EIectron/RadioNoob/Images/Transmitter/IMG20240410154644.jpg

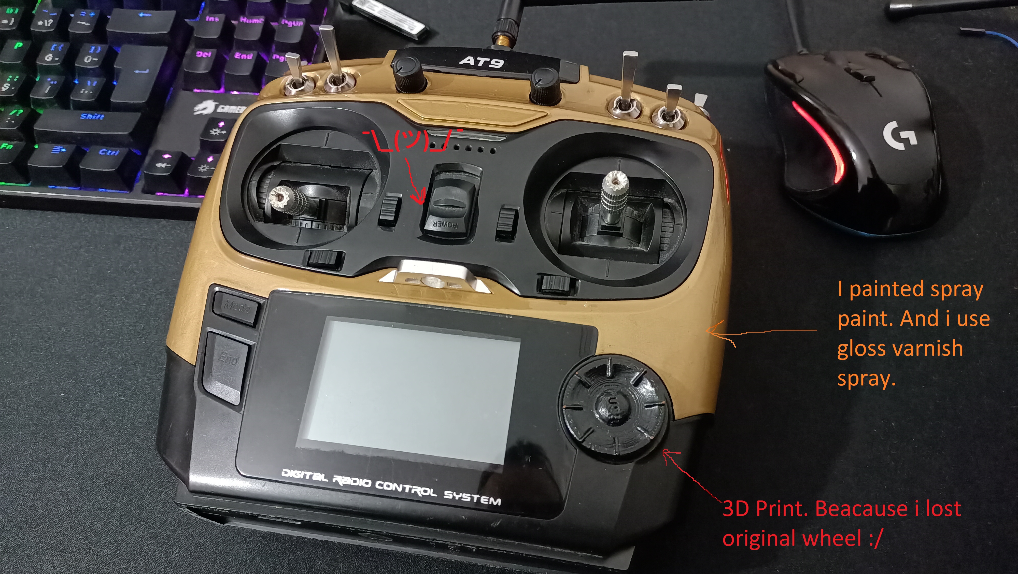
Images/Transmitter/IMG20240410154644.jpg
