EIectron/RadioNoob/Images/Transmitter/IMG20240410155039.jpg

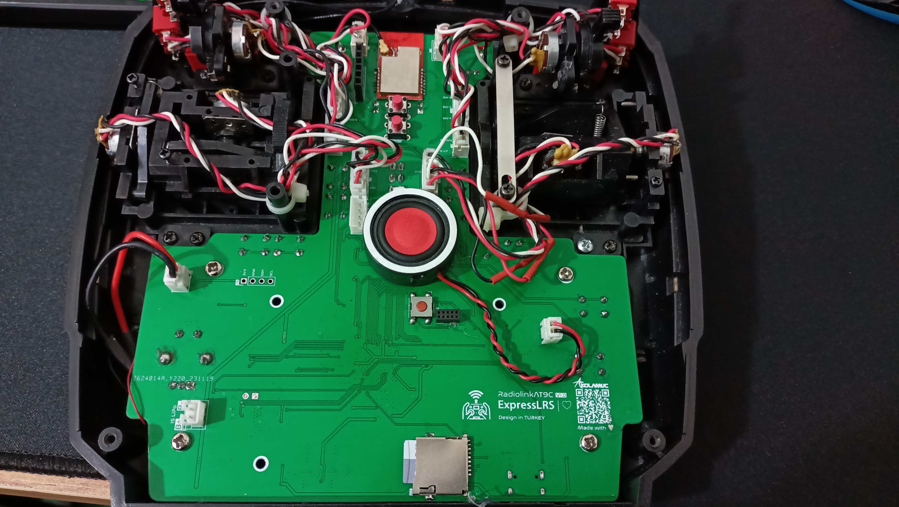
Images/Transmitter/IMG20240410155039.jpg
