EIectron/RadioNoob/Images/Transmitter/IMG20240410155045.jpg

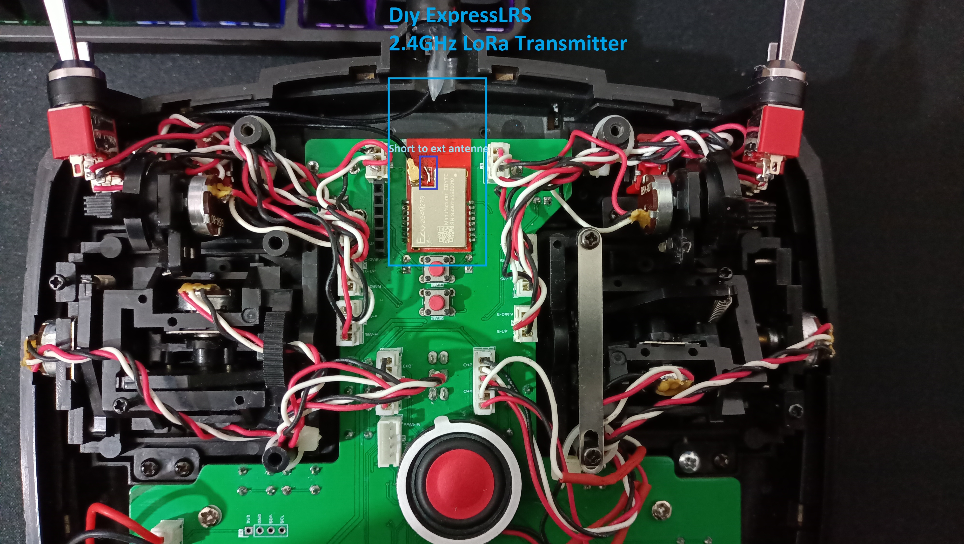
Images/Transmitter/IMG20240410155045.jpg
