EIectron/RadioNoob/Images/Transmitter/IMG20240410155447.jpg

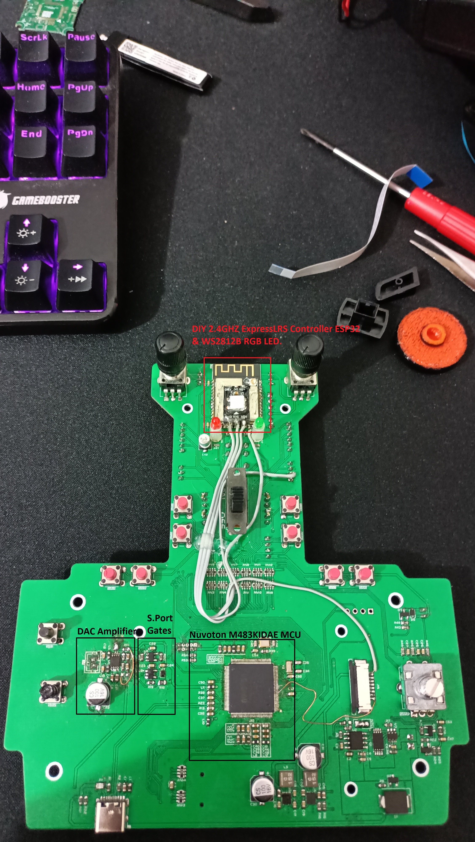
Images/Transmitter/IMG20240410155447.jpg
