EIectron/RadioNoob/Images/Transmitter/IMG20240410155505.jpg

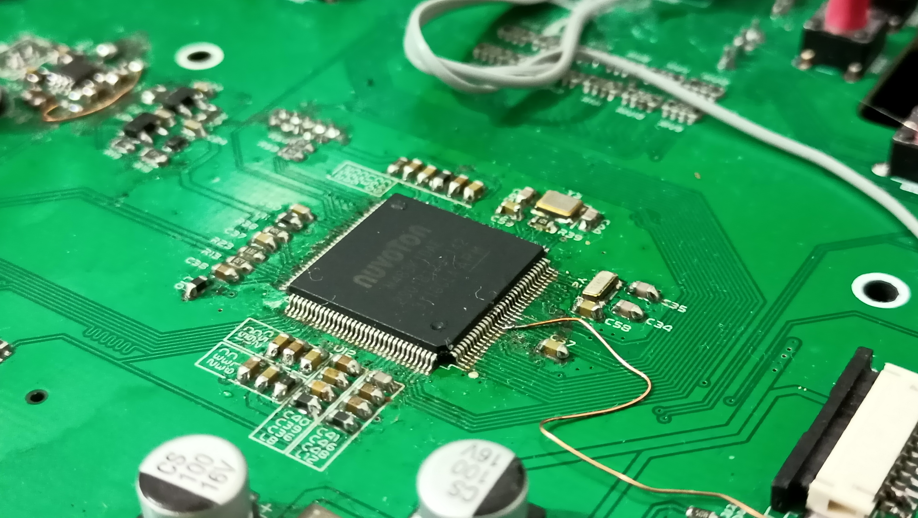
Images/Transmitter/IMG20240410155505.jpg
