EIectron/RadioNoob/Images/Transmitter/IMG20240410155515.jpg

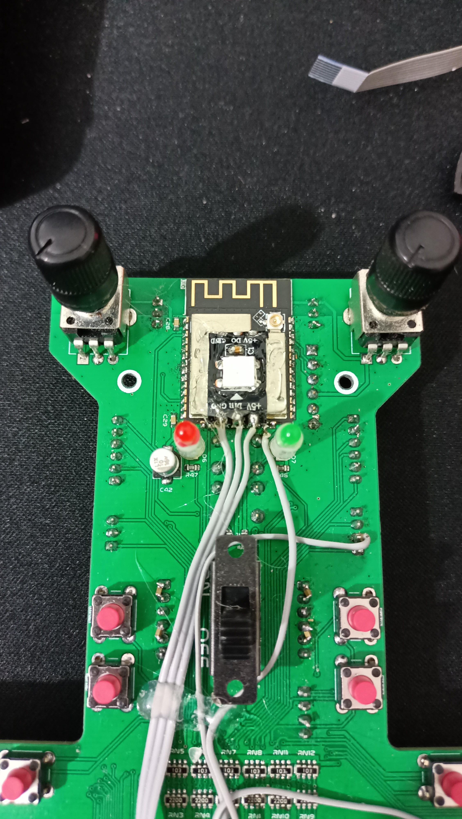
Images/Transmitter/IMG20240410155515.jpg
