EIectron/RadioNoob/Images/Transmitter/IMG20240410155539.jpg

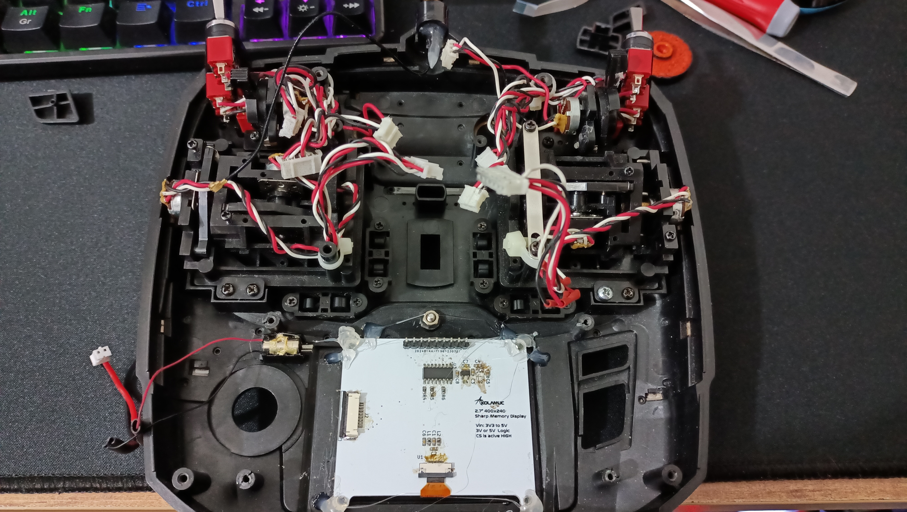
Images/Transmitter/IMG20240410155539.jpg
