EIectron/RadioNoob/Images/Transmitter/IMG20240410155607.jpg

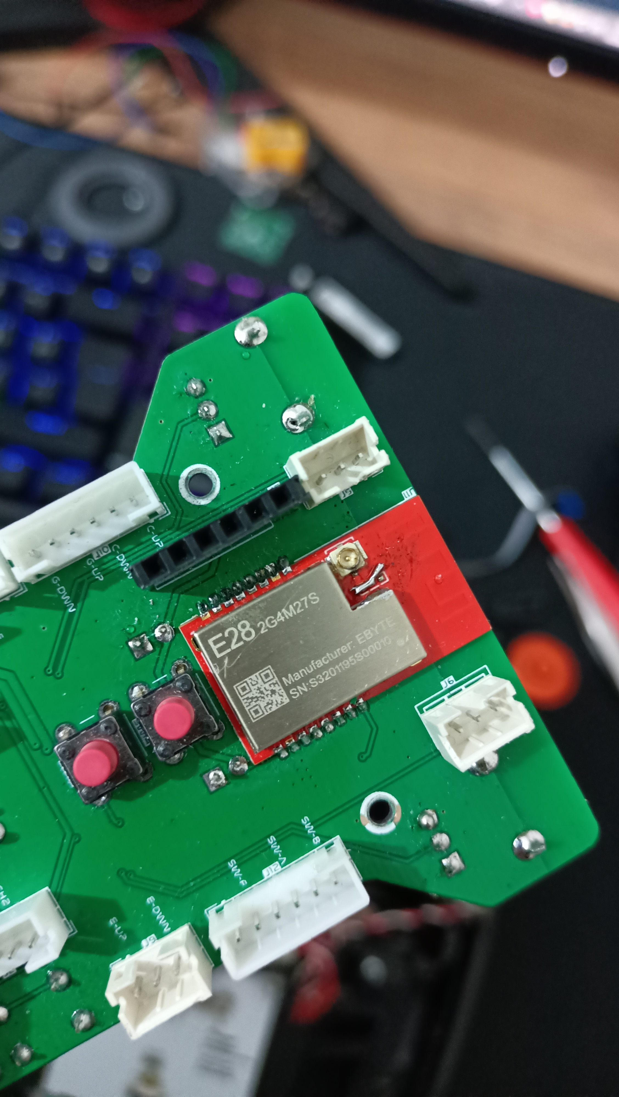
Images/Transmitter/IMG20240410155607.jpg
