EIectron/RadioNoob/Images/Transmitter/IMG20240410155912.jpg

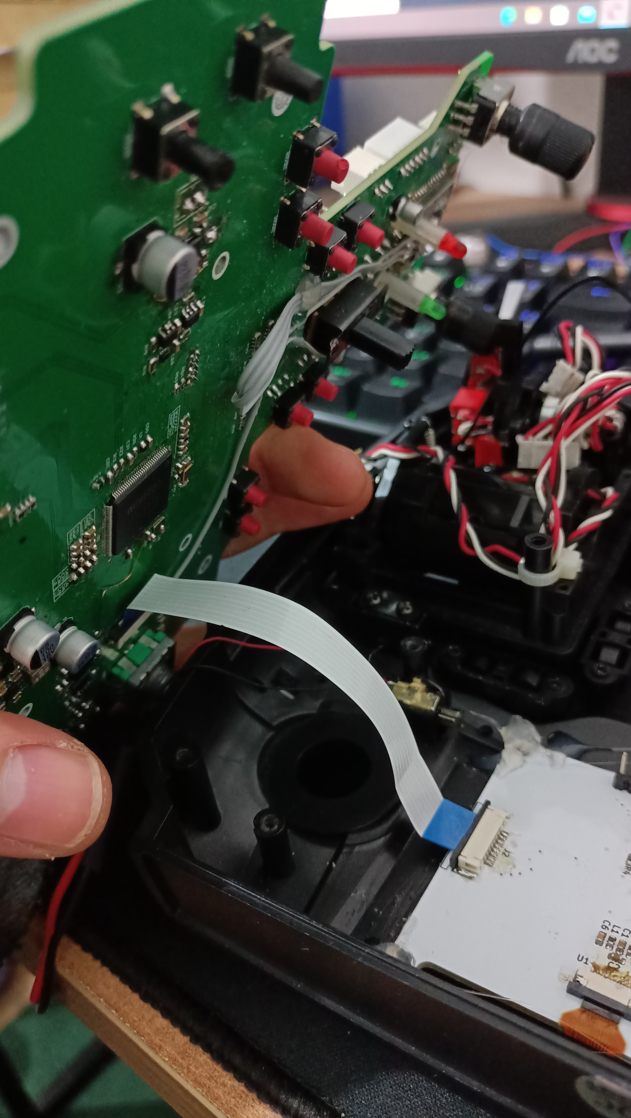
Images/Transmitter/IMG20240410155912.jpg
