EIectron/RadioNoob/Images/Transmitter/IMG20240410161644.jpg

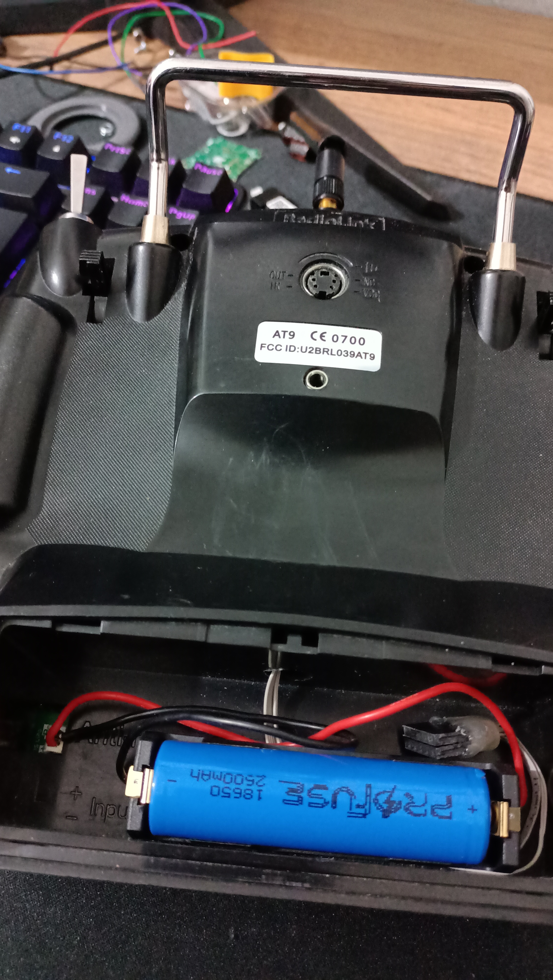
Images/Transmitter/IMG20240410161644.jpg
