EIectron/RadioNoob/Hardware/Documents/TX16S v2 schematic single page PDF.pdf

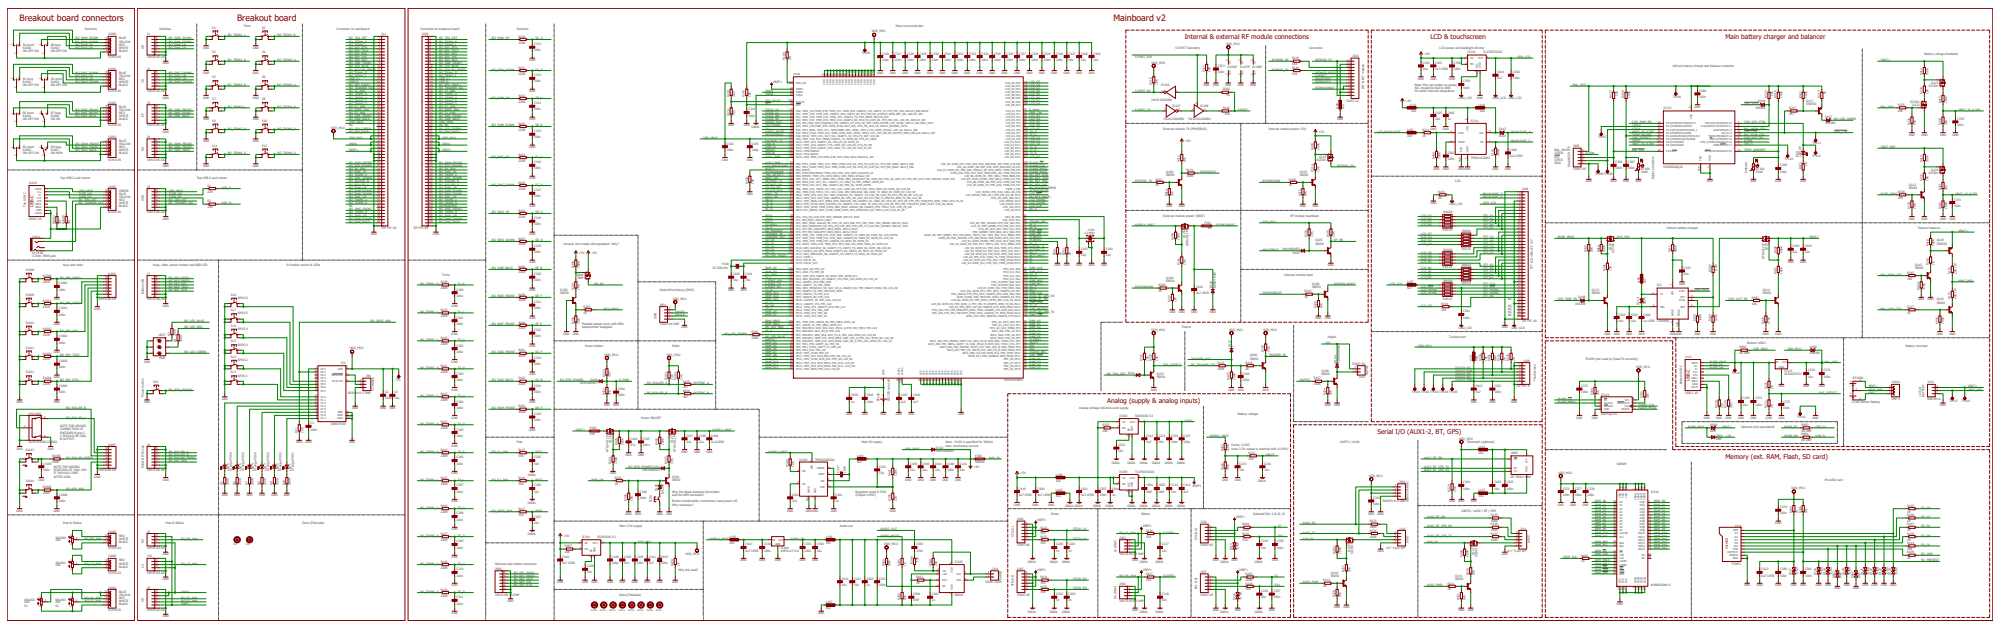
[picture p48: page 1]

AB CDSC long SD short

LCD power and backlight dimmer

Lithium battery charge and balance controller

GND
Note: this cap makes no sense,
N/C should be tied to GND

for better thermal dissipation.

BALANCER ICP GND ICPCK RST ICPDA BAL_VDD

Top USB-C and trainer

RS LS VR USB

Unused, but mostly still populated. Why?

Keys, roller, power button and RGB-LED

Roller & MDL key Buttons left

Serial-Wire-Debug (SWD)

Possible design error with NPN,

FLASH (not used by OpenTX currently)

Analog (supply & analog inputs)

Analog voltage reference and supply

Factor: 0.245
(max 3.3V output is reached with 13.45V)

Memory (ext. RAM, Flash, SD card)

GND 5 VIN 8 VBST 7 SW 6 IC103

VDD 27 VSS 41 A11 35 NC 36 CKE 37 CLK 38 NC 40 UDQM 39

Why the diode between the button
and the NPN transistor?
Button functionality: momentary hard power off.
Why necessary?

LS (DNP) RS (DNP)

Optional side button connector

VDD 6 GND 7 -IN 4 +IN 3 BYP 2 SD 1 VO1 5 VO2 8 IC105 C431 C211 C402 C352
