EIectron/RadioNoob/Hardware/Documents/L-KLS1-207-2-10-S.PDF

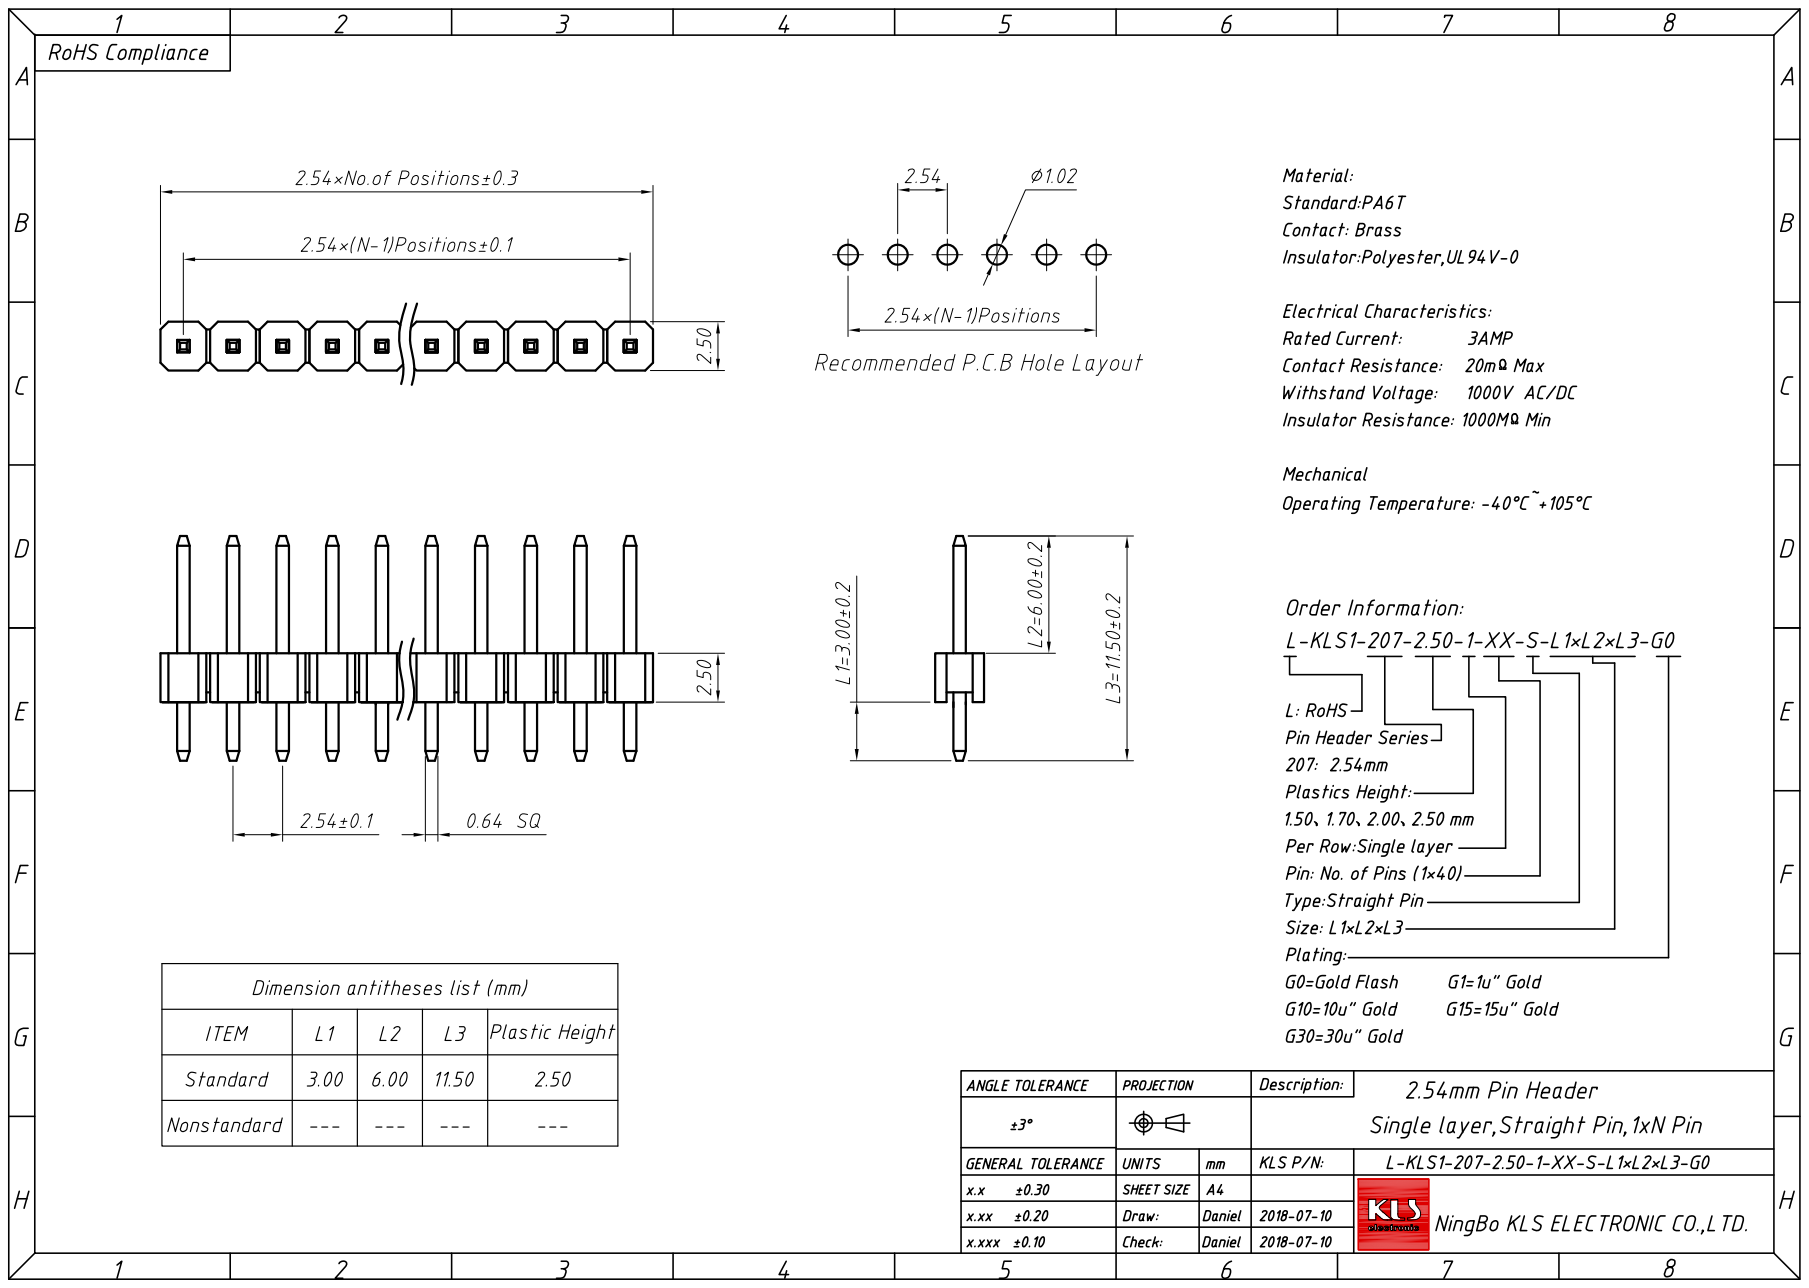
[picture p61: page 1]

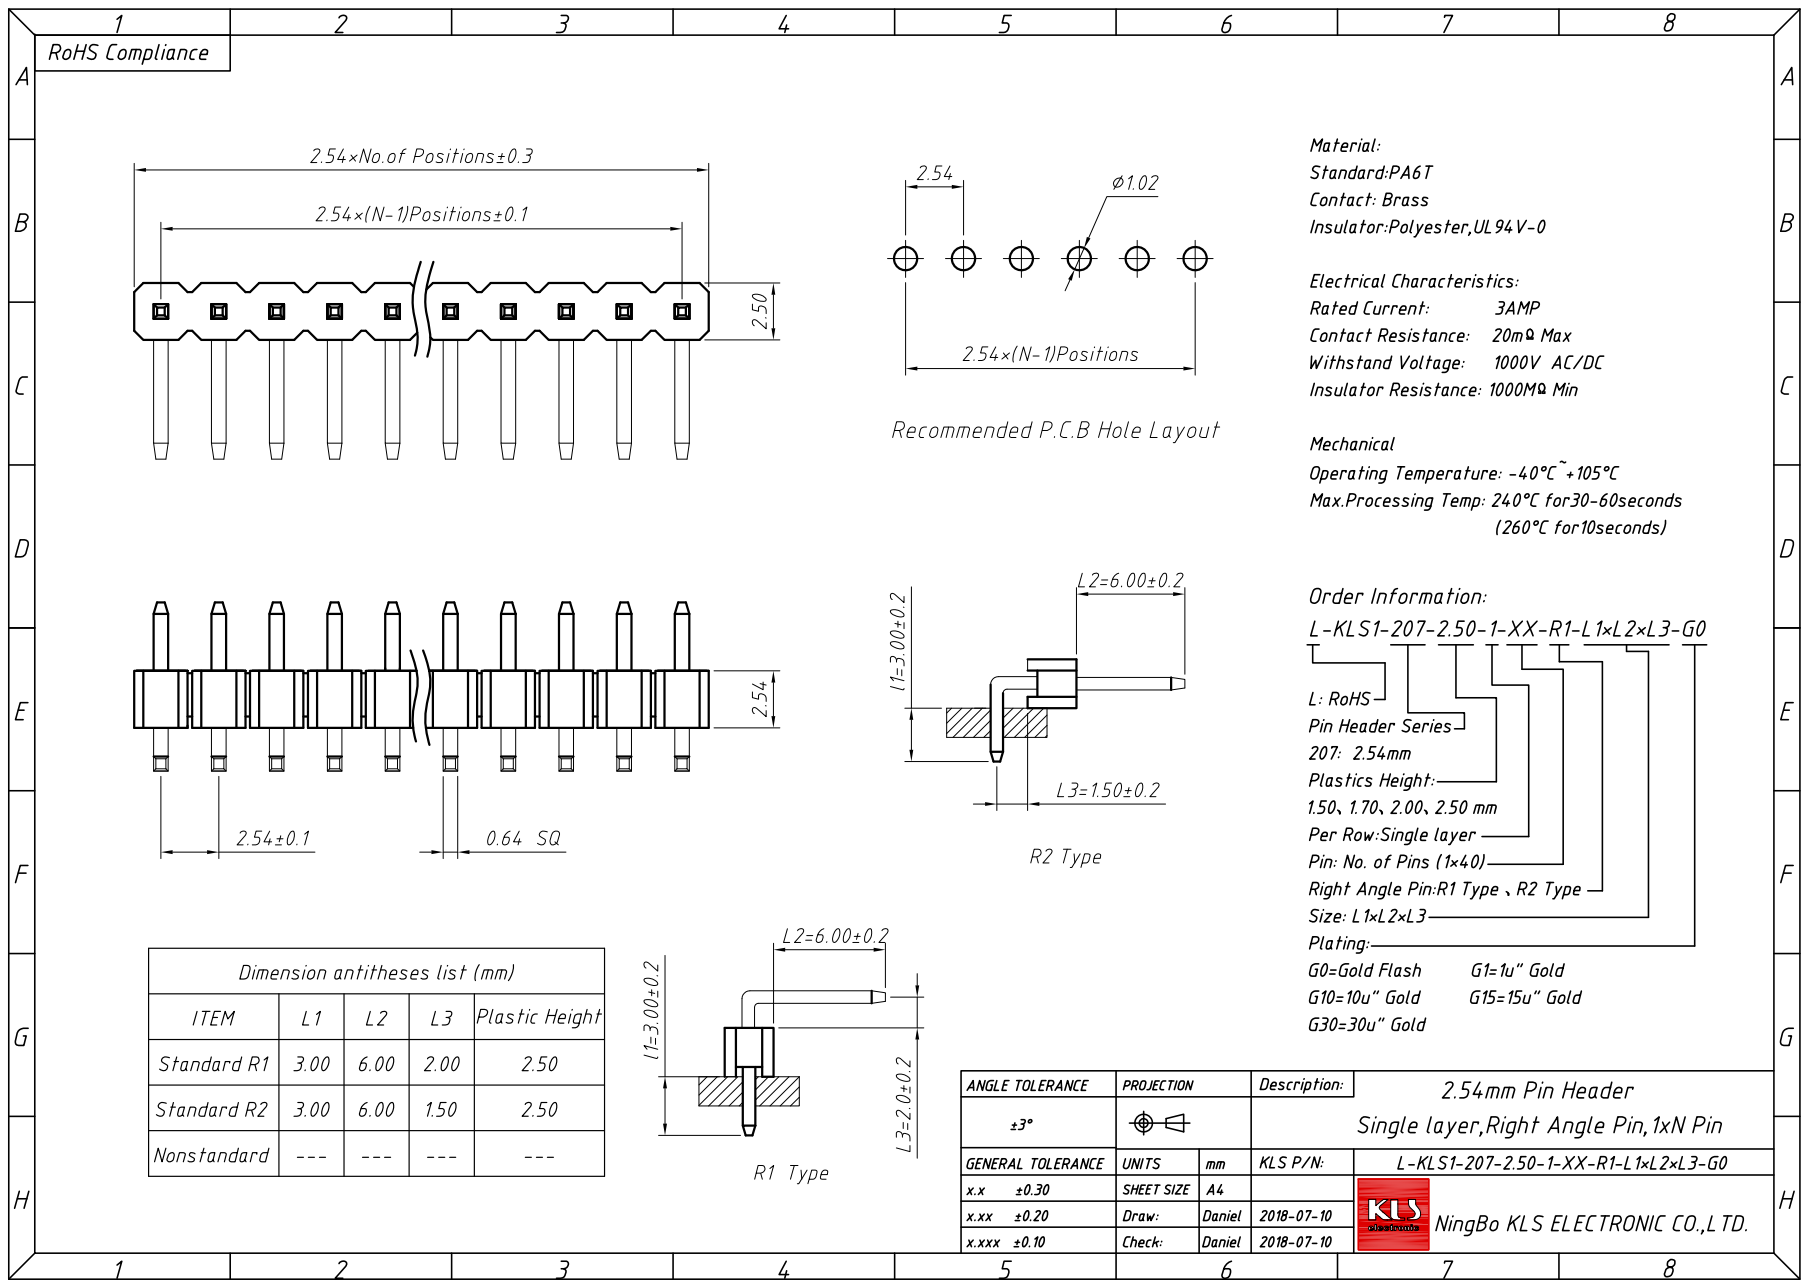
[picture p62: page 2]

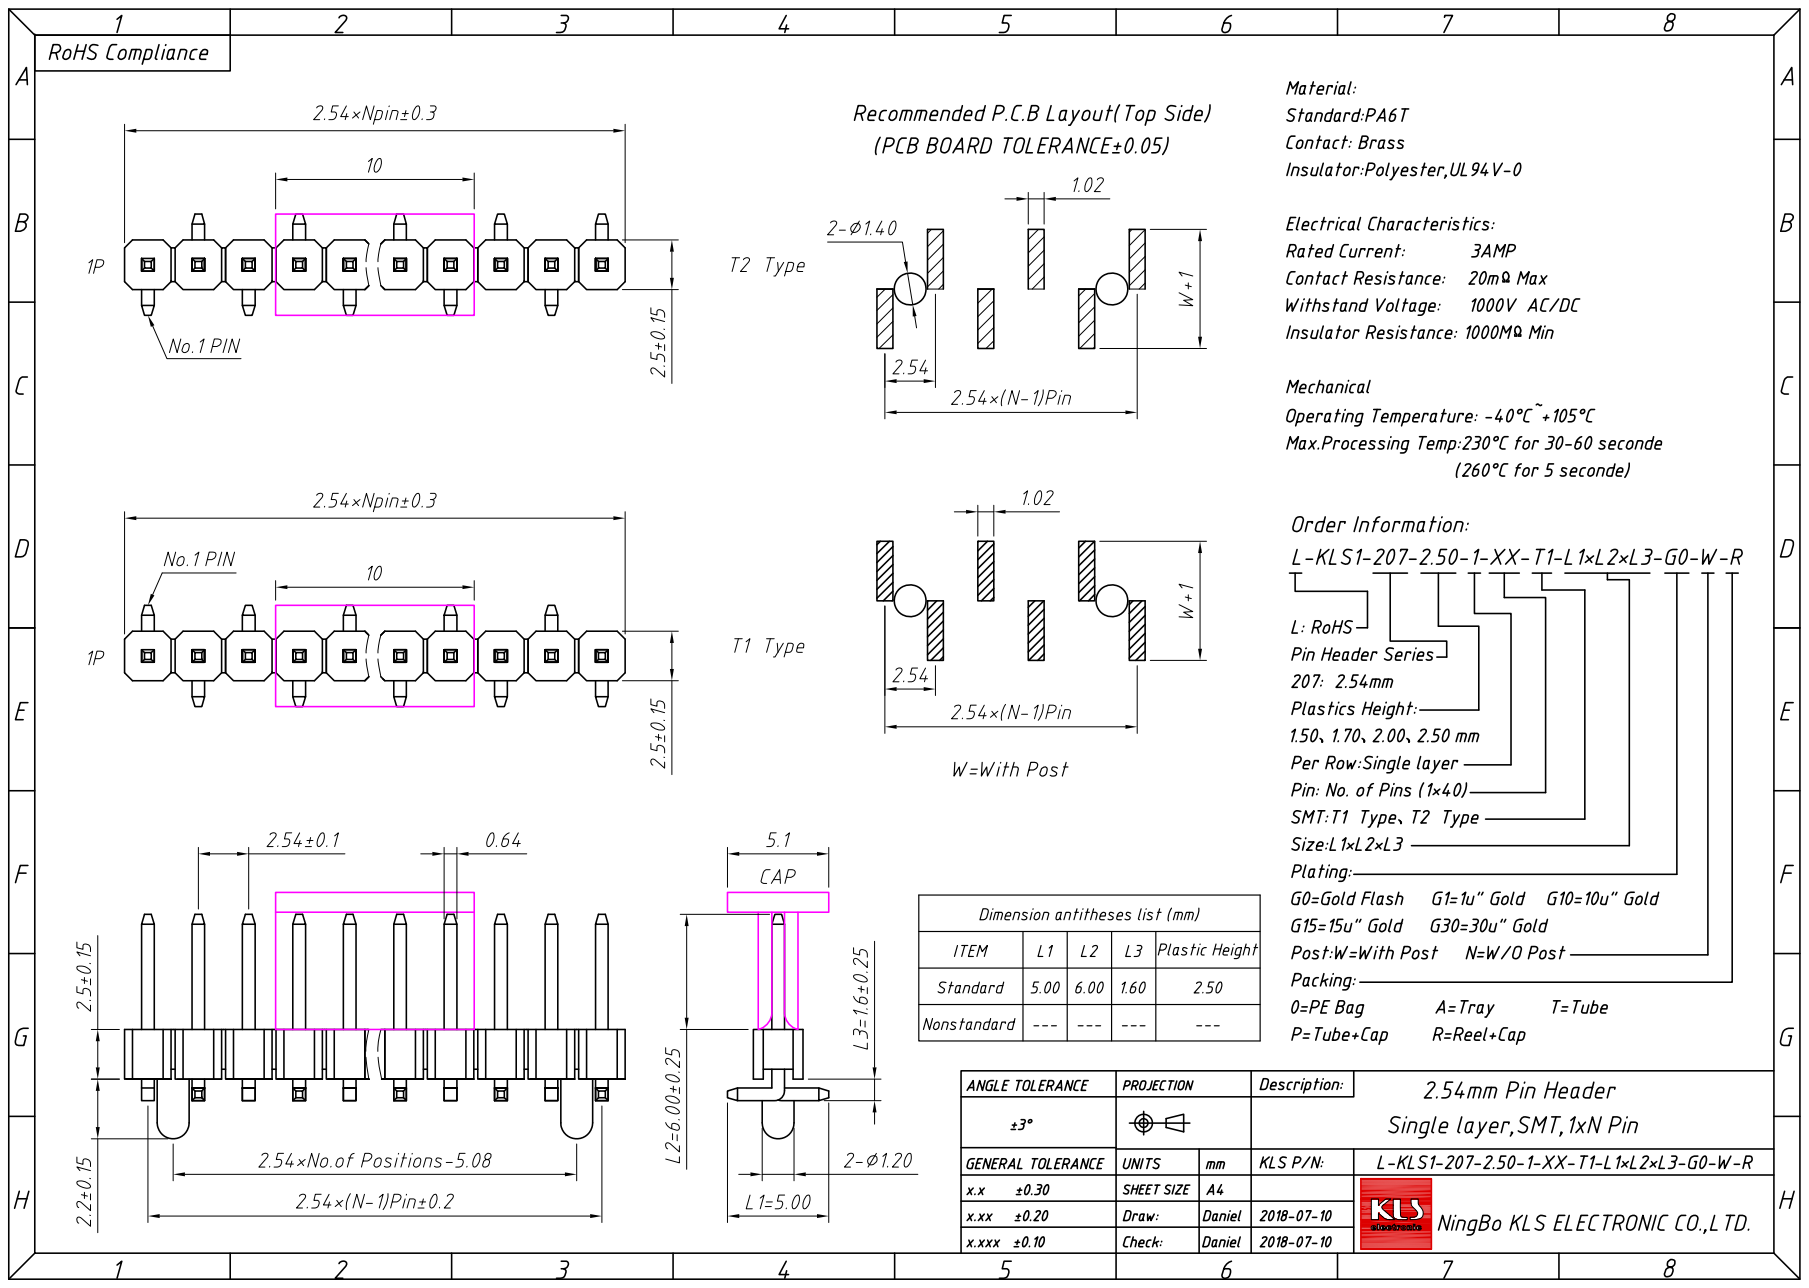
[picture p63: page 3]

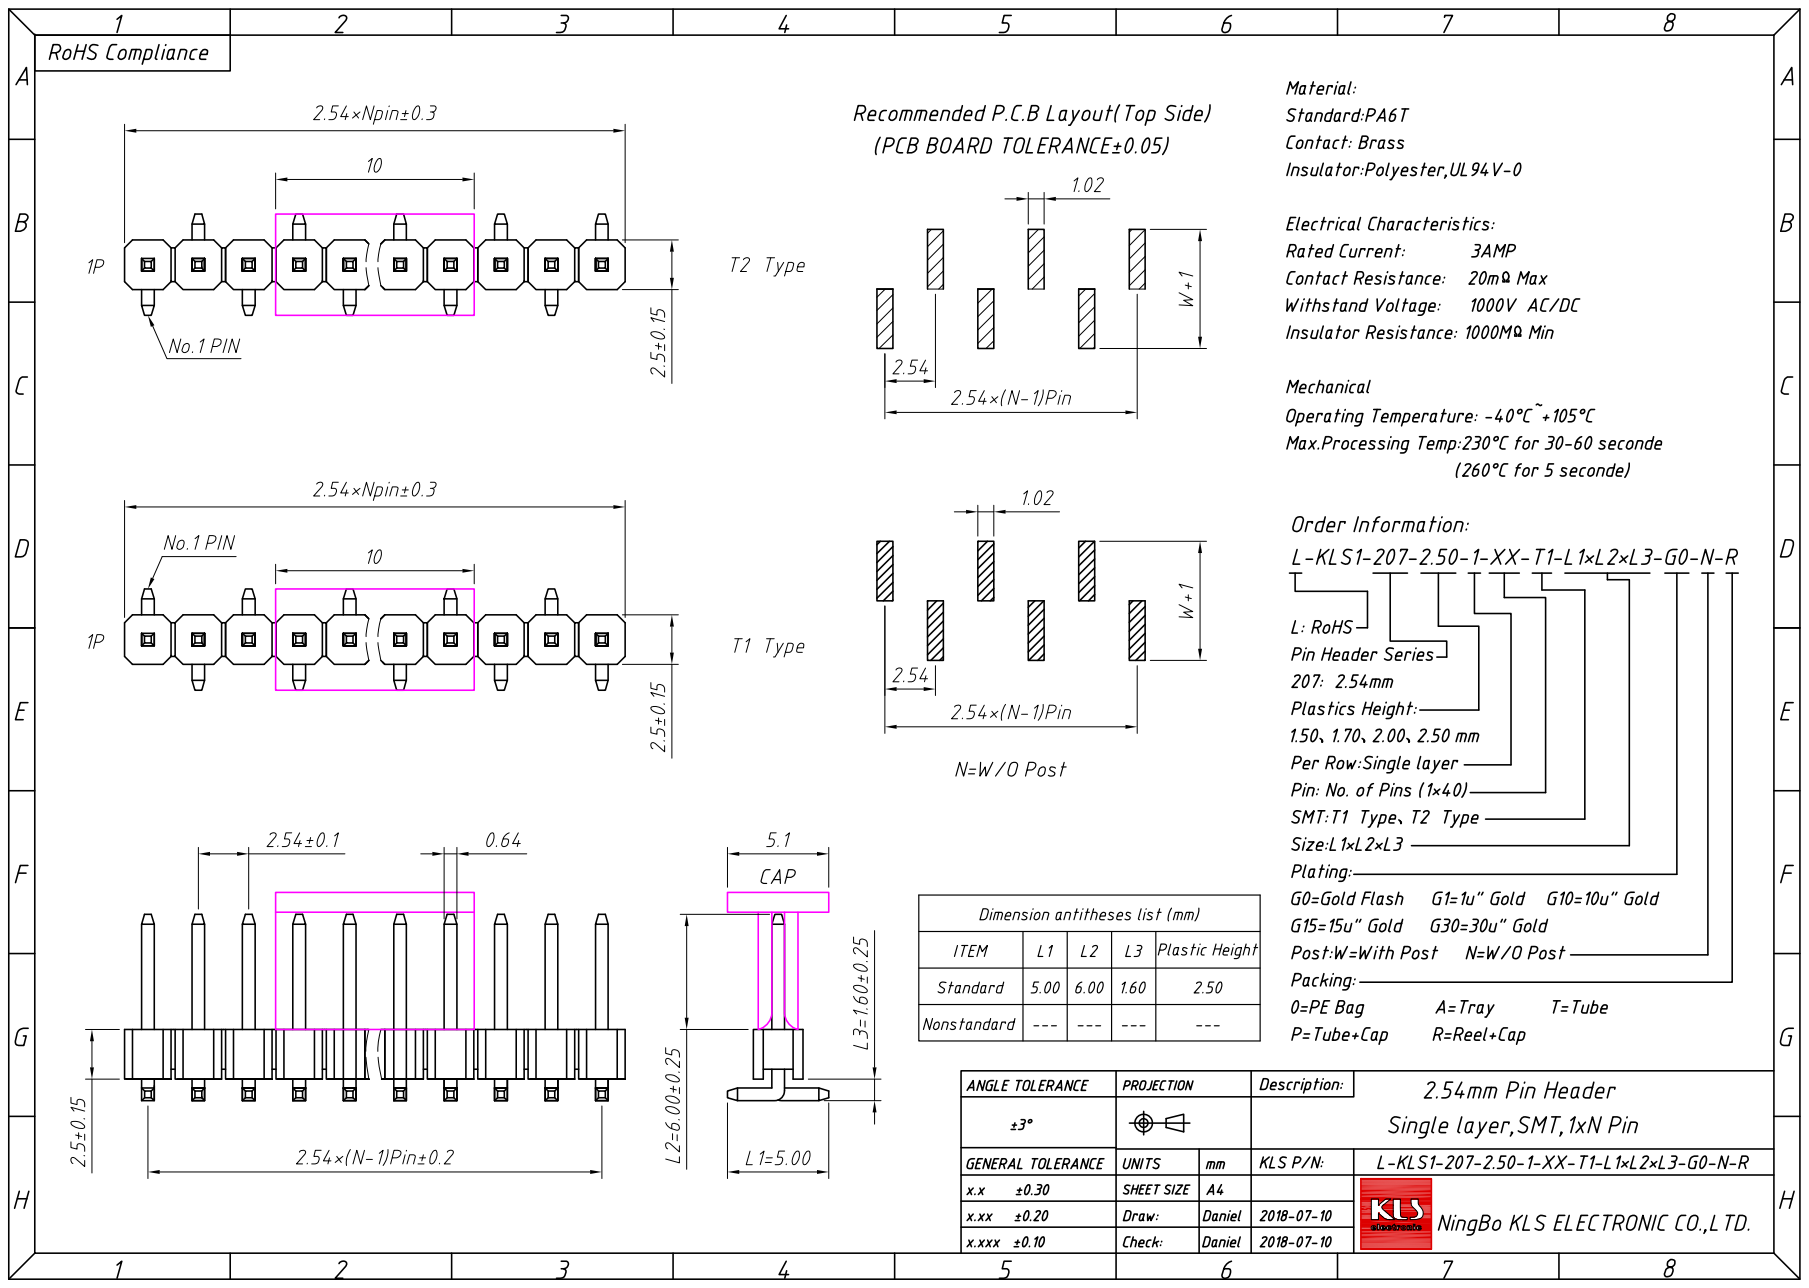
[picture p64: page 4]

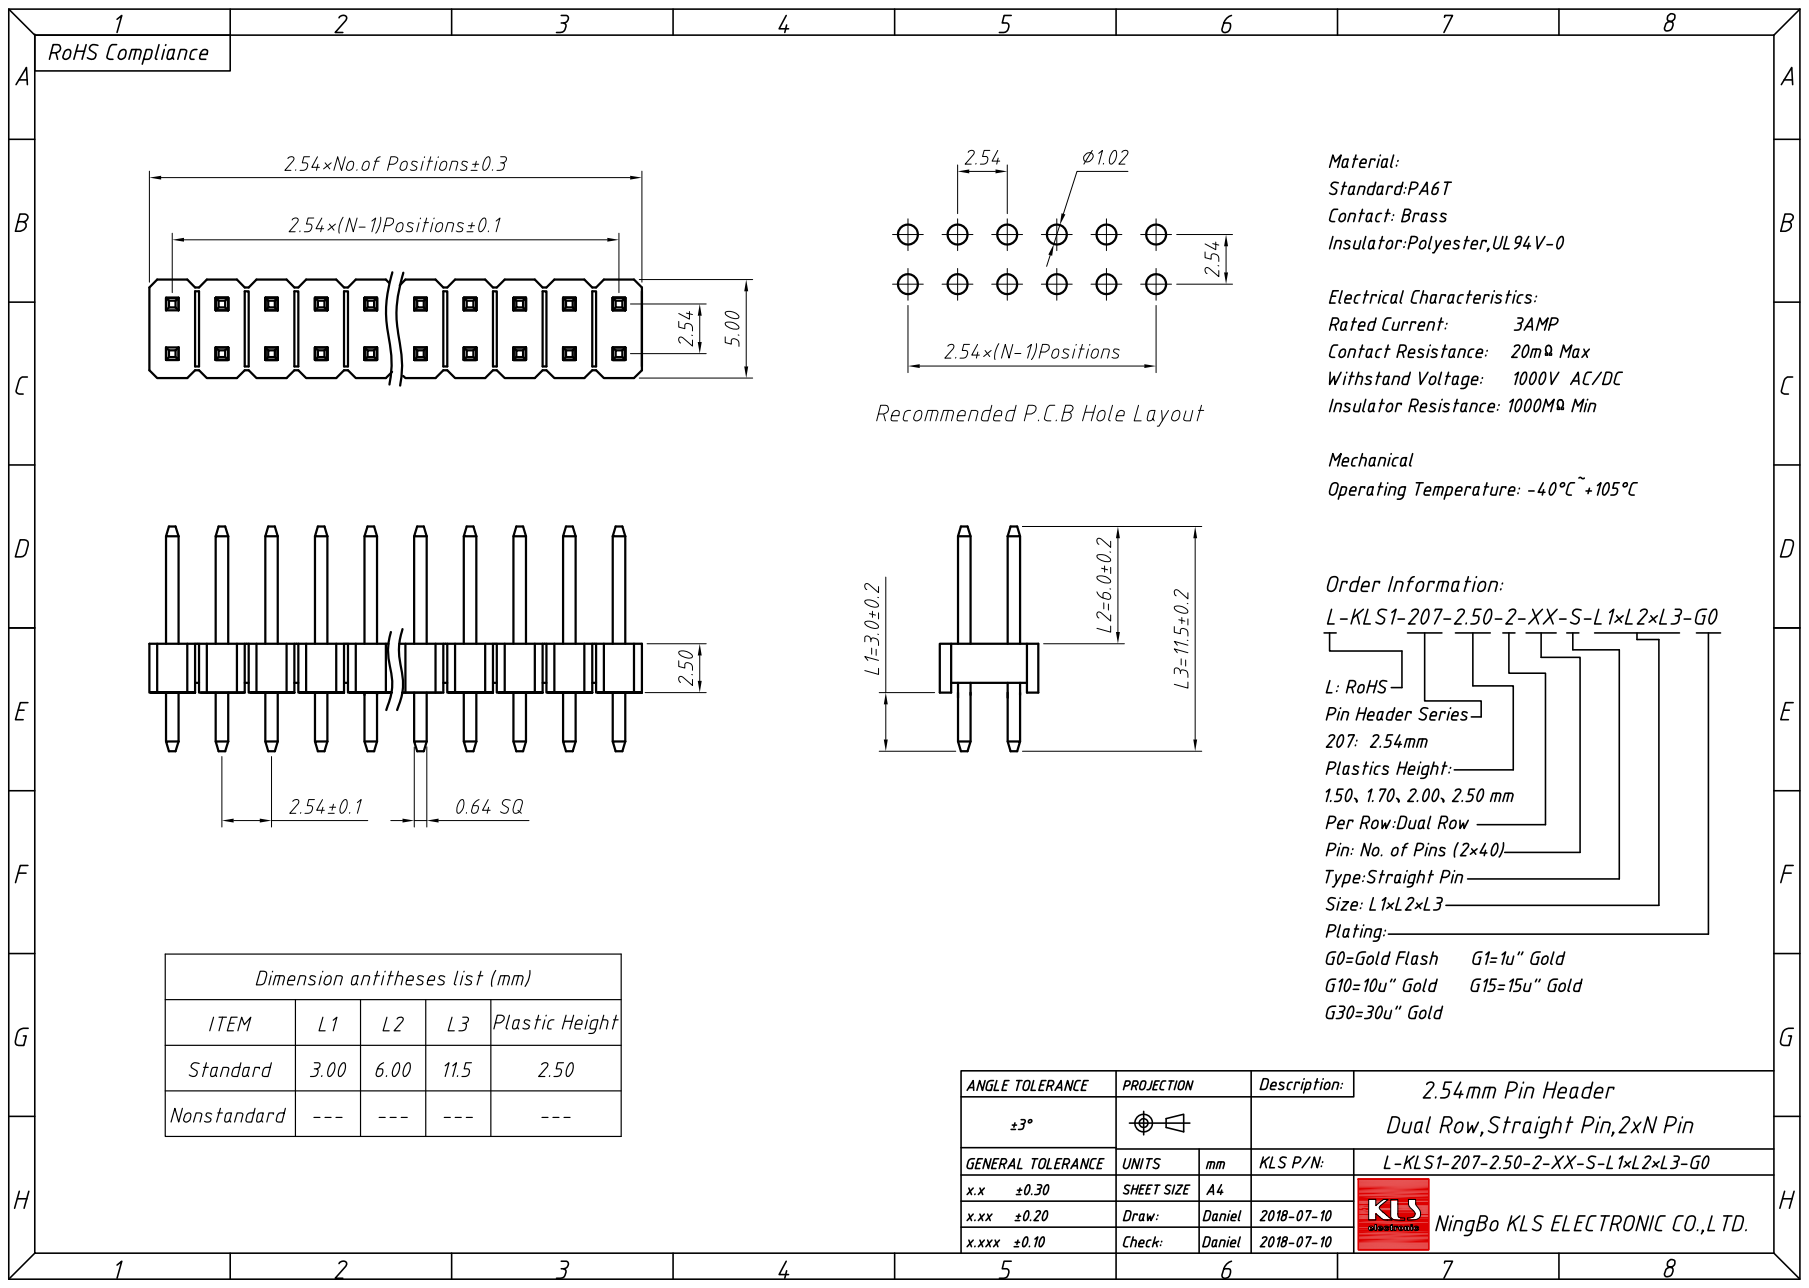
[picture p65: page 5]

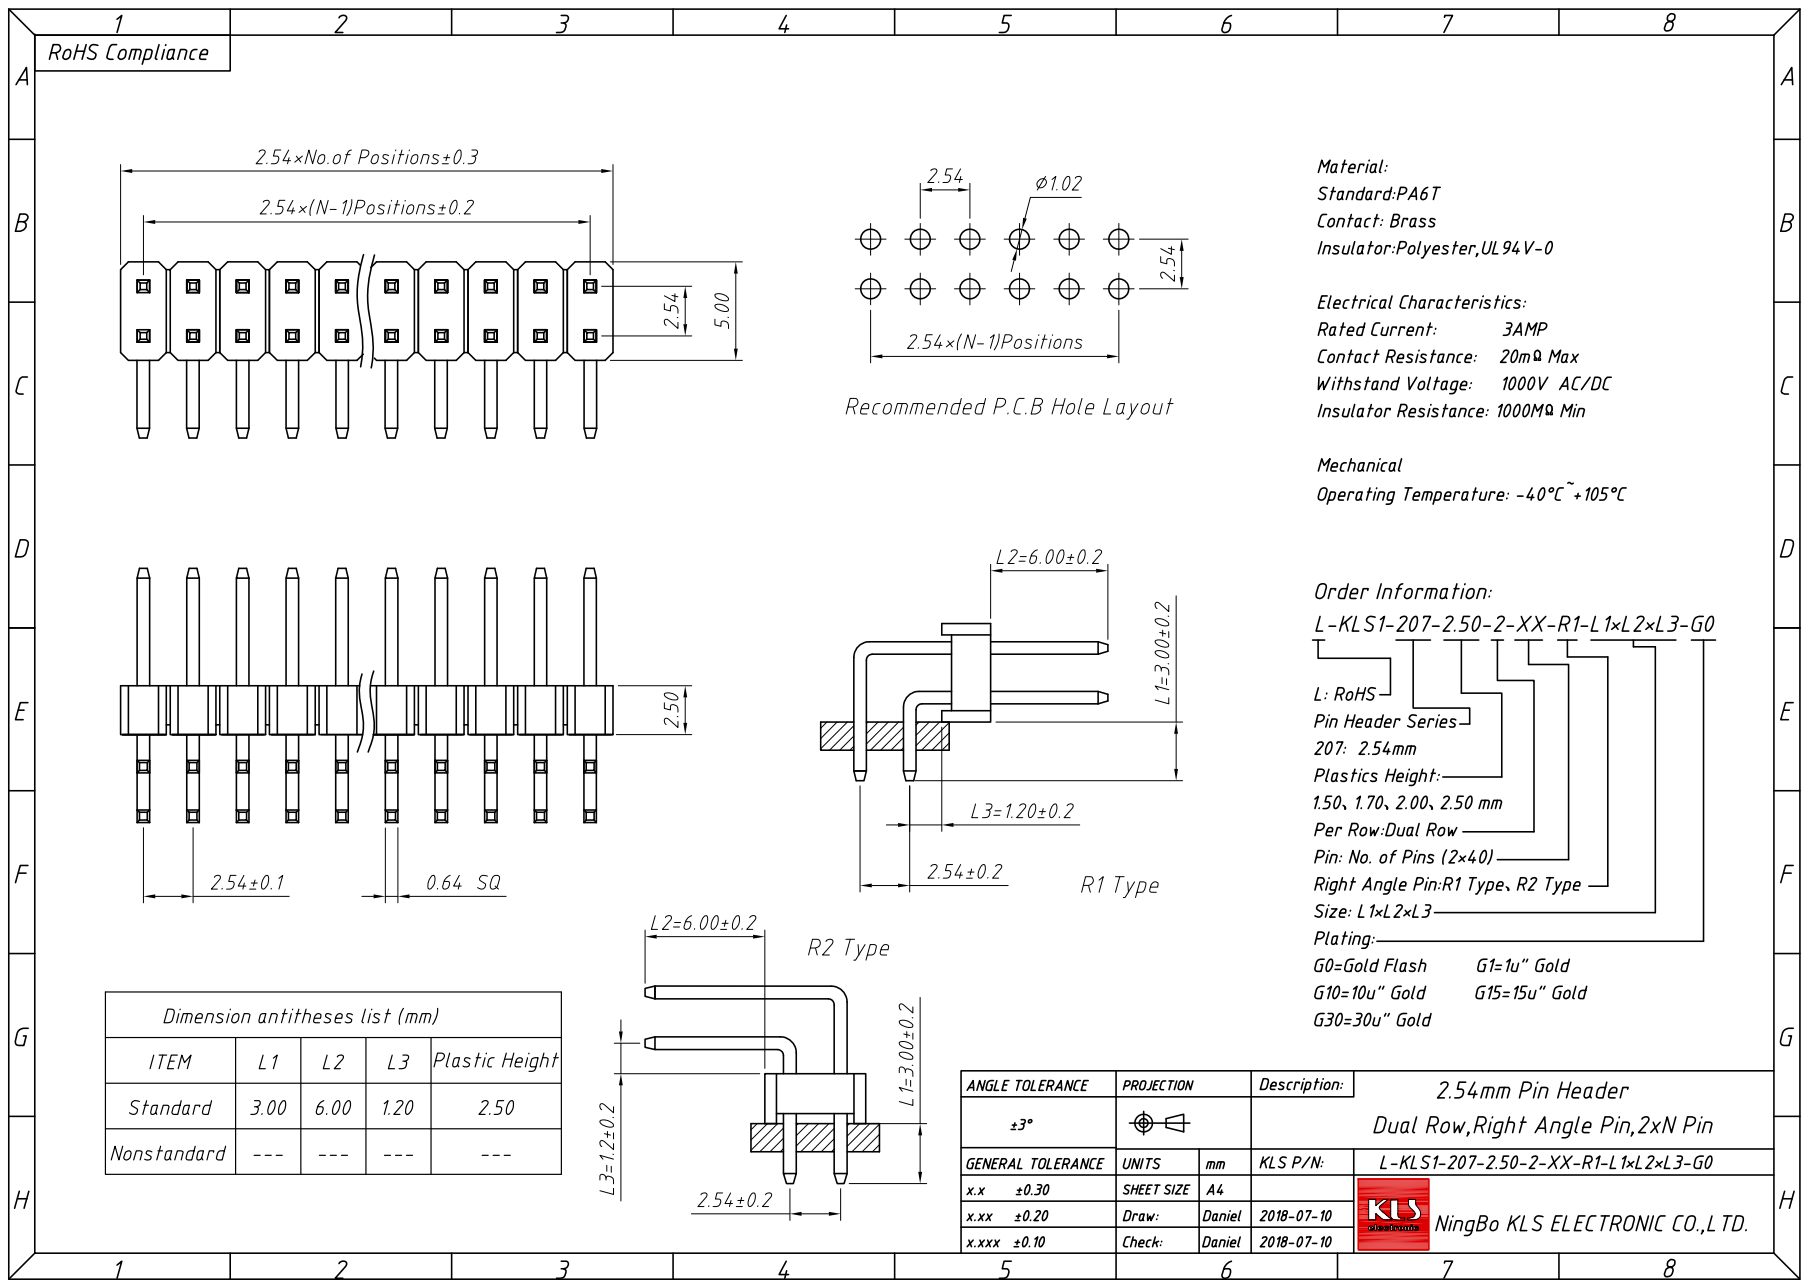
[picture p66: page 6]

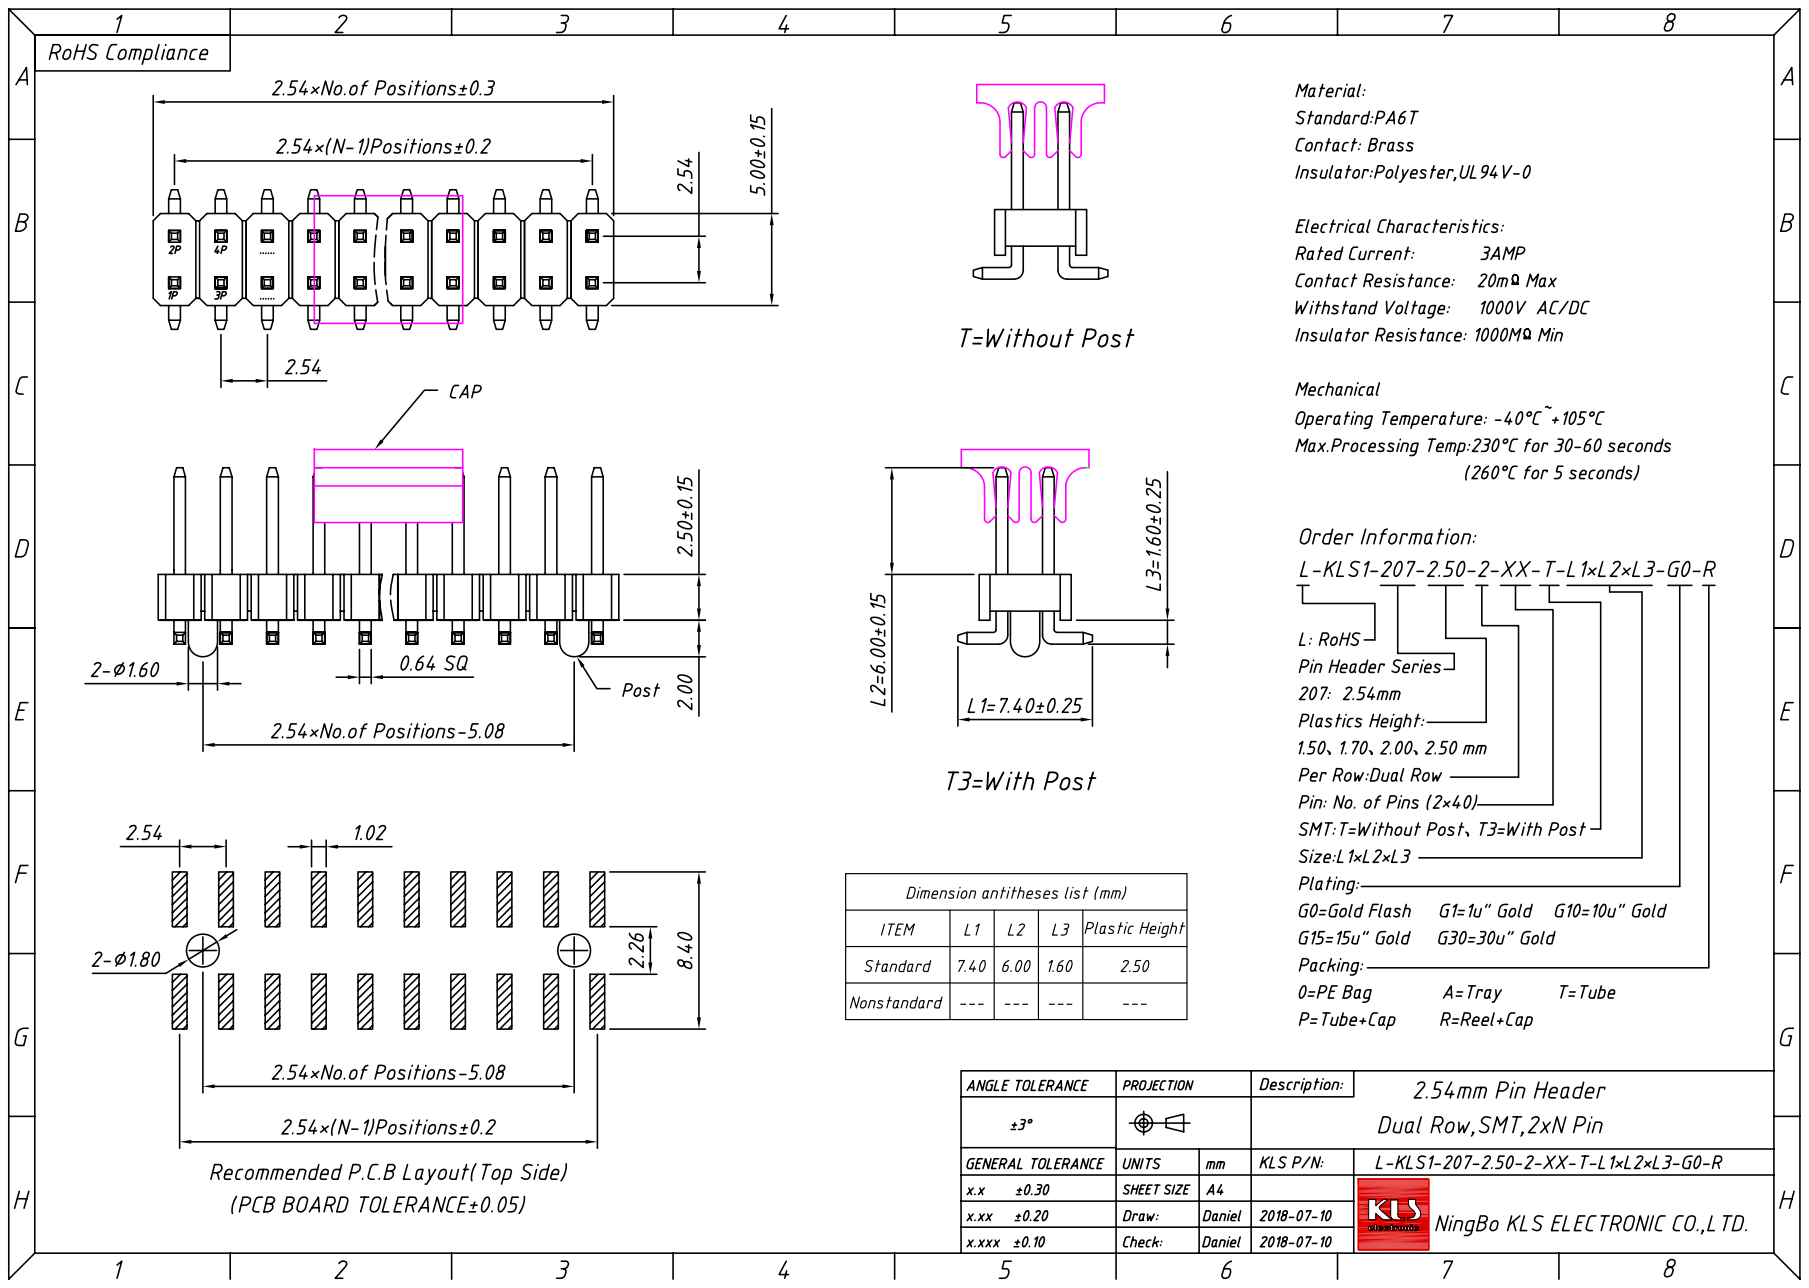
[picture p67: page 7]
