EIectron/RadioNoob/Hardware/Documents/L-KLS1-TF-003-H1.85-R.PDF

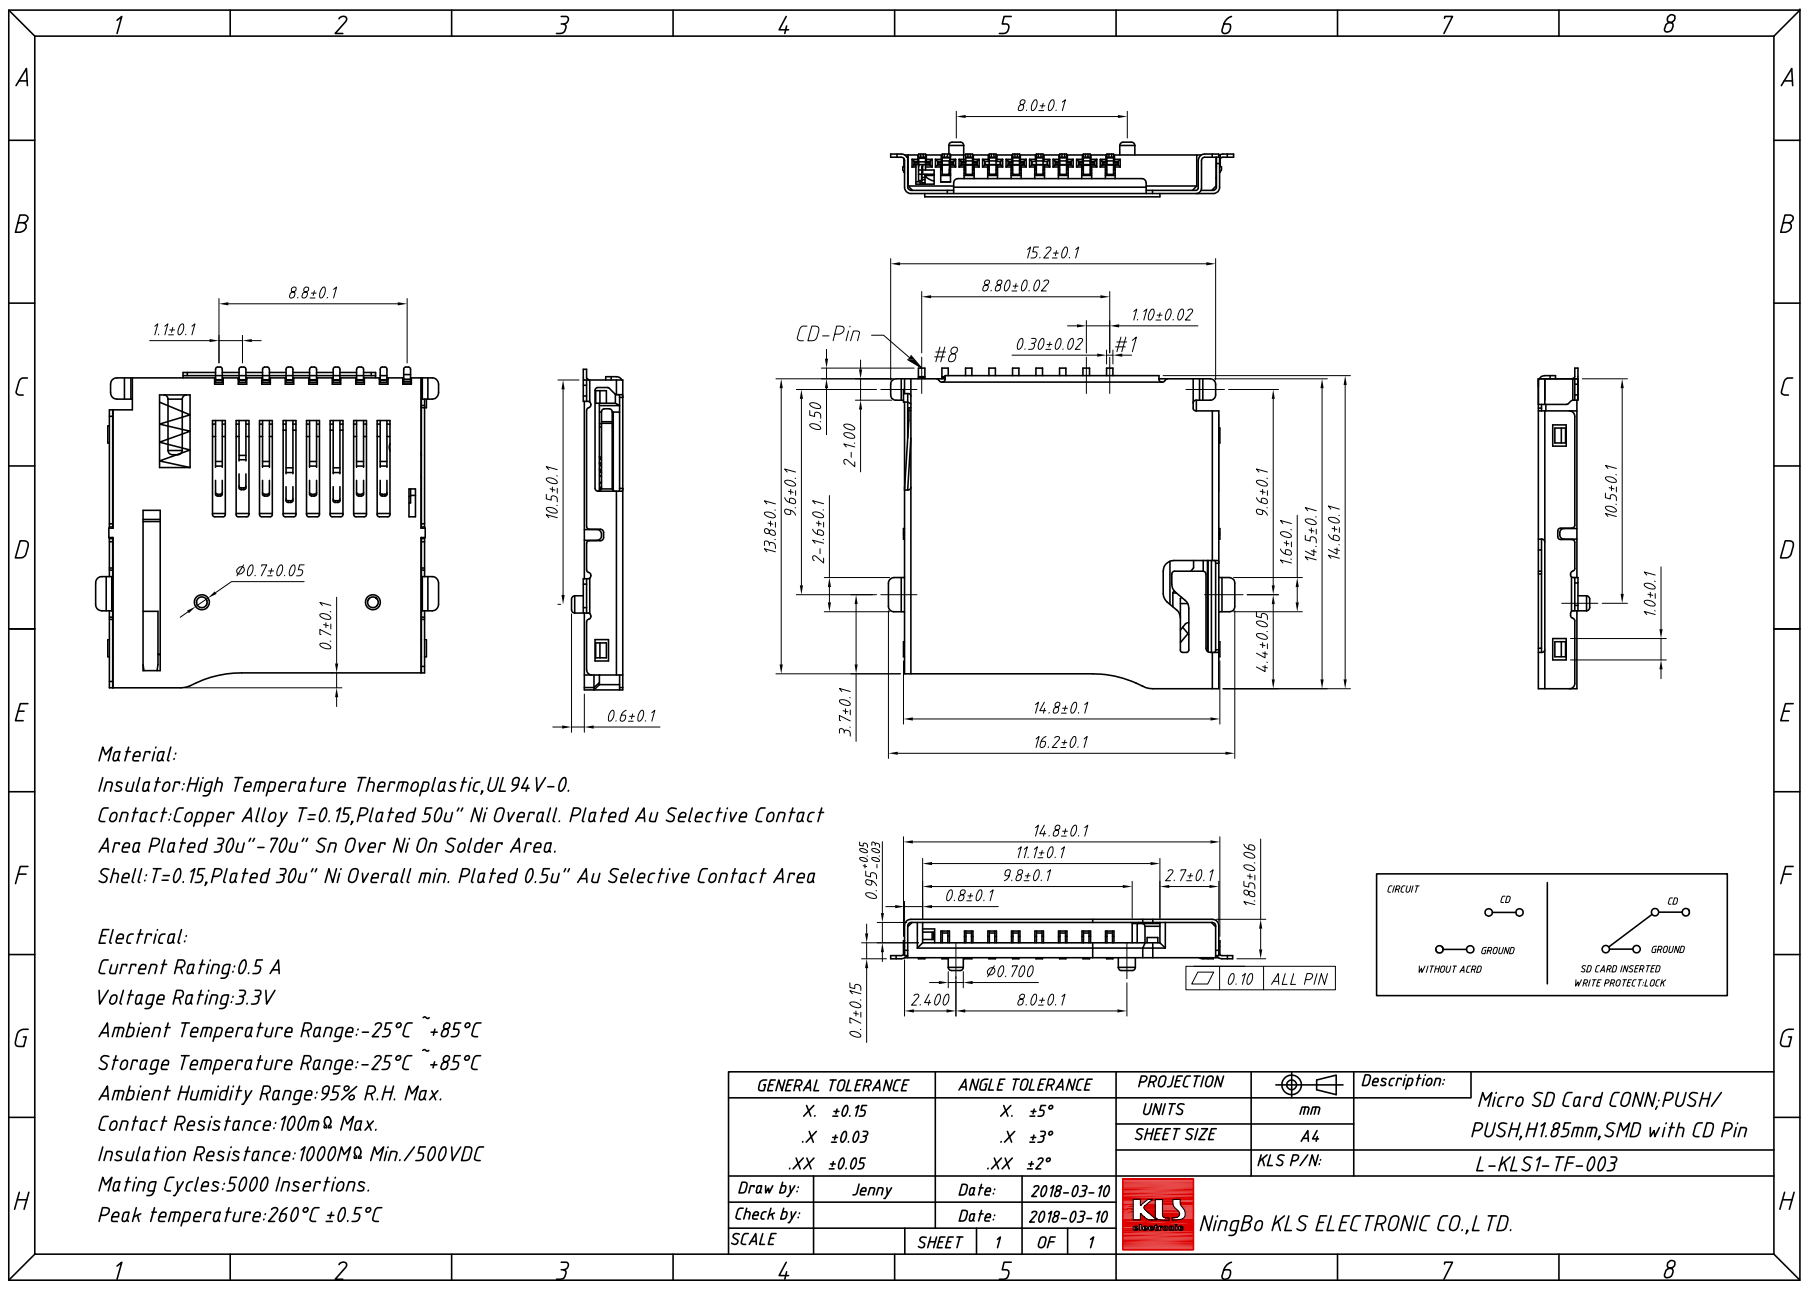
[picture p68: page 1]

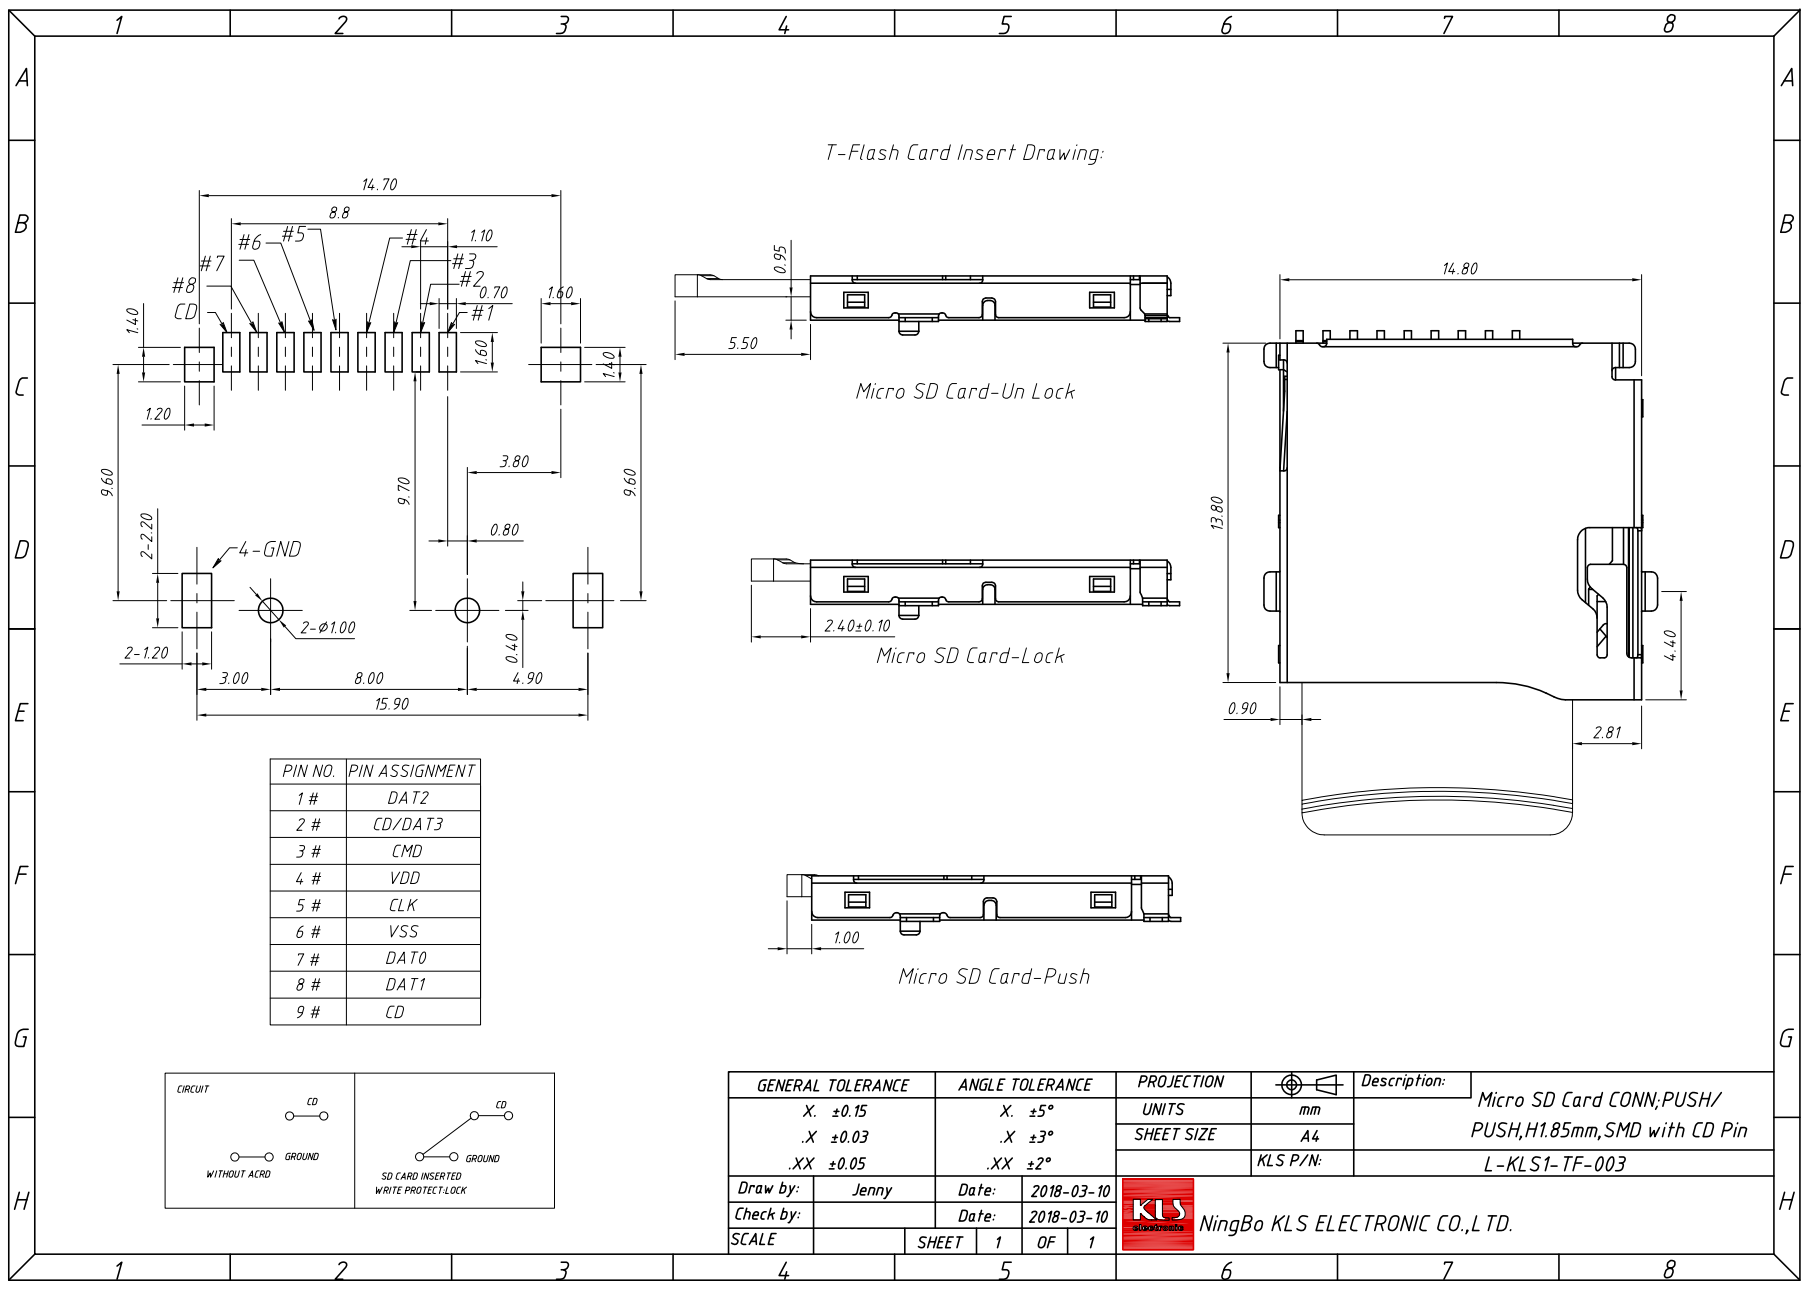
[picture p69: page 2]
