EIectron/RadioNoob/Hardware/Documents/Resistor_Royalohm.pdf

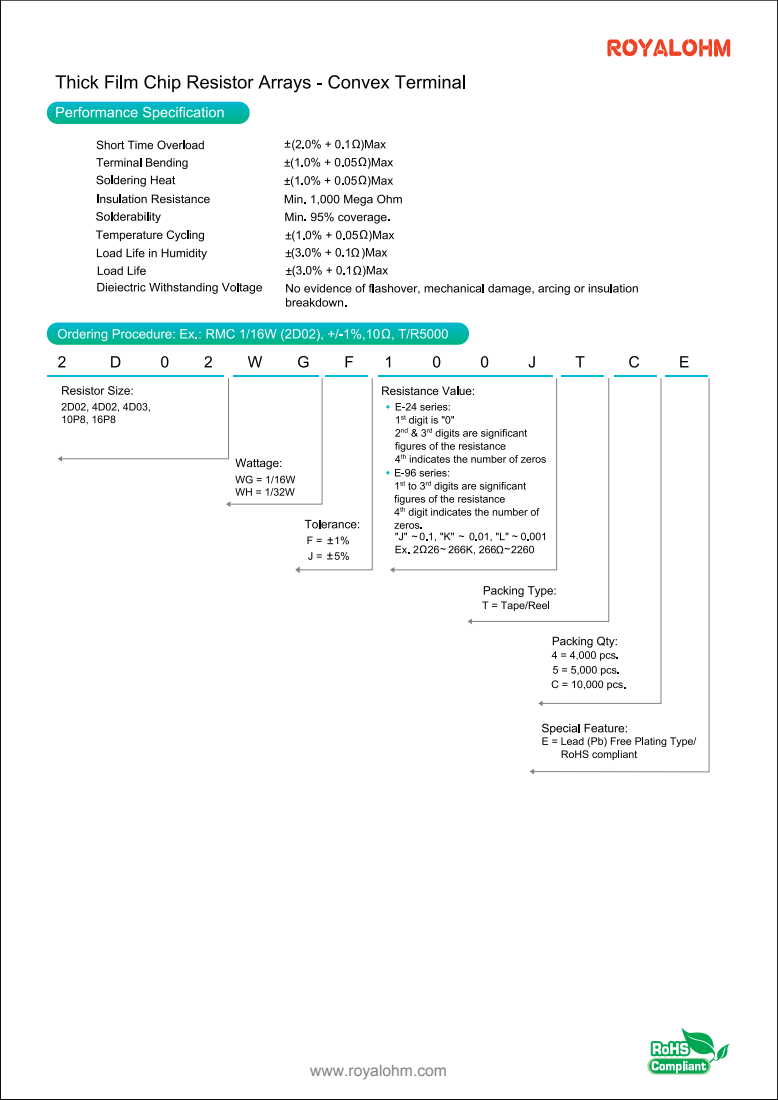
[picture p70: page 1]

www.royalohm.com

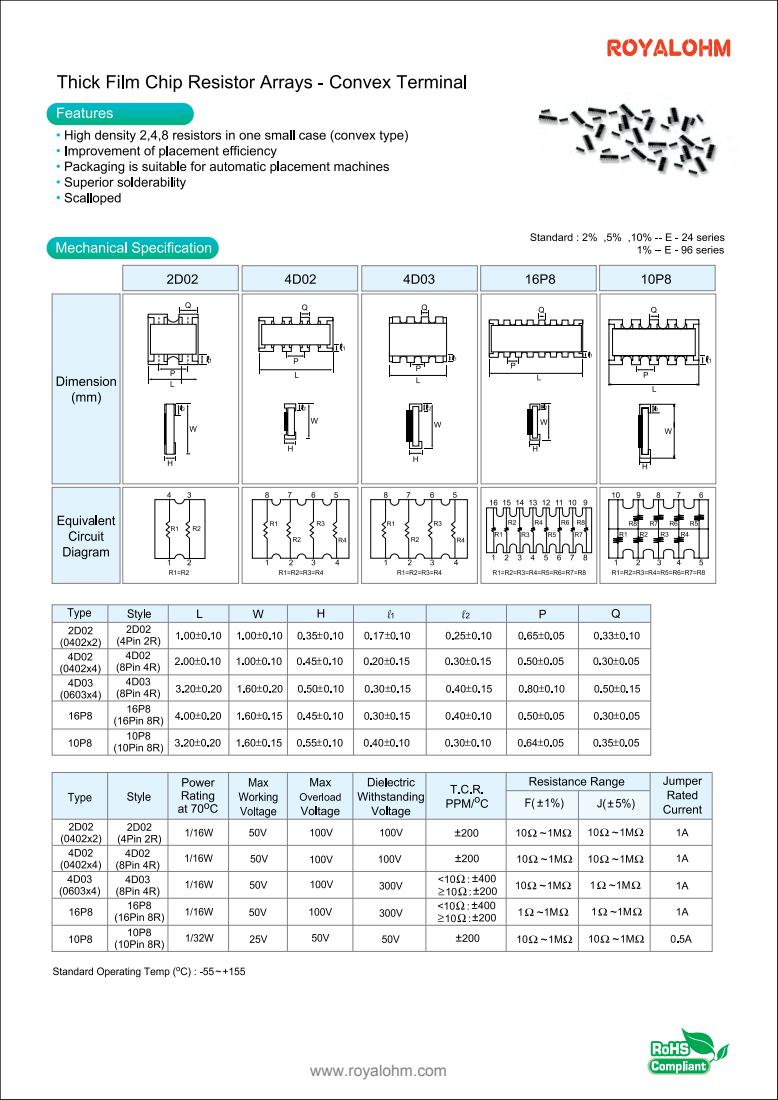
[picture p71: page 2]

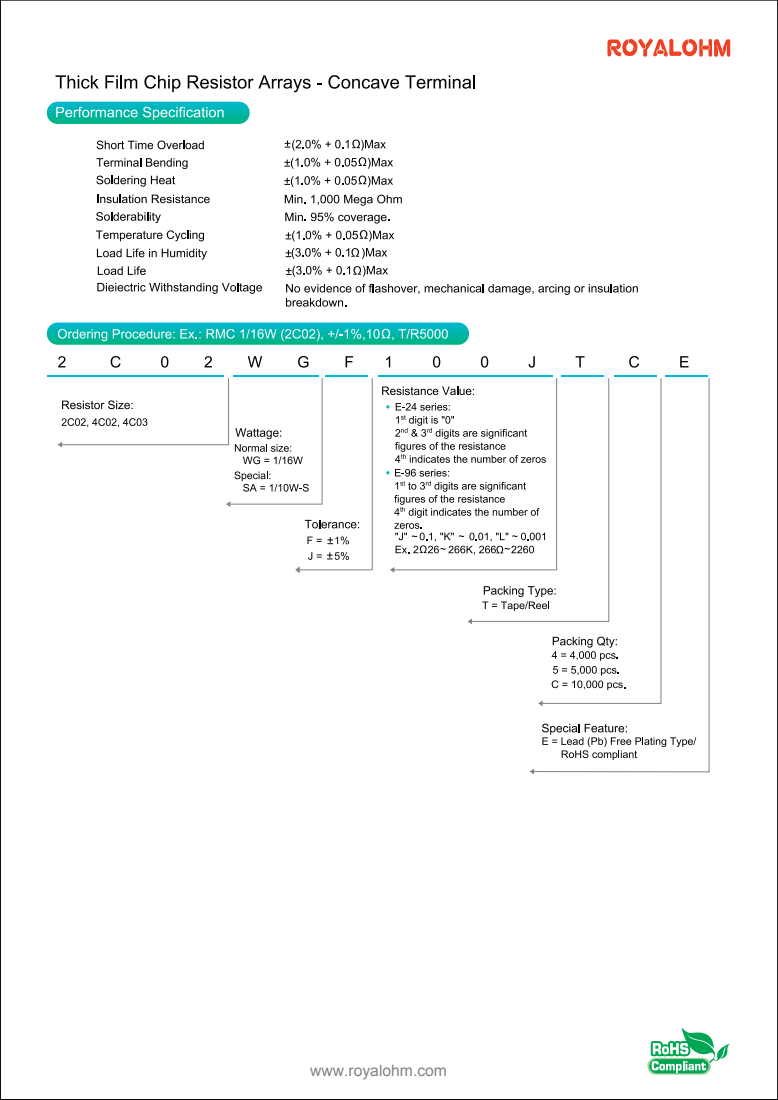
[picture p72: page 3]

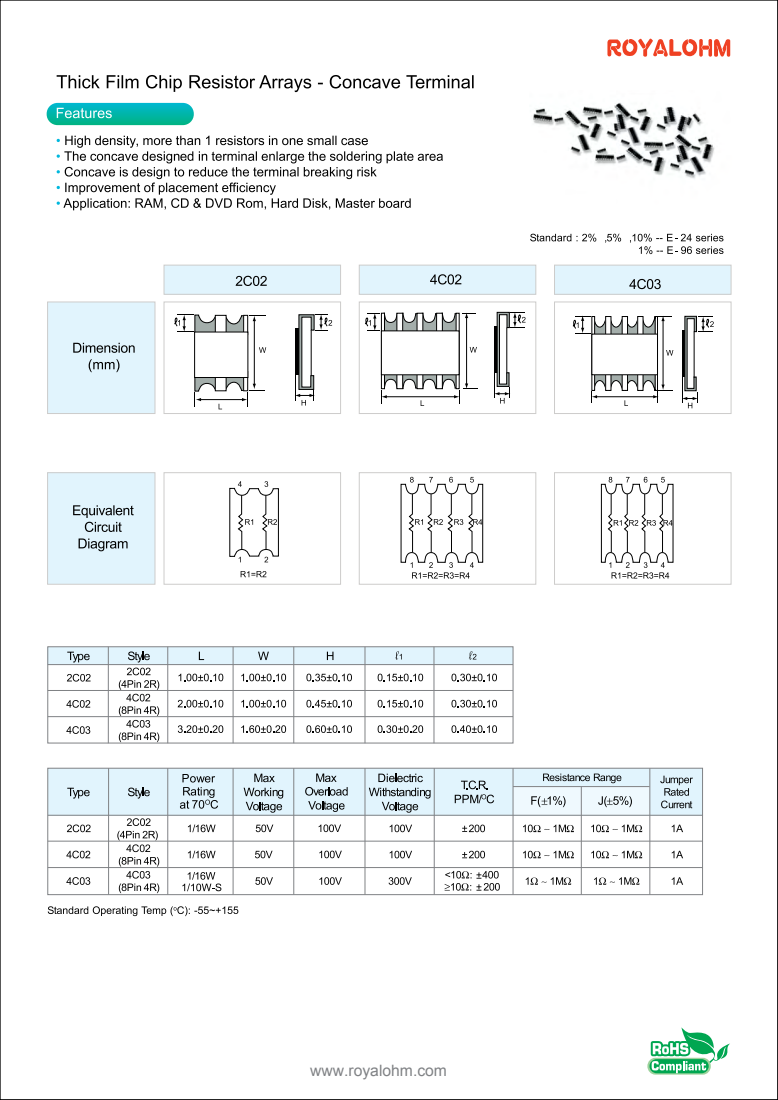
[picture p73: page 4]
