EIectron/RadioNoob/Hardware/audio_amplifier.kicad_sch

## KiCad design Hardware/audio_amplifier.kicad_sch (2024-04-10)

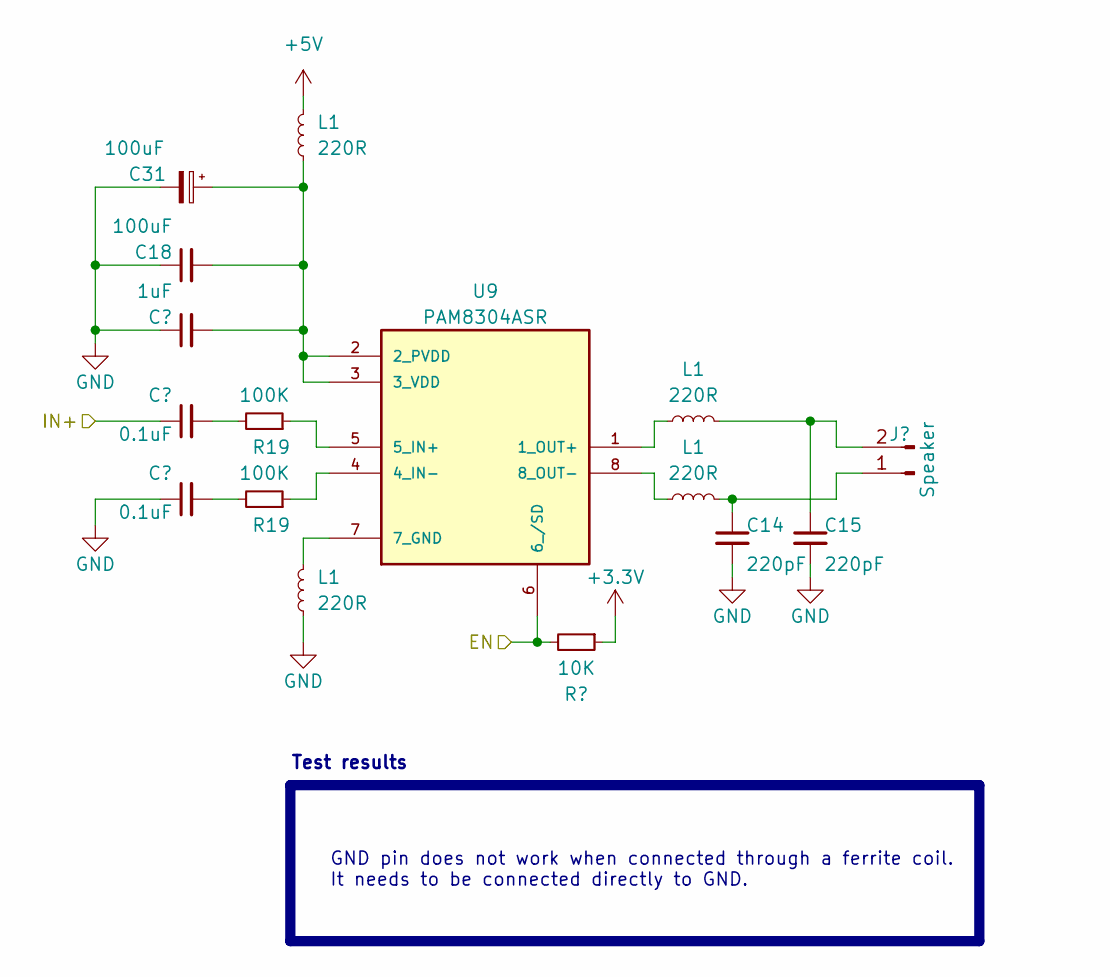
[picture p74: schematic audio_amplifier.kicad_sch]

Parts:
C11, C12: 0.1uF; C_0603_1608Metric
C13: 1uF; C_0603_1608Metric
C14, C15: 220pF; C_0603_1608Metric
C18: 100uF; C_0603_1608Metric
C31: 100uF; CP_Elec_6.3x5.4
J4: Speaker; JST_PH_B2B-PH-K_1x02_P2.00mm_Vertical
L1: 220R; L_0603_1608Metric
R19: 100K; R_0603_1608Metric
R51: 10K; R_0603_1608Metric
U9: PAM8304ASR; MSOP08

Connections:
+3.3V: R51.1
+5V: L1.2
EN: R51.2, U9.6 (6_/SD)
GND: C12.1, C13.1, C14.2, C15.2, C18.1, C31.2, L1.1
IN+: C11.1
unnamed: C11.2, R19.2
unnamed: C12.2, R19.2
unnamed: C13.2, C18.2, C31.1, L1.1, U9.2 (2_PVDD), U9.3 (3_VDD)
unnamed: C14.1, J4.1, L1.2
unnamed: C15.1, J4.2, L1.2
unnamed: L1.1, U9.1 (1_OUT+), U9.8 (8_OUT-)
unnamed: L1.2, U9.7 (7_GND)
unnamed: R19.1, U9.4 (4_IN-), U9.5 (5_IN+)

Notes on the sheet:
Test results
GND pin does not work when connected through a ferrite coil. It needs to be connected directly to GND.
