EIectron/RadioNoob/Hardware/elrs.kicad_sch

## KiCad design Hardware/elrs.kicad_sch (2024-04-10)

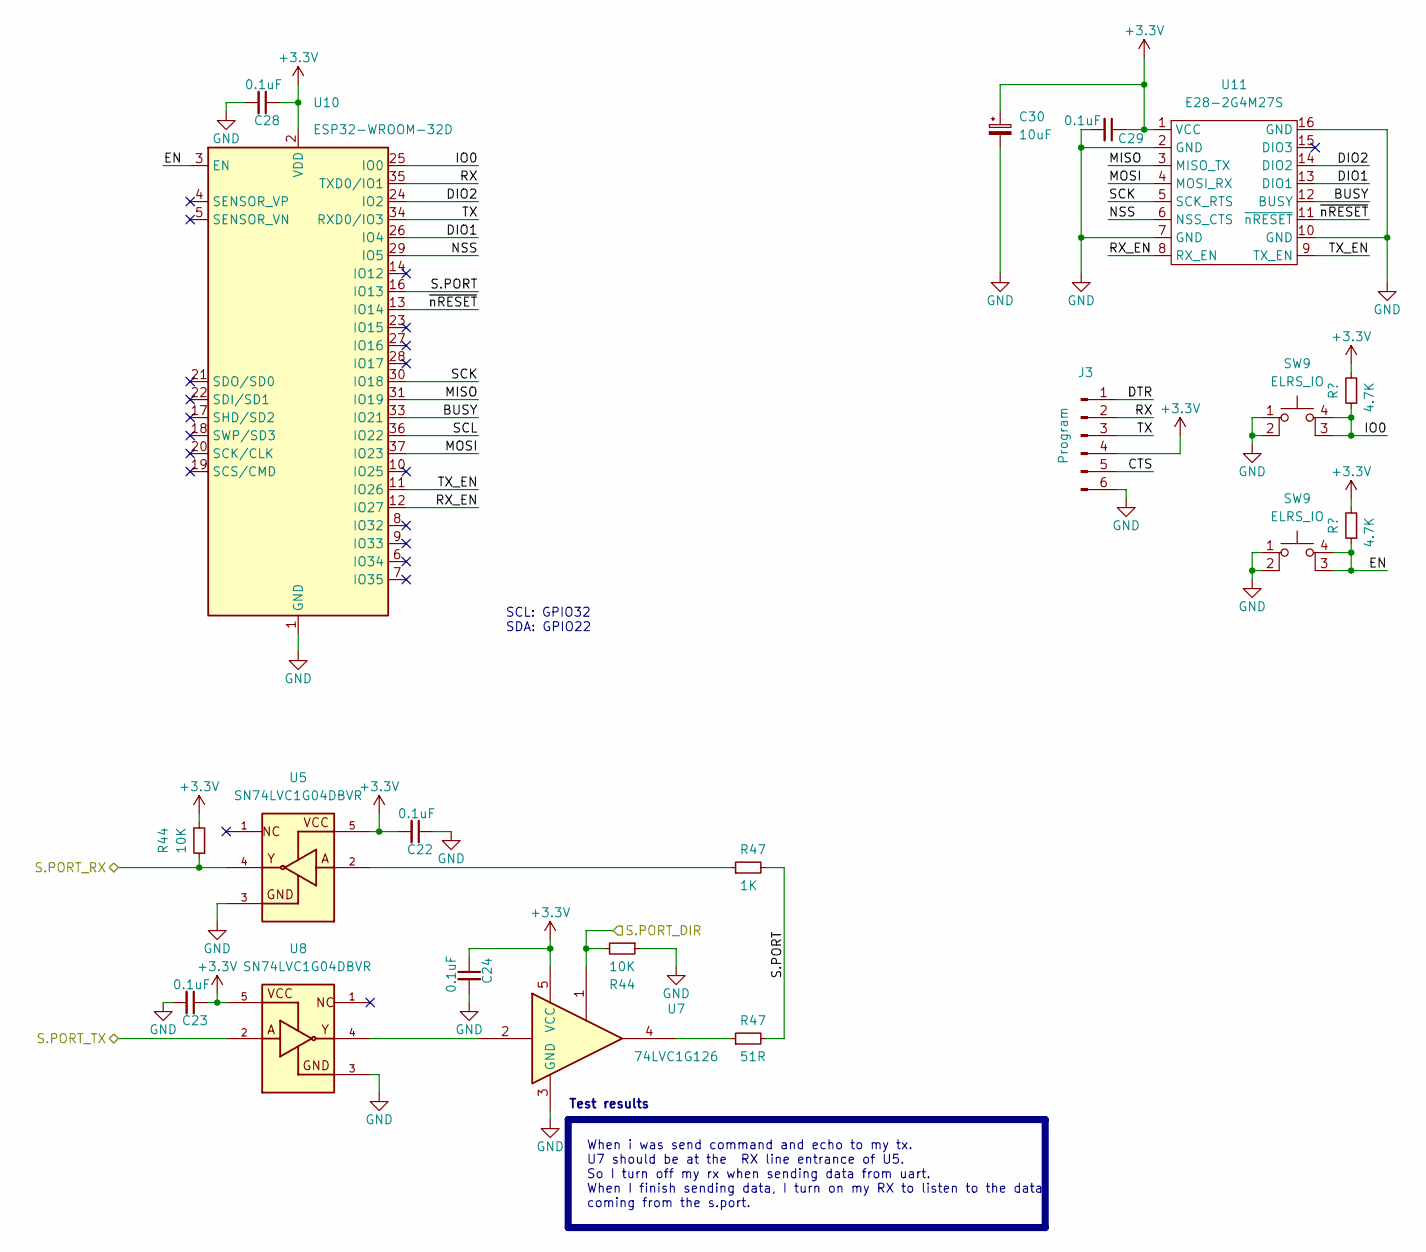
[picture p75: schematic elrs.kicad_sch]

Parts:
C22, C23, C24, C28, C29: 0.1uF; C_0603_1608Metric
C30: 10uF; CP_Elec_4x5.4
J3: Program; PinHeader_1x06_P2.54mm_Vertical
R9, R10: 4.7K; R_0603_1608Metric
R44: 10K; R_0603_1608Metric
R47: 1K; R_0603_1608Metric
SW9: ELRS_IO; 6x6_Tact_Switch
U5, U8: SN74LVC1G04DBVR; SOT95P280X145-5N
U7: 74LVC1G126; SOT-553
U10: ESP32-WROOM-32D; ESP32-WROOM-32
U11: E28-2G4M27S

Connections:
+3.3V: C22.2, C23.1, C24.1, C28.1, C29.1, C30.1, J3.4, R9.2, R10.2, R44.2, U5.5, U7.5 (VCC), U8.5, U10.2 (VDD), U11.1 (VCC)
BUSY: U10.33 (IO21), U11.12 (BUSY)
CTS: J3.5
DIO1: U10.26 (IO4), U11.13 (DIO1)
DIO2: U10.24 (IO2), U11.14 (DIO2)
DTR: J3.1
EN: R10.1, SW9.3 (K), SW9.4 (A), U10.3 (EN)
GND: C22.1, C23.2, C24.2, C28.2, C29.2, C30.2, J3.6, R44.1, SW9.1, SW9.2, U5.3, U7.3 (GND), U8.3, U10.1 (GND), U10.15 (GND), U10.38 (GND), U10.39 (GND), U11.2 (GND), U11.7 (GND), U11.10 (GND), U11.16 (GND)
IO0: R9.1, SW9.3 (K), SW9.4 (A), U10.25 (IO0)
MISO: U10.31 (IO19), U11.3 (MISO_TX)
MOSI: U10.37 (IO23), U11.4 (MOSI_RX)
NSS: U10.29 (IO5), U11.6 (NSS_CTS)
unnamed: R47.1, U5.2, U7.4
unnamed: U7.2, U8.4
RX: J3.2, U10.35 (TXD0/IO1)
RX_EN: U10.12 (IO27), U11.8 (RX_EN)
S.PORT: R47.2, U10.16 (IO13)
S.PORT_DIR: R44.2, U7.1
S.PORT_RX: R44.1, U5.4
S.PORT_TX: U8.2
SCK: U10.30 (IO18), U11.5 (SCK_RTS)
SCL: U10.36 (IO22)
TX: J3.3, U10.34 (RXD0/IO3)
TX_EN: U10.11 (IO26), U11.9 (TX_EN)
~nRESET: U10.13 (IO14), U11.11 (~nRESET)

Notes on the sheet:
SCL: GPIO32 SDA: GPIO22
Test results
When i was send command and echo to my tx. U7 should be at the RX line entrance of U5. So I turn off my rx when sending data from uart. When I finish sending data, I turn on my RX to listen to the data coming from the s.port.
