EIectron/RadioNoob/Hardware/io.kicad_sch

## KiCad design Hardware/io.kicad_sch (2024-04-10)

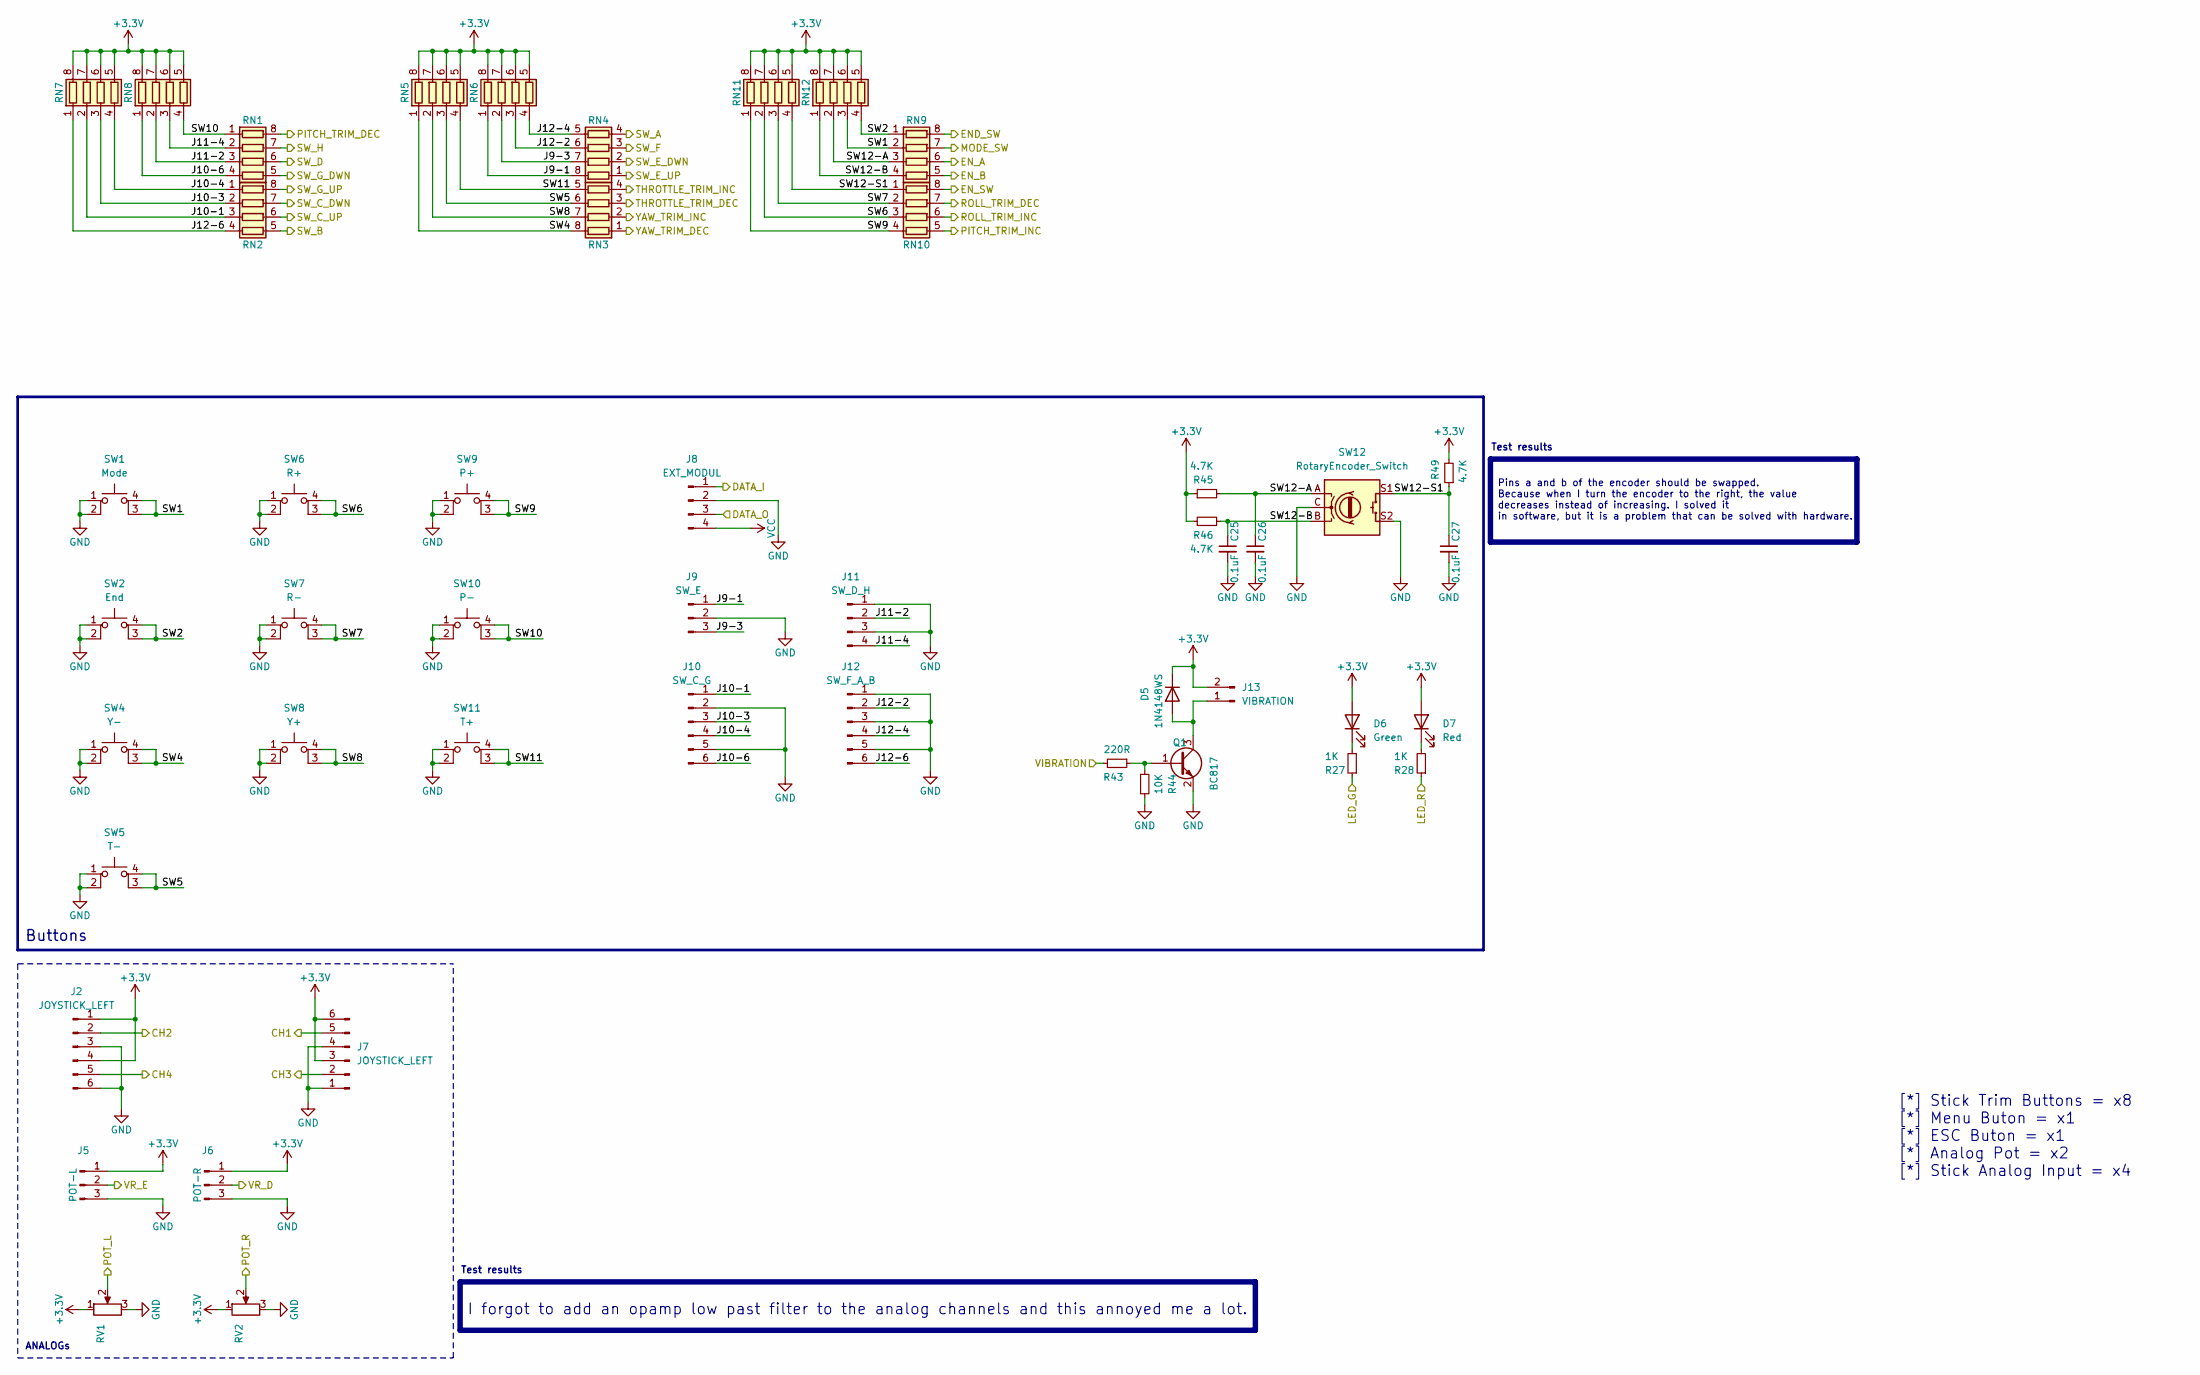
[picture p76: schematic io.kicad_sch]

Parts:
C25, C26, C27: 0.1uF; C_0603_1608Metric
D5: 1N4148WS; SOD-323
D6: Green; LED_D3.0mm
D7: Red; LED_D3.0mm
J2, J7: JOYSTICK_LEFT; JST_PH_B6B-PH-K_1x06_P2.00mm_Vertical
J5: POT-L; JST_PH_B3B-PH-K_1x03_P2.00mm_Vertical
J6: POT-R; JST_PH_B3B-PH-K_1x03_P2.00mm_Vertical
J8: EXT_MODUL; JST_PH_B4B-PH-K_1x04_P2.00mm_Vertical
J9: SW_E; JST_PH_B3B-PH-K_1x03_P2.00mm_Vertical
J10: SW_C_G; JST_PH_B6B-PH-K_1x06_P2.00mm_Vertical
J11: SW_D_H; JST_PH_B4B-PH-K_1x04_P2.00mm_Vertical
J12: SW_F_A_B; JST_PH_B6B-PH-K_1x06_P2.00mm_Vertical
J13: VIBRATION; JST_PH_B2B-PH-K_1x02_P2.00mm_Vertical
Q1: BC817; SOT-23
R27, R28: 1K; R_0603_1608Metric
R43: 220R; R_0603_1608Metric
R44: 10K; R_0603_1608Metric
R45, R46, R49: 4.7K; R_0603_1608Metric
RN1, RN2, RN3, RN4, RN9, RN10: 220R; R_Array_Concave_4x0603
RN5, RN6, RN7, RN8, RN11, RN12: 10K; R_Array_Concave_4x0603
RV1, RV2: R_Potentiometer; Potentiometer_Alpha_RD901F-40-00D_Single_Vertical
SW1: Mode; 6x6_Tact_Switch
SW2: End; 6x6_Tact_Switch
SW4: Y-; 6x6_Tact_Switch
SW5: T-; 6x6_Tact_Switch
SW6: R+; 6x6_Tact_Switch
SW7: R-; 6x6_Tact_Switch
SW8: Y+; 6x6_Tact_Switch
SW9: P+; 6x6_Tact_Switch
SW10: P-; 6x6_Tact_Switch
SW11: T+; 6x6_Tact_Switch
SW12: RotaryEncoder_Switch; RotaryEncoder_Alps_EC11E-Switch_Vertical_H20mm_CircularMoun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

Connections:
+3.3V: D5.1 (K), D6.2 (A), D7.2 (A), J2.1, J2.4, J5.1, J6.1, J7.3, J7.6, J13.2, R45.1, R46.1, R49.2, RN5.5 (R4.2), RN5.6 (R3.2), RN5.7 (R2.2), RN5.8 (R1.2), RN6.5 (R4.2), RN6.6 (R3.2), RN6.7 (R2.2), RN6.8 (R1.2), RN7.5 (R4.2), RN7.6 (R3.2), RN7.7 (R2.2), RN7.8 (R1.2), RN8.5 (R4.2), RN8.6 (R3.2), RN8.7 (R2.2), RN8.8 (R1.2), RN11.5 (R4.2), RN11.6 (R3.2), RN11.7 (R2.2), RN11.8 (R1.2), RN12.5 (R4.2), RN12.6 (R3.2), RN12.7 (R2.2), RN12.8 (R1.2), RV1.1, RV2.1
CH1: J7.5
CH2: J2.2
CH3: J7.2
CH4: J2.5
DATA_I: J8.1
DATA_O: J8.3
END_SW: RN9.8 (R1.2)
EN_A: RN9.6 (R3.2)
EN_B: RN9.5 (R4.2)
EN_SW: RN10.8 (R1.2)
GND: C25.2, C26.2, C27.2, J2.3, J2.6, J5.3, J6.3, J7.1, J7.4, J8.2, J9.2, J10.2, J10.5, J11.1, J11.3, J12.1, J12.3, J12.5, Q1.2 (E), R44.2, RV1.3, RV2.3, SW1.1, SW1.2, SW2.1, SW2.2, SW4.1, SW4.2, SW5.1, SW5.2, SW6.1, SW6.2, SW7.1, SW7.2, SW8.1, SW8.2, SW9.1, SW9.2, SW10.1, SW10.2, SW11.1, SW11.2, SW12.C, SW12.S2
J9-1: J9.1, RN4.8 (R1.2), RN6.1 (R1.1)
J9-3: J9.3, RN4.7 (R2.2), RN6.2 (R2.1)
J10-1: J10.1, RN2.3 (R3.1), RN7.2 (R2.1)
J10-3: J10.3, RN2.2 (R2.1), RN7.3 (R3.1)
J10-4: J10.4, RN2.1 (R1.1), RN7.4 (R4.1)
J10-6: J10.6, RN1.4 (R4.1), RN8.1 (R1.1)
J11-2: J11.2, RN1.3 (R3.1), RN8.2 (R2.1)
J11-4: J11.4, RN1.2 (R2.1), RN8.3 (R3.1)
J12-2: J12.2, RN4.6 (R3.2), RN6.3 (R3.1)
J12-4: J12.4, RN4.5 (R4.2), RN6.4 (R4.1)
J12-6: J12.6, RN2.4 (R4.1), RN7.1 (R1.1)
LED_G: R27.1
LED_R: R28.1
MODE_SW: RN9.7 (R2.2)
unnamed: D5.2 (A), J13.1, Q1.3 (C)
unnamed: D6.1 (K), R27.2
unnamed: D7.1 (K), R28.2
unnamed: Q1.1 (B), R43.1, R44.1
PITCH_TRIM_DEC: RN1.8 (R1.2)
PITCH_TRIM_INC: RN10.5 (R4.2)
POT_L: RV1.2
POT_R: RV2.2
ROLL_TRIM_DEC: RN10.7 (R2.2)
ROLL_TRIM_INC: RN10.6 (R3.2)
SW1: RN9.2 (R2.1), RN12.3 (R3.1), SW1.3 (K), SW1.4 (A)
SW2: RN9.1 (R1.1), RN12.4 (R4.1), SW2.3 (K), SW2.4 (A)
SW4: RN3.8 (R1.2), RN5.1 (R1.1), SW4.3 (K), SW4.4 (A)
SW5: RN3.6 (R3.2), RN5.3 (R3.1), SW5.3 (K), SW5.4 (A)
SW6: RN10.3 (R3.1), RN11.2 (R2.1), SW6.3 (K), SW6.4 (A)
SW7: RN10.2 (R2.1), RN11.3 (R3.1), SW7.3 (K), SW7.4 (A)
SW8: RN3.7 (R2.2), RN5.2 (R2.1), SW8.3 (K), SW8.4 (A)
SW9: RN10.4 (R4.1), RN11.1 (R1.1), SW9.3 (K), SW9.4 (A)
SW10: RN1.1 (R1.1), RN8.4 (R4.1), SW10.3 (K), SW10.4 (A)
SW11: RN3.5 (R4.2), RN5.4 (R4.1), SW11.3 (K), SW11.4 (A)
SW12-A: C26.1, R45.2, RN9.3 (R3.1), RN12.2 (R2.1), SW12.A
SW12-B: C25.1, R46.2, RN9.4 (R4.1), RN12.1 (R1.1), SW12.B
SW12-S1: C27.1, R49.1, RN10.1 (R1.1), RN11.4 (R4.1), SW12.S1
SW_A: RN4.4 (R4.1)
SW_B: RN2.5 (R4.2)
SW_C_DWN: RN2.7 (R2.2)
SW_C_UP: RN2.6 (R3.2)
SW_D: RN1.6 (R3.2)
SW_E_DWN: RN4.2 (R2.1)
SW_E_UP: RN4.1 (R1.1)
SW_F: RN4.3 (R3.1)
SW_G_DWN: RN1.5 (R4.2)
SW_G_UP: RN2.8 (R1.2)
SW_H: RN1.7 (R2.2)
THROTTLE_TRIM_DEC: RN3.3 (R3.1)
THROTTLE_TRIM_INC: RN3.4 (R4.1)
VCC: J8.4
VIBRATION: R43.2
VR_D: J6.2
VR_E: J5.2
YAW_TRIM_DEC: RN3.1 (R1.1)
YAW_TRIM_INC: RN3.2 (R2.1)

Notes on the sheet:
Buttons
ANALOGs
Test results
I forgot to add an opamp low past filter to the analog channels and this annoyed me a lot.
Pins a and b of the encoder should be swapped. Because when I turn the encoder to the right, the value decreases instead of increasing. I solved it in software, but it is a problem that can be solved with hardware.
[*] Stick Trim Buttons = x8 [*] Menu Buton = x1 [*] ESC Buton = x1 [*] Analog Pot = x2 [*] Stick Analog Input = x4
