EIectron/RadioNoob/Hardware/main_core.kicad_sch

## KiCad design Hardware/main_core.kicad_sch (2024-04-10)

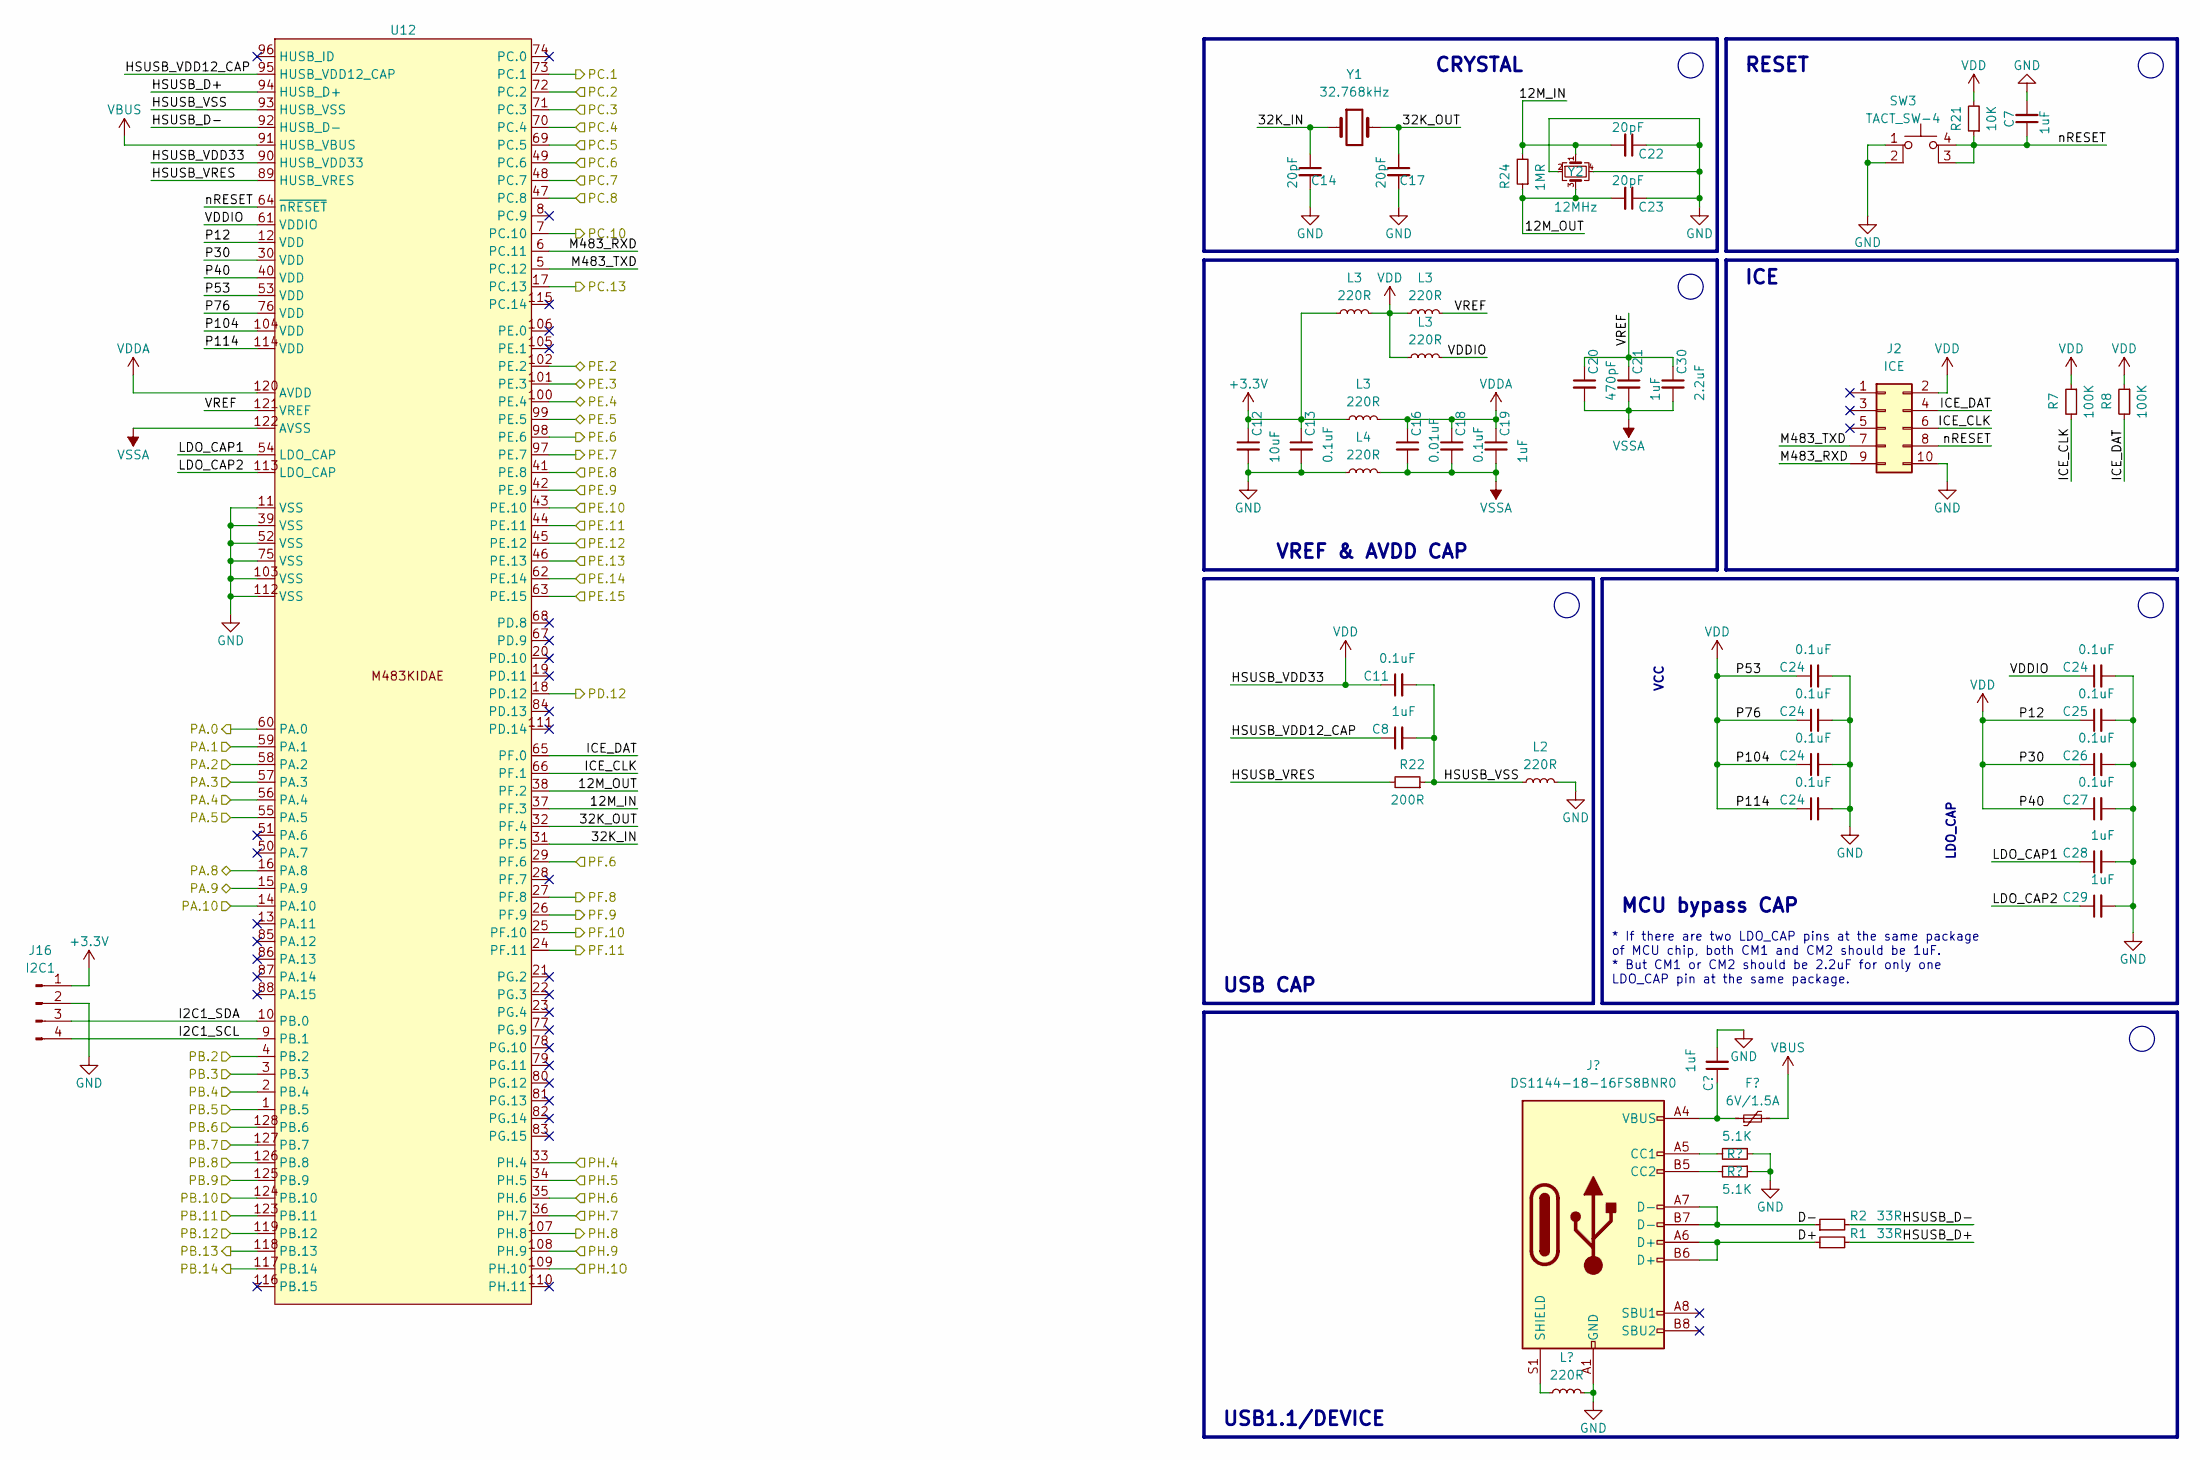
[picture p77: schematic main_core.kicad_sch]

Parts:
C1, C7, C8, C19, C21, C28, C29: 1uF; C_0603_1608Metric
C11, C13, C18, C24, C25, C26, C27: 0.1uF; C_0603_1608Metric
C12: 10uF; C_0603_1608Metric
C14, C17, C22, C23: 20pF; C_0603_1608Metric
C16: 0.01uF; C_0603_1608Metric
C20: 470pF; C_0603_1608Metric
C30: 2.2uF; C_0603_1608Metric
F1: 6V/1.5A; Fuse_0805_2012Metric
J1: DS1144-18-16FS8BNR0; USB_C_Receptacle_HRO_TYPE-C-31-M-12
J2: ICE; PinSocket_2x05_P1.27mm_Vertical
J16: I2C1; PinHeader_1x04_P2.54mm_Vertical
L1, L2, L3, L4: 220R; L_0603_1608Metric
R1, R2: 5.1K; R_0603_1608Metric
R7, R8: 100K; R_0603_1608Metric
R21: 10K; R_0603_1608Metric
R22: 200R; R_0603_1608Metric
R24: 1MR; R_0603_1608Metric
SW3: TACT_SW-4
U12: M483KIDAE; LQFP-128_14x14mm_P0.4mm
Y1: 32.768kHz; Crystal_SMD_EuroQuartz_EQ161-2Pin_3.2x1.5mm
Y2: 12MHz; Crystal_SMD_3225-4Pin_3.2x2.5mm

Connections:
12M_IN: C22.2, R24.2, U12.37 (PF.3), Y2.1
12M_OUT: C23.2, R24.1, U12.38 (PF.2), Y2.3
32K_IN: C14.1, U12.31 (PF.5), Y1.1
32K_OUT: C17.1, U12.32 (PF.4), Y1.2
+3.3V: C12.1, C13.1, J16.1, L3.1
D+: J1.A6 (D+), J1.B6 (D+), R1.1
D-: J1.A7 (D-), J1.B7 (D-), R2.1
GND: C1.2, C7.2, C12.2, C13.2, C14.2, C17.2, C22.1, C23.1, C24.2, C25.2, C26.2, C27.2, C28.2, C29.2, J1.A1 (GND), J1.A12 (GND), J1.B1 (GND), J1.B12 (GND), J2.10, J16.2, L1.2, L2.1, L4.1, R1.1, R2.1, SW3.1, SW3.2, U12.11 (VSS), U12.39 (VSS), U12.52 (VSS), U12.75 (VSS), U12.103 (VSS), U12.112 (VSS), Y2.2, Y2.4
HSUSB_D+: R1.2, U12.94 (HUSB_D+)
HSUSB_D-: R2.2, U12.92 (HUSB_D-)
HSUSB_VDD12_CAP: C8.1, U12.95 (HUSB_VDD12_CAP)
HSUSB_VRES: R22.2, U12.89 (HUSB_VRES)
HSUSB_VSS: C8.2, C11.2, L2.2, R22.1, U12.93 (HUSB_VSS)
I2C1_SCL: J16.4, U12.9 (PB.1)
I2C1_SDA: J16.3, U12.10 (PB.0)
ICE_CLK: J2.6, R7.2, U12.66 (PF.1)
ICE_DAT: J2.4, R8.2, U12.65 (PF.0)
LDO_CAP1: C28.1, U12.54 (LDO_CAP)
LDO_CAP2: C29.1, U12.113 (LDO_CAP)
M483_RXD: J2.9, U12.6 (PC.11)
M483_TXD: J2.7, U12.5 (PC.12)
unnamed: C1.1, F1.1, J1.A4 (VBUS), J1.A9 (VBUS), J1.B4 (VBUS), J1.B9 (VBUS)
unnamed: J1.A5 (CC1), R1.2
unnamed: J1.B5 (CC2), R2.2
unnamed: J1.S1 (SHIELD), L1.1
PA.0: U12.60 (PA.0)
PA.1: U12.59 (PA.1)
PA.2: U12.58 (PA.2)
PA.3: U12.57 (PA.3)
PA.4: U12.56 (PA.4)
PA.5: U12.55 (PA.5)
PA.8: U12.16 (PA.8)
PA.9: U12.15 (PA.9)
PA.10: U12.14 (PA.10)
PB.2: U12.4 (PB.2)
PB.3: U12.3 (PB.3)
PB.4: U12.2 (PB.4)
PB.5: U12.1 (PB.5)
PB.6: U12.128 (PB.6)
PB.7: U12.127 (PB.7)
PB.8: U12.126 (PB.8)
PB.9: U12.125 (PB.9)
PB.10: U12.124 (PB.10)
PB.11: U12.123 (PB.11)
PB.12: U12.119 (PB.12)
PB.13: U12.118 (PB.13)
PB.14: U12.117 (PB.14)
PC.1: U12.73 (PC.1)
PC.2: U12.72 (PC.2)
PC.3: U12.71 (PC.3)
PC.4: U12.70 (PC.4)
PC.5: U12.69 (PC.5)
PC.6: U12.49 (PC.6)
PC.7: U12.48 (PC.7)
PC.8: U12.47 (PC.8)
PC.10: U12.7 (PC.10)
PC.13: U12.17 (PC.13)
PD.12: U12.18 (PD.12)
PE.2: U12.102 (PE.2)
PE.3: U12.101 (PE.3)
PE.4: U12.100 (PE.4)
PE.5: U12.99 (PE.5)
PE.6: U12.98 (PE.6)
PE.7: U12.97 (PE.7)
PE.8: U12.41 (PE.8)
PE.9: U12.42 (PE.9)
PE.10: U12.43 (PE.10)
PE.11: U12.44 (PE.11)
PE.12: U12.45 (PE.12)
PE.13: U12.46 (PE.13)
PE.14: U12.62 (PE.14)
PE.15: U12.63 (PE.15)
PF.6: U12.29 (PF.6)
PF.8: U12.27 (PF.8)
PF.9: U12.26 (PF.9)
PF.10: U12.25 (PF.10)
PF.11: U12.24 (PF.11)
PH.1O: U12.109 (PH.10)
PH.4: U12.33 (PH.4)
PH.5: U12.34 (PH.5)
PH.6: U12.35 (PH.6)
PH.7: U12.36 (PH.7)
PH.8: U12.107 (PH.8)
PH.9: U12.108 (PH.9)
VBUS: F1.2, U12.91 (HUSB_VBUS)
VDD: C11.1, C24.1, C25.1, C26.1, C27.1, J2.2, L3.1, L3.2, R7.1, R8.1, R21.2, U12.12 (VDD), U12.30 (VDD), U12.40 (VDD), U12.53 (VDD), U12.76 (VDD), U12.90 (HUSB_VDD33), U12.104 (VDD), U12.114 (VDD)
VDDA: C16.1, C18.1, C19.1, L3.2, U12.120 (AVDD)
VDDIO: C24.1, L3.2, U12.61 (VDDIO)
VREF: C20.1, C21.1, C30.1, L3.2, U12.121 (VREF)
VSSA: C16.2, C18.2, C19.2, C20.2, C21.2, C30.2, L4.2, U12.122 (AVSS)
nRESET: C7.1, J2.8, R21.1, SW3.3, SW3.4, U12.64 (~nRESET)

Notes on the sheet:
RESET
MCU bypass CAP
ICE
LDO_CAP
* If there are two LDO_CAP pins at the same package of MCU chip, both CM1 and CM2 should be 1uF. * But CM1 or CM2 should be 2.2uF for only one LDO_CAP pin at the same package.
VCC
USB CAP
VREF & AVDD CAP
CRYSTAL
USB1.1/DEVICE
