EIectron/RadioNoob/Hardware/power.kicad_sch

## KiCad design Hardware/power.kicad_sch (2024-04-10)

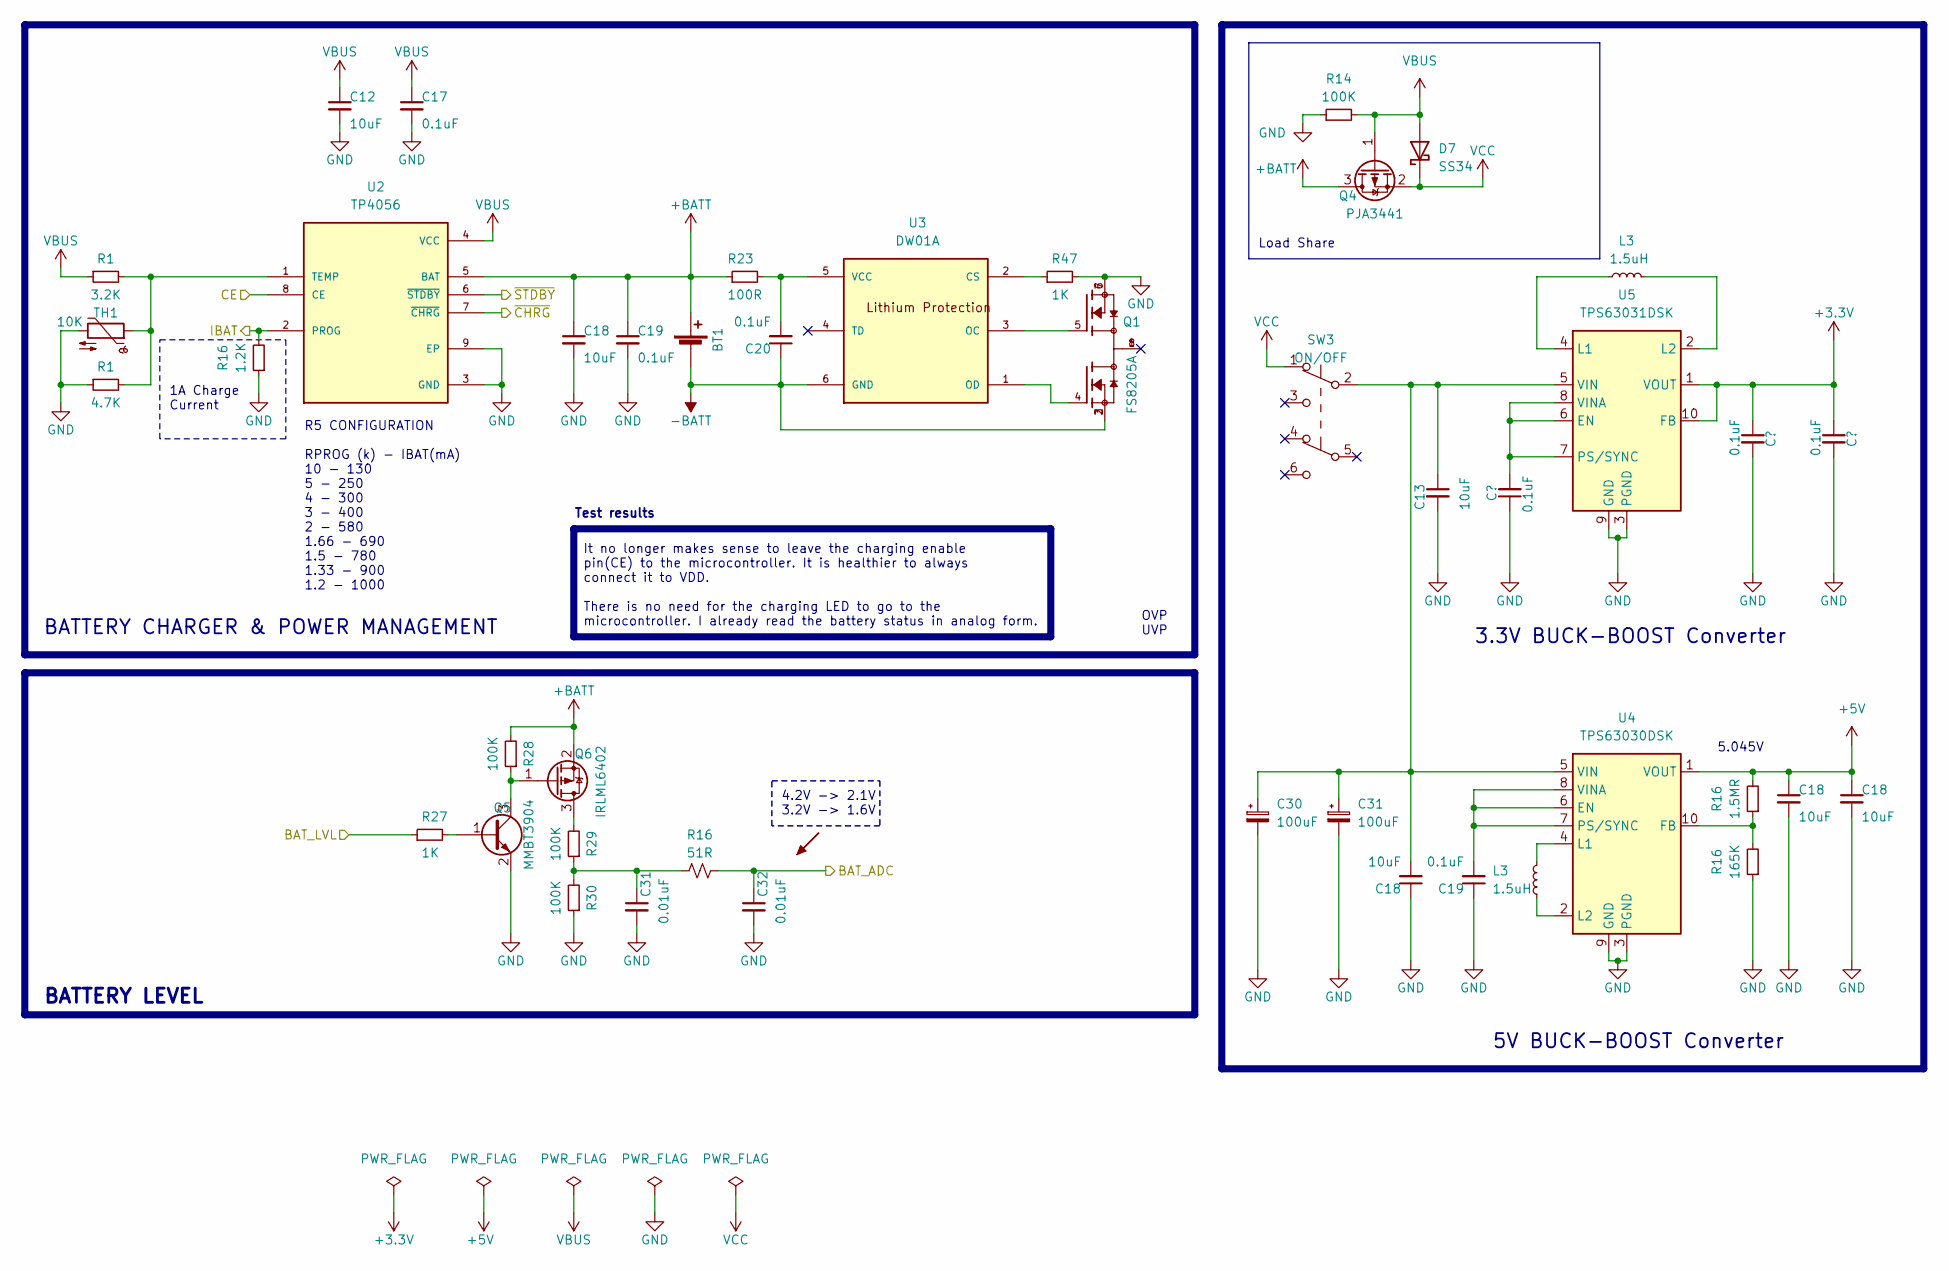
[picture p78: schematic power.kicad_sch]

Parts:
BT1: Battery_Cell; JST_XH_B2B-XH-A_1x02_P2.50mm_Vertical
C8, C17, C19, C20: 0.1uF; C_0603_1608Metric
C12, C13, C18: 10uF; C_0603_1608Metric
C30: 100uF; CP_Elec_6.3x5.4
C31, C32: 0.01uF; C_0603_1608Metric
D7: SS34; D_SMC
L3: 1.5uH; L_Coilcraft_XxL4020
Q1: FS8205A; SOP65P640X120-8N
Q4: PJA3441; SOT-23
Q5: MMBT3904; SOT-23
Q6: IRLML6402; SOT-23
R1: 4.7K; R_0603_1608Metric
R14, R28, R29, R30: 100K; R_0603_1608Metric
R16: 165K; R_0603_1608Metric
R23: 100R; R_0603_1608Metric
R27, R47: 1K; R_0603_1608Metric
SW3: ON/OFF; DPDT-Slide-Switch
TH1: 10K; PinSocket_1x02_P2.54mm_Vertical
U2: TP4056; SOP127P600X175-9N
U3: DW01A; SOT23-6
U4: TPS63030DSK; WSON-10-1EP_2.5x2.5mm_P0.5mm_EP1.2x2mm
U5: TPS63031DSK; WSON-10-1EP_2.5x2.5mm_P0.5mm_EP1.2x2mm

Connections:
+3.3V: C8.1, U5.1 (VOUT), U5.10 (FB)
+5V: C18.1, R16.2, U4.1 (VOUT)
+BATT: BT1.1 (+), C18.1, C19.1, Q4.3 (D), Q6.2 (S), R23.1, R28.2, U2.5 (BAT)
-BATT: BT1.2 (-), C20.1, Q1.2, Q1.3, U3.6 (GND)
BAT_ADC: C32.1, R16.1
BAT_LVL: R27.1
CE: U2.8 (CE)
GND: C8.1, C8.2, C12.2, C13.2, C17.2, C18.1, C18.2, C19.1, C19.2, C30.2, C31.2, C32.2, Q1.6, Q1.7, Q5.2 (E), R1.1, R14.1, R16.1, R30.1, R47.2, TH1.2, U2.3 (GND), U2.9 (EP), U4.3 (PGND), U4.9 (GND), U4.11 (PGND), U5.3 (PGND), U5.9 (GND), U5.11 (PGND)
IBAT: R16.2, U2.2 (PROG)
unnamed: C8.2, U5.6 (EN), U5.7 (PS/SYNC), U5.8 (VINA)
unnamed: C13.1, C18.2, C30.1, C31.1, SW3.2 (B), U4.5 (VIN), U5.5 (VIN)
unnamed: C19.2, U4.6 (EN), U4.7 (PS/SYNC), U4.8 (VINA)
unnamed: C20.2, R23.2, U3.5 (VCC)
unnamed: C31.1, R16.2, R29.1, R30.2
unnamed: L3.1, U4.2 (L2), U5.4 (L1)
unnamed: L3.2, U4.4 (L1), U5.2 (L2)
unnamed: Q1.1, Q1.8
unnamed: Q1.4, U3.1 (OD)
unnamed: Q1.5, U3.3 (OC)
unnamed: Q5.1 (B), R27.2
unnamed: Q5.3 (C), Q6.1 (G), R28.1
unnamed: Q6.3 (D), R29.2
unnamed: R1.2, TH1.1, U2.1 (TEMP)
unnamed: R16.1, R16.2, U4.10 (FB)
unnamed: R47.1, U3.2 (CS)
VBUS: C12.1, C17.1, D7.2 (A), Q4.1 (G), R1.1, R14.2, U2.4 (VCC)
VCC: D7.1 (K), Q4.2 (S), SW3.1 (A)
~CHRG: U2.7 (~CHRG)
~STDBY: U2.6 (~STDBY)

Notes on the sheet:
BATTERY LEVEL
4.2V -> 2.1V 3.2V -> 1.6V
1A Charge Current
OVP UVP
R5 CONFIGURATION RPROG (k) - IBAT(mA) 10 - 130 5 - 250 4 - 300 3 - 400 2 - 580 1.66 - 690 1.5 - 780 1.33 - 900 1.2 - 1000
BATTERY CHARGER & POWER MANAGEMENT
5.045V
Load Share
5V BUCK-BOOST Converter
Test results
It no longer makes sense to leave the charging enable pin(CE) to the microcontroller. It is healthier to always connect it to VDD. There is no need for the charging LED to go to the microcontroller. I already read the battery status in analog form.
3.3V BUCK-BOOST Converter
