EIectron/RadioNoob/Hardware/power_management.kicad_sch

## KiCad design Hardware/power_management.kicad_sch (2024-04-10)

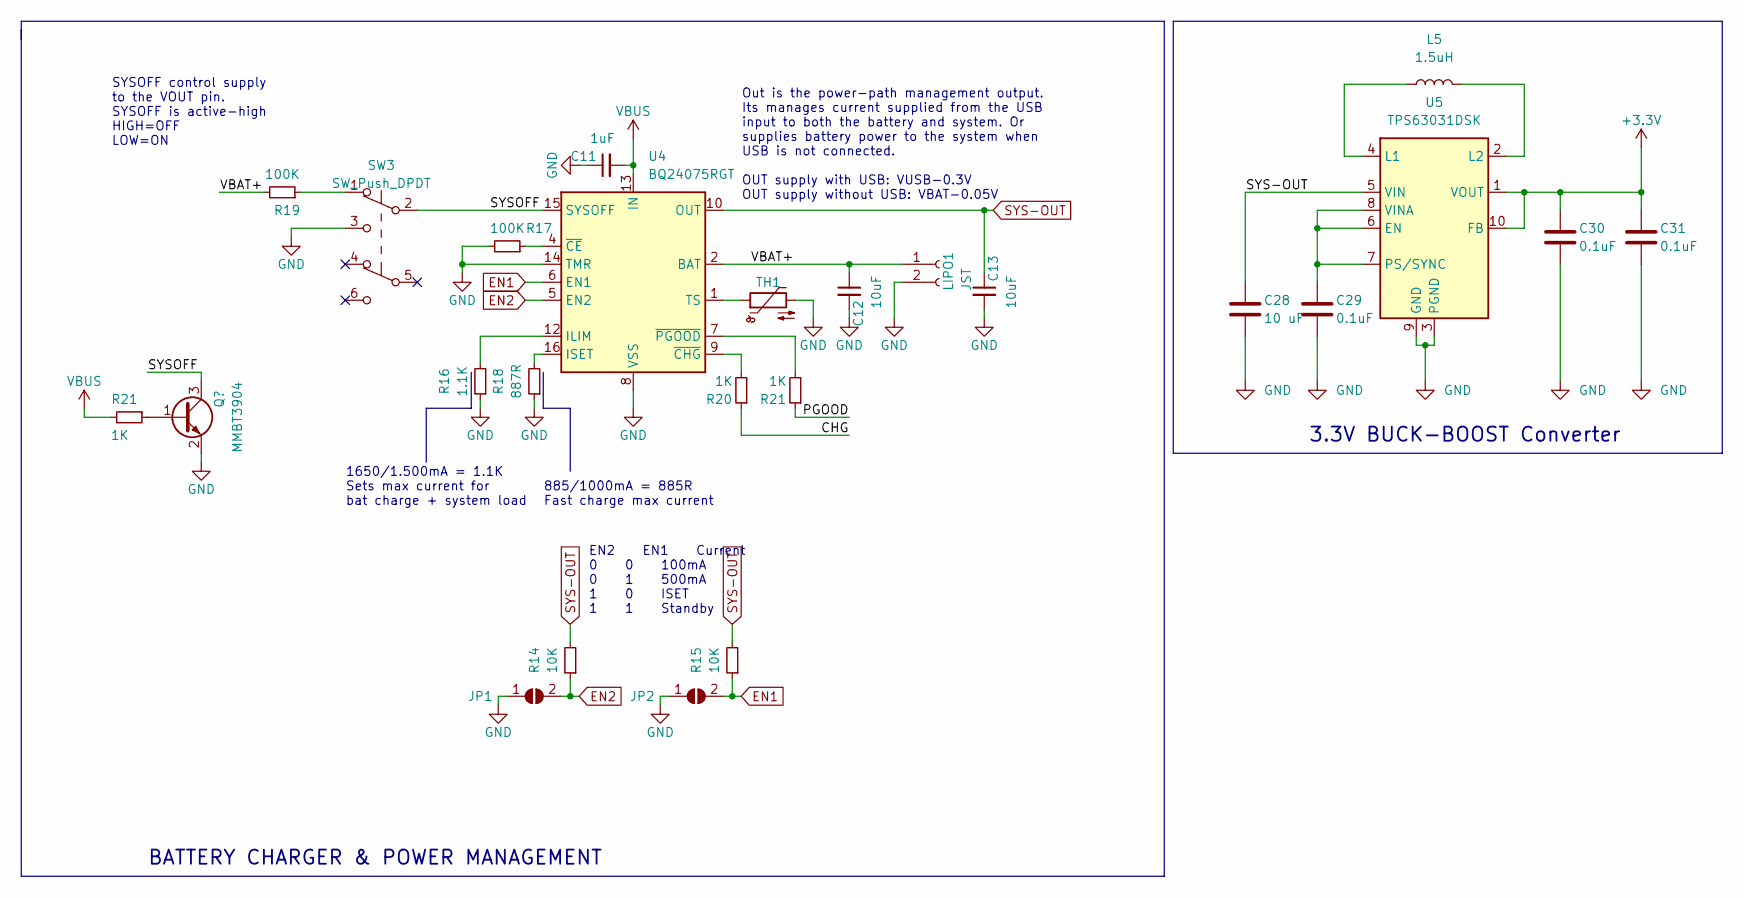
[picture p79: schematic power_management.kicad_sch]

Parts:
C11: 1uF; C_0603_1608Metric
C12, C13: 10uF; C_0603_1608Metric
C28: 10 uF; C_0402_1005Metric
C29, C30, C31: 0.1uF; C_0402_1005Metric
JP1, JP2: SolderJumper_2_Open; SolderJumper-2_P1.3mm_Open_RoundedPad1.0x1.5mm
L5: 1.5uH; L_Coilcraft_XxL4020
LIPO1: JST; PinHeader_1x02_P2.54mm_Vertical
Q1: MMBT3904; SOT-23
R14, R15: 10K; R_0603_1608Metric
R16: 1.1K; R_0603_1608Metric
R17, R19: 100K; R_0603_1608Metric
R18: 887R; R_0603_1608Metric
R20, R21: 1K; R_0603_1608Metric
SW3: SW_Push_DPDT
TH1: Thermistor_NTC; PinSocket_1x02_P2.54mm_Vertical
U4: BQ24075RGT; VQFN-16-1EP_3x3mm_P0.5mm_EP1.6x1.6mm
U5: TPS63031DSK; WSON-10-1EP_2.5x2.5mm_P0.5mm_EP1.2x2mm

Connections:
+3.3V: C30.1, C31.1, U5.1 (VOUT), U5.10 (FB)
CHG: R20.1
EN1: JP2.2 (B), R15.1, U4.6 (EN1)
EN2: JP1.2 (B), R14.1, U4.5 (EN2)
GND: C11.1, C12.2, C13.2, C28.2, C29.2, C30.2, C31.2, JP1.1 (A), JP2.1 (A), LIPO1.2, Q1.2 (E), R16.1, R17.2, R18.1, SW3.3 (C), TH1.2, U4.8 (VSS), U4.14 (TMR), U4.17 (VSS), U5.3 (PGND), U5.9 (GND), U5.11 (PGND)
unnamed: C29.1, U5.6 (EN), U5.7 (PS/SYNC), U5.8 (VINA)
unnamed: L5.1, U5.4 (L1)
unnamed: L5.2, U5.2 (L2)
unnamed: Q1.1 (B), R21.1
unnamed: R16.2, U4.12 (ILIM)
unnamed: R17.1, U4.4 (~CE)
unnamed: R18.2, U4.16 (ISET)
unnamed: R19.1, SW3.1 (A)
unnamed: R20.2, U4.9 (~CHG)
unnamed: R21.2, U4.7 (~PGOOD)
unnamed: TH1.1, U4.1 (TS)
PGOOD: R21.1
SYS-OUT: C13.1, C28.1, R14.2, R15.2, U4.10 (OUT), U4.11 (OUT), U5.5 (VIN)
SYSOFF: Q1.3 (C), SW3.2 (B), U4.15 (SYSOFF)
VBAT+: C12.1, LIPO1.1, R19.2, U4.2 (BAT), U4.3 (BAT)
VBUS: C11.2, R21.2, U4.13 (IN)

Notes on the sheet:
SYSOFF control supply to the VOUT pin. SYSOFF is active-high HIGH=OFF LOW=ON
885/1000mA = 885R Fast charge max current
1650/1.500mA = 1.1K Sets max current for bat charge + system load
EN2 EN1 Current 0 0 100mA 0 1 500mA 1 0 ISET 1 1 Standby
BATTERY CHARGER & POWER MANAGEMENT
Out is the power-path management output. Its manages current supplied from the USB input to both the battery and system. Or supplies battery power to the system when USB is not connected. OUT supply with USB: VUSB-0.3V OUT supply without USB: VBAT-0.05V
3.3V BUCK-BOOST Converter
