EIectron/RadioNoob/Hardware/sd_ card.kicad_sch

## KiCad design Hardware/sd_ card.kicad_sch (2024-04-10)

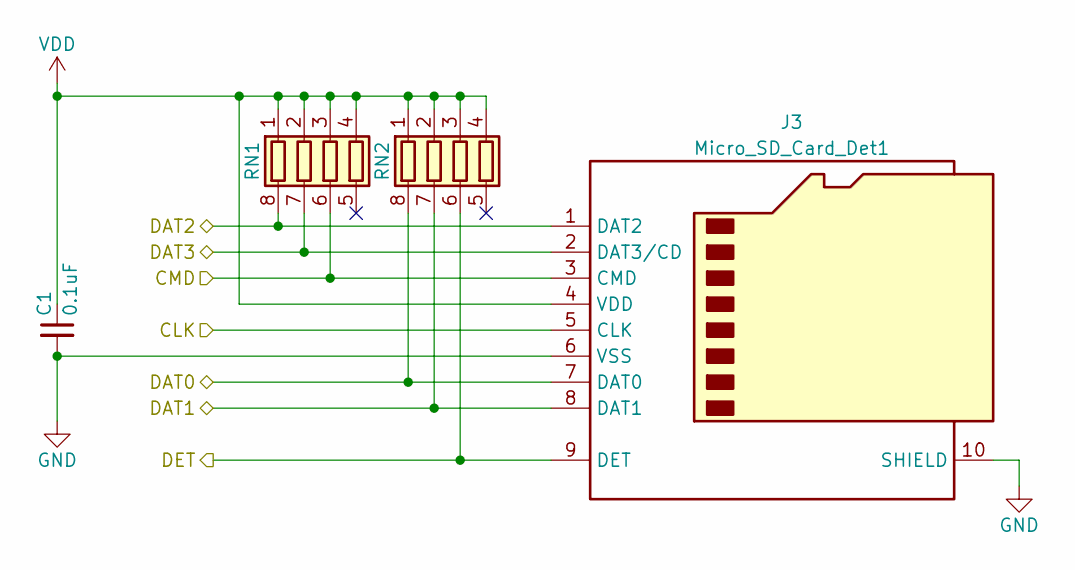
[picture p80: schematic sd_ card.kicad_sch]

Parts:
C1: 0.1uF; C_0603_1608Metric
J3: Micro_SD_Card_Det1; KLS1-TF-003D
RN1, RN2: 10K; R_Array_Concave_4x0603

Connections:
CLK: J3.5 (CLK)
CMD: J3.3 (CMD), RN1.6 (R3.2)
DAT0: J3.7 (DAT0), RN2.8 (R1.2)
DAT1: J3.8 (DAT1), RN2.7 (R2.2)
DAT2: J3.1 (DAT2), RN1.8 (R1.2)
DAT3: J3.2 (DAT3/CD), RN1.7 (R2.2)
DET: J3.9 (DET), RN2.6 (R3.2)
GND: C1.2, J3.6 (VSS), J3.10 (SHIELD)
VDD: C1.1, J3.4 (VDD), RN1.1 (R1.1), RN1.2 (R2.1), RN1.3 (R3.1), RN1.4 (R4.1), RN2.1 (R1.1), RN2.2 (R2.1), RN2.3 (R3.1), RN2.4 (R4.1)
