EIectron/RadioNoob/Software/M480_BSP/StdDriver/inc/sys.h

/**************************************************************************//**
 * @file     SYS.h
 * @version  V3.0
 * @brief    M480 Series SYS Driver Header File
 *
 * SPDX-License-Identifier: Apache-2.0
 * @copyright (C) 2016-2020 Nuvoton Technology Corp. All rights reserved.
 ******************************************************************************/

#ifndef __SYS_H__
#define __SYS_H__

#ifdef __cplusplus
extern "C"
{
#endif


/** @addtogroup Standard_Driver Standard Driver
  @{
*/

/** @addtogroup SYS_Driver SYS Driver
  @{
*/

/** @addtogroup SYS_EXPORTED_CONSTANTS SYS Exported Constants
  @{
*/


/*---------------------------------------------------------------------------------------------------------*/
/*  Module Reset Control Resister constant definitions.                                                    */
/*---------------------------------------------------------------------------------------------------------*/
#define PDMA_RST            ((0UL<<24) | SYS_IPRST0_PDMARST_Pos)        /*!< Reset PDMA \hideinitializer*/
#define EBI_RST             ((0UL<<24) | SYS_IPRST0_EBIRST_Pos)         /*!< Reset EBI \hideinitializer*/
#define EMAC_RST            ((0UL<<24) | SYS_IPRST0_EMACRST_Pos)        /*!< Reset EMAC \hideinitializer */
#define SDH0_RST            ((0UL<<24) | SYS_IPRST0_SDH0RST_Pos)        /*!< Reset SDH0 \hideinitializer */
#define CRC_RST             ((0UL<<24) | SYS_IPRST0_CRCRST_Pos)         /*!< Reset CRC \hideinitializer */
#define CCAP_RST            ((0UL<<24) | SYS_IPRST0_CCAPRST_Pos)        /*!< Reset ICAP \hideinitializer */
#define HSUSBD_RST          ((0UL<<24) | SYS_IPRST0_HSUSBDRST_Pos)      /*!< Reset HSUSBD \hideinitializer */
#define CRPT_RST            ((0UL<<24) | SYS_IPRST0_CRPTRST_Pos)        /*!< Reset CRPT \hideinitializer */
#define SPIM_RST            ((0UL<<24) | SYS_IPRST0_SPIMRST_Pos)        /*!< Reset SPIM \hideinitializer */
#define USBH_RST            ((0UL<<24) | SYS_IPRST0_USBHRST_Pos)        /*!< Reset USBH \hideinitializer */
#define SDH1_RST            ((0UL<<24) | SYS_IPRST0_SDH1RST_Pos)        /*!< Reset SDH1 \hideinitializer */

#define GPIO_RST            ((4UL<<24) | SYS_IPRST1_GPIORST_Pos)        /*!< Reset GPIO \hideinitializer */
#define TMR0_RST            ((4UL<<24) | SYS_IPRST1_TMR0RST_Pos)        /*!< Reset TMR0 \hideinitializer */
#define TMR1_RST            ((4UL<<24) | SYS_IPRST1_TMR1RST_Pos)        /*!< Reset TMR1 \hideinitializer */
#define TMR2_RST            ((4UL<<24) | SYS_IPRST1_TMR2RST_Pos)        /*!< Reset TMR2 \hideinitializer */
#define TMR3_RST            ((4UL<<24) | SYS_IPRST1_TMR3RST_Pos)        /*!< Reset TMR3 \hideinitializer */
#define ACMP01_RST          ((4UL<<24) | SYS_IPRST1_ACMP01RST_Pos)      /*!< Reset ACMP01 \hideinitializer */
#define I2C0_RST            ((4UL<<24) | SYS_IPRST1_I2C0RST_Pos)        /*!< Reset I2C0 \hideinitializer */
#define I2C1_RST            ((4UL<<24) | SYS_IPRST1_I2C1RST_Pos)        /*!< Reset I2C1 \hideinitializer */
#define I2C2_RST            ((4UL<<24) | SYS_IPRST1_I2C2RST_Pos)        /*!< Reset I2C2 \hideinitializer */
#define QSPI0_RST           ((4UL<<24) | SYS_IPRST1_QSPI0RST_Pos)       /*!< Reset QSPI0 \hideinitializer */
#define SPI0_RST            ((4UL<<24) | SYS_IPRST1_SPI0RST_Pos)        /*!< Reset SPI0 \hideinitializer */
#define SPI1_RST            ((4UL<<24) | SYS_IPRST1_SPI1RST_Pos)        /*!< Reset SPI1 \hideinitializer */
#define SPI2_RST            ((4UL<<24) | SYS_IPRST1_SPI2RST_Pos)        /*!< Reset SPI2 \hideinitializer */
#define UART0_RST           ((4UL<<24) | SYS_IPRST1_UART0RST_Pos)       /*!< Reset UART0 \hideinitializer */
#define UART1_RST           ((4UL<<24) | SYS_IPRST1_UART1RST_Pos)       /*!< Reset UART1 \hideinitializer */
#define UART2_RST           ((4UL<<24) | SYS_IPRST1_UART2RST_Pos)       /*!< Reset UART2 \hideinitializer */
#define UART3_RST           ((4UL<<24) | SYS_IPRST1_UART3RST_Pos)       /*!< Reset UART3 \hideinitializer */
#define UART4_RST           ((4UL<<24) | SYS_IPRST1_UART4RST_Pos)       /*!< Reset UART4 \hideinitializer */
#define UART5_RST           ((4UL<<24) | SYS_IPRST1_UART5RST_Pos)       /*!< Reset UART5 \hideinitializer */
#define UART6_RST           ((4UL<<24) | SYS_IPRST1_UART6RST_Pos)       /*!< Reset UART6 \hideinitializer */
#define UART7_RST           ((4UL<<24) | SYS_IPRST1_UART7RST_Pos)       /*!< Reset UART7 \hideinitializer */
#define CAN0_RST            ((4UL<<24) | SYS_IPRST1_CAN0RST_Pos)        /*!< Reset CAN0 \hideinitializer */
#define CAN1_RST            ((4UL<<24) | SYS_IPRST1_CAN1RST_Pos)        /*!< Reset CAN1 \hideinitializer */
#define OTG_RST             ((4UL<<24) | SYS_IPRST1_OTGRST_Pos)         /*!< Reset OTG \hideinitializer */
#define USBD_RST            ((4UL<<24) | SYS_IPRST1_USBDRST_Pos)        /*!< Reset USBD \hideinitializer */
#define EADC_RST            ((4UL<<24) | SYS_IPRST1_EADCRST_Pos)        /*!< Reset EADC \hideinitializer */
#define I2S0_RST            ((4UL<<24) | SYS_IPRST1_I2S0RST_Pos)        /*!< Reset I2S0 \hideinitializer */
#define HSOTG_RST           ((4UL<<24) | SYS_IPRST1_HSOTGRST_Pos)       /*!< Reset HSOTG \hideinitializer */
#define TRNG_RST            ((4UL<<24) | SYS_IPRST1_TRNGRST_Pos)        /*!< Reset TRNG \hideinitializer */

#define SC0_RST             ((8UL<<24) | SYS_IPRST2_SC0RST_Pos)         /*!< Reset SC0 \hideinitializer */
#define SC1_RST             ((8UL<<24) | SYS_IPRST2_SC1RST_Pos)         /*!< Reset SC1 \hideinitializer */
#define SC2_RST             ((8UL<<24) | SYS_IPRST2_SC2RST_Pos)         /*!< Reset SC2 \hideinitializer */
#define QSPI1_RST           ((8UL<<24) | SYS_IPRST2_QSPI1RST_Pos)       /*!< Reset QSPI1 \hideinitializer */
#define SPI3_RST            ((8UL<<24) | SYS_IPRST2_SPI3RST_Pos)        /*!< Reset SPI3 \hideinitializer */
#define USCI0_RST           ((8UL<<24) | SYS_IPRST2_USCI0RST_Pos)       /*!< Reset USCI0 \hideinitializer */
#define USCI1_RST           ((8UL<<24) | SYS_IPRST2_USCI1RST_Pos)       /*!< Reset USCI1 \hideinitializer */
#define DAC_RST             ((8UL<<24) | SYS_IPRST2_DACRST_Pos)         /*!< Reset DAC \hideinitializer */
#define EPWM0_RST           ((8UL<<24) | SYS_IPRST2_EPWM0RST_Pos)       /*!< Reset EPWM0 \hideinitializer */
#define EPWM1_RST           ((8UL<<24) | SYS_IPRST2_EPWM1RST_Pos)       /*!< Reset EPWM1 \hideinitializer */
#define BPWM0_RST           ((8UL<<24) | SYS_IPRST2_BPWM0RST_Pos)       /*!< Reset BPWM0 \hideinitializer */
#define BPWM1_RST           ((8UL<<24) | SYS_IPRST2_BPWM1RST_Pos)       /*!< Reset BPWM1 \hideinitializer */
#define QEI0_RST            ((8UL<<24) | SYS_IPRST2_QEI0RST_Pos)        /*!< Reset QEI0 \hideinitializer */
#define QEI1_RST            ((8UL<<24) | SYS_IPRST2_QEI1RST_Pos)        /*!< Reset QEI1 \hideinitializer */
#define ECAP0_RST           ((8UL<<24) | SYS_IPRST2_ECAP0RST_Pos)       /*!< Reset ECAP0 \hideinitializer */
#define ECAP1_RST           ((8UL<<24) | SYS_IPRST2_ECAP1RST_Pos)       /*!< Reset ECAP1 \hideinitializer */
#define CAN2_RST            ((8UL<<24) | SYS_IPRST2_CAN2RST_Pos)        /*!< Reset CAN2 \hideinitializer */
#define OPA_RST             ((8UL<<24) | SYS_IPRST2_OPARST_Pos)         /*!< Reset OPA \hideinitializer */
#define EADC1_RST           ((8UL<<24) | SYS_IPRST2_EADC1RST_Pos)       /*!< Reset EADC1 \hideinitializer */

/*---------------------------------------------------------------------------------------------------------*/
/*  Brown Out Detector Threshold Voltage Selection constant definitions.                                   */
/*---------------------------------------------------------------------------------------------------------*/
#define SYS_BODCTL_BOD_RST_EN           (1UL << SYS_BODCTL_BODRSTEN_Pos)    /*!< Brown-out Reset Enable \hideinitializer */
#define SYS_BODCTL_BOD_INTERRUPT_EN     (0UL << SYS_BODCTL_BODRSTEN_Pos)    /*!< Brown-out Interrupt Enable \hideinitializer */
#define SYS_BODCTL_BODVL_3_0V           (7UL << SYS_BODCTL_BODVL_Pos)       /*!< Setting Brown Out Detector Threshold Voltage as 3.0V \hideinitializer */
#define SYS_BODCTL_BODVL_2_8V           (6UL << SYS_BODCTL_BODVL_Pos)       /*!< Setting Brown Out Detector Threshold Voltage as 2.8V \hideinitializer */
#define SYS_BODCTL_BODVL_2_6V           (5UL << SYS_BODCTL_BODVL_Pos)       /*!< Setting Brown Out Detector Threshold Voltage as 2.6V \hideinitializer */
#define SYS_BODCTL_BODVL_2_4V           (4UL << SYS_BODCTL_BODVL_Pos)       /*!< Setting Brown Out Detector Threshold Voltage as 2.4V \hideinitializer */
#define SYS_BODCTL_BODVL_2_2V           (3UL << SYS_BODCTL_BODVL_Pos)       /*!< Setting Brown Out Detector Threshold Voltage as 2.2V \hideinitializer */
#define SYS_BODCTL_BODVL_2_0V           (2UL << SYS_BODCTL_BODVL_Pos)       /*!< Setting Brown Out Detector Threshold Voltage as 2.0V \hideinitializer */
#define SYS_BODCTL_BODVL_1_8V           (1UL << SYS_BODCTL_BODVL_Pos)       /*!< Setting Brown Out Detector Threshold Voltage as 1.8V \hideinitializer */
#define SYS_BODCTL_BODVL_1_6V           (0UL << SYS_BODCTL_BODVL_Pos)       /*!< Setting Brown Out Detector Threshold Voltage as 1.6V \hideinitializer */


/*---------------------------------------------------------------------------------------------------------*/
/*  VREFCTL constant definitions. (Write-Protection Register)                                              */
/*---------------------------------------------------------------------------------------------------------*/
#define SYS_VREFCTL_VREF_PIN        (0x0UL << SYS_VREFCTL_VREFCTL_Pos)    /*!< Vref = Vref pin \hideinitializer */
#define SYS_VREFCTL_VREF_1_6V       (0x3UL << SYS_VREFCTL_VREFCTL_Pos)    /*!< Vref = 1.6V \hideinitializer */
#define SYS_VREFCTL_VREF_2_0V       (0x7UL << SYS_VREFCTL_VREFCTL_Pos)    /*!< Vref = 2.0V \hideinitializer */
#define SYS_VREFCTL_VREF_2_5V       (0xBUL << SYS_VREFCTL_VREFCTL_Pos)    /*!< Vref = 2.5V \hideinitializer */
#define SYS_VREFCTL_VREF_3_0V       (0xFUL << SYS_VREFCTL_VREFCTL_Pos)    /*!< Vref = 3.0V \hideinitializer */
#define SYS_VREFCTL_VREF_AVDD       (0x10UL << SYS_VREFCTL_VREFCTL_Pos)   /*!< Vref = AVDD \hideinitializer */


/*---------------------------------------------------------------------------------------------------------*/
/*  USBPHY constant definitions. (Write-Protection Register)                                               */
/*---------------------------------------------------------------------------------------------------------*/
#define SYS_USBPHY_USBROLE_STD_USBD     (0x0UL << SYS_USBPHY_USBROLE_Pos)   /*!<  Standard USB device \hideinitializer */
#define SYS_USBPHY_USBROLE_STD_USBH     (0x1UL << SYS_USBPHY_USBROLE_Pos)   /*!<  Standard USB host \hideinitializer */
#define SYS_USBPHY_USBROLE_ID_DEPH      (0x2UL << SYS_USBPHY_USBROLE_Pos)   /*!<  ID dependent device \hideinitializer */
#define SYS_USBPHY_USBROLE_ON_THE_GO    (0x3UL << SYS_USBPHY_USBROLE_Pos)   /*!<  On-The-Go device \hideinitializer */
#define SYS_USBPHY_HSUSBROLE_STD_USBD   (0x0UL << SYS_USBPHY_HSUSBROLE_Pos)   /*!<  Standard HSUSB device \hideinitializer */
#define SYS_USBPHY_HSUSBROLE_STD_USBH   (0x1UL << SYS_USBPHY_HSUSBROLE_Pos)   /*!<  Standard HSUSB host \hideinitializer */
#define SYS_USBPHY_HSUSBROLE_ID_DEPH    (0x2UL << SYS_USBPHY_HSUSBROLE_Pos)   /*!<  ID dependent device \hideinitializer */

/*---------------------------------------------------------------------------------------------------------*/
/*  PLCTL constant definitions. (Write-Protection Register)                                                */
/*---------------------------------------------------------------------------------------------------------*/
#define SYS_PLCTL_PLSEL_PL0     (0x0UL<<SYS_PLCTL_PLSEL_Pos)   /*!< Set power level to power level 0 */
#define SYS_PLCTL_PLSEL_PL1     (0x1UL<<SYS_PLCTL_PLSEL_Pos)   /*!< Set power level to power level 1 */


/*---------------------------------------------------------------------------------------------------------*/
/*  Multi-Function constant definitions.                                                                   */
/*---------------------------------------------------------------------------------------------------------*/
/* How to use below #define?
Example 1: If user want to set PA.0 as SC0_CLK in initial function,
           user can issue following command to achieve it.

           SYS->GPA_MFPL  = (SYS->GPA_MFPL & (~SYS_GPA_MFPL_PA0MFP_Msk) ) | SYS_GPA_MFPL_PA0_MFP_SC0_CLK  ;

*/
/********************* Bit definition of GPA_MFPL register **********************/
#define SYS_GPA_MFPL_PA0MFP_GPIO              (0x00UL<<SYS_GPA_MFPL_PA0MFP_Pos)  /*!< General purpose digital I/O pin. \hideinitializer */
#define SYS_GPA_MFPL_PA0MFP_SPIM_MOSI         (0x02UL<<SYS_GPA_MFPL_PA0MFP_Pos)  /*!< 1st SPIM MOSI (Master Out, Slave In) pin. \hideinitializer */
#define SYS_GPA_MFPL_PA0MFP_QSPI0_MOSI0       (0x03UL<<SYS_GPA_MFPL_PA0MFP_Pos)  /*!< 1st QSPI0 MOSI (Master Out, Slave In) pin. \hideinitializer */
#define SYS_GPA_MFPL_PA0MFP_SPI0_MOSI         (0x04UL<<SYS_GPA_MFPL_PA0MFP_Pos)  /*!< 1st SPI0 MOSI (Master Out, Slave In) pin. \hideinitializer */
#define SYS_GPA_MFPL_PA0MFP_SD1_DAT0          (0x05UL<<SYS_GPA_MFPL_PA0MFP_Pos)  /*!< SD/SDIO 1 data line bit 0. \hideinitializer */
#define SYS_GPA_MFPL_PA0MFP_SC0_CLK           (0x06UL<<SYS_GPA_MFPL_PA0MFP_Pos)  /*!< SmartCard0 clock pin. \hideinitializer */
#define SYS_GPA_MFPL_PA0MFP_UART0_RXD         (0x07UL<<SYS_GPA_MFPL_PA0MFP_Pos)  /*!< Data receiver input pin for UART0. \hideinitializer */
#define SYS_GPA_MFPL_PA0MFP_UART1_nRTS        (0x08UL<<SYS_GPA_MFPL_PA0MFP_Pos)  /*!< Request to Send output pin for UART1. \hideinitializer */
#define SYS_GPA_MFPL_PA0MFP_I2C2_SDA          (0x09UL<<SYS_GPA_MFPL_PA0MFP_Pos)  /*!< I2C2 data input/output pin. \hideinitializer */
#define SYS_GPA_MFPL_PA0MFP_CCAP_DATA6        (0x0AUL<<SYS_GPA_MFPL_PA0MFP_Pos)  /*!< Sensor pixel data6 input pin. \hideinitializer */
#define SYS_GPA_MFPL_PA0MFP_BPWM0_CH0         (0x0CUL<<SYS_GPA_MFPL_PA0MFP_Pos)  /*!< BPWM0 channel0 output/capture input. \hideinitializer */
#define SYS_GPA_MFPL_PA0MFP_EPWM0_CH5         (0x0DUL<<SYS_GPA_MFPL_PA0MFP_Pos)  /*!< EPWM0 channel5 output/capture input. \hideinitializer */
#define SYS_GPA_MFPL_PA0MFP_DAC0_ST           (0x0FUL<<SYS_GPA_MFPL_PA0MFP_Pos)  /*!< DAC0 external trigger input. \hideinitializer */
#define SYS_GPA_MFPL_PA1MFP_GPIO              (0x00UL<<SYS_GPA_MFPL_PA1MFP_Pos)  /*!< General purpose digital I/O pin. \hideinitializer */
#define SYS_GPA_MFPL_PA1MFP_SPIM_MISO         (0x02UL<<SYS_GPA_MFPL_PA1MFP_Pos)  /*!< 1st SPIM MISO (Master In, Slave Out) pin. \hideinitializer */
#define SYS_GPA_MFPL_PA1MFP_QSPI0_MISO0       (0x03UL<<SYS_GPA_MFPL_PA1MFP_Pos)  /*!< 1st QSPI0 MISO (Master In, Slave Out) pin. \hideinitializer */
#define SYS_GPA_MFPL_PA1MFP_SPI0_MISO         (0x04UL<<SYS_GPA_MFPL_PA1MFP_Pos)  /*!< 1st SPI0 MISO (Master In, Slave Out) pin. \hideinitializer */
#define SYS_GPA_MFPL_PA1MFP_SD1_DAT1          (0x05UL<<SYS_GPA_MFPL_PA1MFP_Pos)  /*!< SD/SDIO 1 data line bit 1. \hideinitializer */
#define SYS_GPA_MFPL_PA1MFP_SC0_DAT           (0x06UL<<SYS_GPA_MFPL_PA1MFP_Pos)  /*!< SmartCard0 data pin. \hideinitializer */
#define SYS_GPA_MFPL_PA1MFP_UART0_TXD         (0x07UL<<SYS_GPA_MFPL_PA1MFP_Pos)  /*!< Data transmitter output pin for UART0. \hideinitializer */
#define SYS_GPA_MFPL_PA1MFP_UART1_nCTS        (0x08UL<<SYS_GPA_MFPL_PA1MFP_Pos)  /*!< Clear to Send input pin for UART1. \hideinitializer */
#define SYS_GPA_MFPL_PA1MFP_I2C2_SCL          (0x09UL<<SYS_GPA_MFPL_PA1MFP_Pos)  /*!< I2C2 clock pin. \hideinitializer */
#define SYS_GPA_MFPL_PA1MFP_CCAP_DATA7        (0x0AUL<<SYS_GPA_MFPL_PA1MFP_Pos)  /*!< Sensor pixel data7 input pin. \hideinitializer */
#define SYS_GPA_MFPL_PA1MFP_BPWM0_CH1         (0x0CUL<<SYS_GPA_MFPL_PA1MFP_Pos)  /*!< BPWM0 channel1 output/capture input. \hideinitializer */
#define SYS_GPA_MFPL_PA1MFP_EPWM0_CH4         (0x0DUL<<SYS_GPA_MFPL_PA1MFP_Pos)  /*!< EPWM0 channel4 output/capture input. \hideinitializer */
#define SYS_GPA_MFPL_PA1MFP_DAC1_ST           (0x0FUL<<SYS_GPA_MFPL_PA1MFP_Pos)  /*!< DAC1 external trigger input. \hideinitializer */
#define SYS_GPA_MFPL_PA2MFP_GPIO              (0x00UL<<SYS_GPA_MFPL_PA2MFP_Pos)  /*!< General purpose digital I/O pin. \hideinitializer */
#define SYS_GPA_MFPL_PA2MFP_SPIM_CLK          (0x02UL<<SYS_GPA_MFPL_PA2MFP_Pos)  /*!< SPIM serial clock pin. \hideinitializer */
#define SYS_GPA_MFPL_PA2MFP_QSPI0_CLK         (0x03UL<<SYS_GPA_MFPL_PA2MFP_Pos)  /*!< QSPI0 serial clock pin. \hideinitializer */
#define SYS_GPA_MFPL_PA2MFP_SPI0_CLK          (0x04UL<<SYS_GPA_MFPL_PA2MFP_Pos)  /*!< SPI0 serial clock pin. \hideinitializer */
#define SYS_GPA_MFPL_PA2MFP_SD1_DAT2          (0x05UL<<SYS_GPA_MFPL_PA2MFP_Pos)  /*!< SD/SDIO 1 data line bit 2. \hideinitializer */
#define SYS_GPA_MFPL_PA2MFP_SC0_RST           (0x06UL<<SYS_GPA_MFPL_PA2MFP_Pos)  /*!< SmartCard0 reset pin. \hideinitializer */
#define SYS_GPA_MFPL_PA2MFP_UART4_RXD         (0x07UL<<SYS_GPA_MFPL_PA2MFP_Pos)  /*!< Data receiver input pin for UART4. \hideinitializer */
#define SYS_GPA_MFPL_PA2MFP_UART1_RXD         (0x08UL<<SYS_GPA_MFPL_PA2MFP_Pos)  /*!< Data receiver input pin for UART1. \hideinitializer */
#define SYS_GPA_MFPL_PA2MFP_I2C1_SDA          (0x09UL<<SYS_GPA_MFPL_PA2MFP_Pos)  /*!< I2C1 data input/output pin. \hideinitializer */
#define SYS_GPA_MFPL_PA2MFP_I2C0_SMBSUS       (0x0AUL<<SYS_GPA_MFPL_PA2MFP_Pos)  /*!< I2C0 SMBus SMBSUS# pin (PMBus CONTROL pin) \hideinitializer */
#define SYS_GPA_MFPL_PA2MFP_BPWM0_CH2         (0x0CUL<<SYS_GPA_MFPL_PA2MFP_Pos)  /*!< BPWM0 channel2 output/capture input. \hideinitializer */
#define SYS_GPA_MFPL_PA2MFP_EPWM0_CH3         (0x0DUL<<SYS_GPA_MFPL_PA2MFP_Pos)  /*!< EPWM0 channel3 output/capture input. \hideinitializer */
#define SYS_GPA_MFPL_PA3MFP_GPIO              (0x00UL<<SYS_GPA_MFPL_PA3MFP_Pos)  /*!< General purpose digital I/O pin. \hideinitializer */
#define SYS_GPA_MFPL_PA3MFP_SPIM_SS           (0x02UL<<SYS_GPA_MFPL_PA3MFP_Pos)  /*!< 1st SPIM slave select pin. \hideinitializer */
#define SYS_GPA_MFPL_PA3MFP_QSPI0_SS          (0x03UL<<SYS_GPA_MFPL_PA3MFP_Pos)  /*!< 1st QSPI0 slave select pin. \hideinitializer */
#define SYS_GPA_MFPL_PA3MFP_SPI0_SS           (0x04UL<<SYS_GPA_MFPL_PA3MFP_Pos)  /*!< 1st SPI0 slave select pin. \hideinitializer */
#define SYS_GPA_MFPL_PA3MFP_SD1_DAT3          (0x05UL<<SYS_GPA_MFPL_PA3MFP_Pos)  /*!< SD/SDIO 1 data line bit 3. \hideinitializer */
#define SYS_GPA_MFPL_PA3MFP_SC0_PWR           (0x06UL<<SYS_GPA_MFPL_PA3MFP_Pos)  /*!< SmartCard0 power pin. \hideinitializer */
#define SYS_GPA_MFPL_PA3MFP_UART4_TXD         (0x07UL<<SYS_GPA_MFPL_PA3MFP_Pos)  /*!< Data transmitter output pin for UART4. \hideinitializer */
#define SYS_GPA_MFPL_PA3MFP_UART1_TXD         (0x08UL<<SYS_GPA_MFPL_PA3MFP_Pos)  /*!< Data transmitter output pin for UART1. \hideinitializer */
#define SYS_GPA_MFPL_PA3MFP_I2C1_SCL          (0x09UL<<SYS_GPA_MFPL_PA3MFP_Pos)  /*!< I2C1 clock pin. \hideinitializer */
#define SYS_GPA_MFPL_PA3MFP_I2C0_SMBAL        (0x0AUL<<SYS_GPA_MFPL_PA3MFP_Pos)  /*!< I2C0 SMBus SMBALTER# pin. \hideinitializer */
#define SYS_GPA_MFPL_PA3MFP_BPWM0_CH3         (0x0CUL<<SYS_GPA_MFPL_PA3MFP_Pos)  /*!< BPWM0 channel3 output/capture input. \hideinitializer */
#define SYS_GPA_MFPL_PA3MFP_EPWM0_CH2         (0x0DUL<<SYS_GPA_MFPL_PA3MFP_Pos)  /*!< EPWM0 channel2 output/capture input. \hideinitializer */
#define SYS_GPA_MFPL_PA3MFP_QEI0_B            (0x0EUL<<SYS_GPA_MFPL_PA3MFP_Pos)  /*!< Quadrature encoder phase B input of QEI Unit 0. \hideinitializer */
#define SYS_GPA_MFPL_PA3MFP_EPWM1_BRAKE1      (0x0FUL<<SYS_GPA_MFPL_PA3MFP_Pos)  /*!< Brake input pin 1 of EPWM1. \hideinitializer */
#define SYS_GPA_MFPL_PA4MFP_GPIO              (0x00UL<<SYS_GPA_MFPL_PA4MFP_Pos)  /*!< General purpose digital I/O pin. \hideinitializer */
#define SYS_GPA_MFPL_PA4MFP_SPIM_D3           (0x02UL<<SYS_GPA_MFPL_PA4MFP_Pos)  /*!< SPIM data 3 pin for Quad Mode I/O. \hideinitializer */
#define SYS_GPA_MFPL_PA4MFP_QSPI0_MOSI1       (0x03UL<<SYS_GPA_MFPL_PA4MFP_Pos)  /*!< 2nd QSPI0 MOSI (Master Out, Slave In) pin. \hideinitializer */
#define SYS_GPA_MFPL_PA4MFP_SPI0_I2SMCLK      (0x04UL<<SYS_GPA_MFPL_PA4MFP_Pos)  /*!< SPI0 I2S master clock output pin. \hideinitializer */
#define SYS_GPA_MFPL_PA4MFP_SD1_CLK           (0x05UL<<SYS_GPA_MFPL_PA4MFP_Pos)  /*!< SD/SDIO 1 clock. \hideinitializer */
#define SYS_GPA_MFPL_PA4MFP_SC0_nCD           (0x06UL<<SYS_GPA_MFPL_PA4MFP_Pos)  /*!< SmartCard0 card detect pin. \hideinitializer */
#define SYS_GPA_MFPL_PA4MFP_UART0_nRTS        (0x07UL<<SYS_GPA_MFPL_PA4MFP_Pos)  /*!< Request to Send output pin for UART0. \hideinitializer */
#define SYS_GPA_MFPL_PA4MFP_UART5_RXD         (0x08UL<<SYS_GPA_MFPL_PA4MFP_Pos)  /*!< Data receiver input pin for UART5. \hideinitializer */
#define SYS_GPA_MFPL_PA4MFP_I2C0_SDA          (0x09UL<<SYS_GPA_MFPL_PA4MFP_Pos)  /*!< I2C0 data input/output pin. \hideinitializer */
#define SYS_GPA_MFPL_PA4MFP_CAN0_RXD          (0x0AUL<<SYS_GPA_MFPL_PA4MFP_Pos)  /*!< CAN0 bus receiver input. \hideinitializer */
#define SYS_GPA_MFPL_PA4MFP_UART0_RXD         (0x0BUL<<SYS_GPA_MFPL_PA4MFP_Pos)  /*!< Data receiver input pin for UART0. \hideinitializer */
#define SYS_GPA_MFPL_PA4MFP_BPWM0_CH4         (0x0CUL<<SYS_GPA_MFPL_PA4MFP_Pos)  /*!< BPWM0 channel4 output/capture input. \hideinitializer */
#define SYS_GPA_MFPL_PA4MFP_EPWM0_CH1         (0x0DUL<<SYS_GPA_MFPL_PA4MFP_Pos)  /*!< EPWM0 channel1 output/capture input. \hideinitializer */
#define SYS_GPA_MFPL_PA4MFP_QEI0_A            (0x0EUL<<SYS_GPA_MFPL_PA4MFP_Pos)  /*!< Quadrature encoder phase A input of QEI Unit 0. \hideinitializer */
#define SYS_GPA_MFPL_PA5MFP_GPIO              (0x00UL<<SYS_GPA_MFPL_PA5MFP_Pos)  /*!< General purpose digital I/O pin. \hideinitializer */
#define SYS_GPA_MFPL_PA5MFP_SPIM_D2           (0x02UL<<SYS_GPA_MFPL_PA5MFP_Pos)  /*!< SPIM data 2 pin for Quad Mode I/O. \hideinitializer */
#define SYS_GPA_MFPL_PA5MFP_QSPI0_MISO1       (0x03UL<<SYS_GPA_MFPL_PA5MFP_Pos)  /*!< 2nd QSPI0 MISO (Master In, Slave Out) pin. \hideinitializer */
#define SYS_GPA_MFPL_PA5MFP_SPI1_I2SMCLK      (0x04UL<<SYS_GPA_MFPL_PA5MFP_Pos)  /*!< SPI1 I2S master clock output pin. \hideinitializer */
#define SYS_GPA_MFPL_PA5MFP_SD1_CMD           (0x05UL<<SYS_GPA_MFPL_PA5MFP_Pos)  /*!< SD/SDIO 1 command/response. \hideinitializer */
#define SYS_GPA_MFPL_PA5MFP_SC2_nCD           (0x06UL<<SYS_GPA_MFPL_PA5MFP_Pos)  /*!< SmartCard2 card detect pin. \hideinitializer */
#define SYS_GPA_MFPL_PA5MFP_UART0_nCTS        (0x07UL<<SYS_GPA_MFPL_PA5MFP_Pos)  /*!< Clear to Send input pin for UART0. \hideinitializer */
#define SYS_GPA_MFPL_PA5MFP_UART5_TXD         (0x08UL<<SYS_GPA_MFPL_PA5MFP_Pos)  /*!< Data transmitter output pin for UART5. \hideinitializer */
#define SYS_GPA_MFPL_PA5MFP_I2C0_SCL          (0x09UL<<SYS_GPA_MFPL_PA5MFP_Pos)  /*!< I2C0 clock pin. \hideinitializer */
#define SYS_GPA_MFPL_PA5MFP_CAN0_TXD          (0x0AUL<<SYS_GPA_MFPL_PA5MFP_Pos)  /*!< CAN0 bus transmitter output. \hideinitializer */
#define SYS_GPA_MFPL_PA5MFP_UART0_TXD         (0x0BUL<<SYS_GPA_MFPL_PA5MFP_Pos)  /*!< Data transmitter output pin for UART0. \hideinitializer */
#define SYS_GPA_MFPL_PA5MFP_BPWM0_CH5         (0x0CUL<<SYS_GPA_MFPL_PA5MFP_Pos)  /*!< BPWM0 channel5 output/capture input. \hideinitializer */
#define SYS_GPA_MFPL_PA5MFP_EPWM0_CH0         (0x0DUL<<SYS_GPA_MFPL_PA5MFP_Pos)  /*!< EPWM0 channel0 output/capture input. \hideinitializer */
#define SYS_GPA_MFPL_PA5MFP_QEI0_INDEX        (0x0EUL<<SYS_GPA_MFPL_PA5MFP_Pos)  /*!< Quadrature encoder index input of QEI Unit 0. \hideinitializer */
#define SYS_GPA_MFPL_PA6MFP_GPIO              (0x00UL<<SYS_GPA_MFPL_PA6MFP_Pos)  /*!< General purpose digital I/O pin. \hideinitializer */
#define SYS_GPA_MFPL_PA6MFP_EBI_AD6           (0x02UL<<SYS_GPA_MFPL_PA6MFP_Pos)  /*!< EBI address/data bus bit6. \hideinitializer */
#define SYS_GPA_MFPL_PA6MFP_EMAC_RMII_RXERR   (0x03UL<<SYS_GPA_MFPL_PA6MFP_Pos)  /*!< RMII Receive Data error. \hideinitializer */
#define SYS_GPA_MFPL_PA6MFP_SPI1_SS           (0x04UL<<SYS_GPA_MFPL_PA6MFP_Pos)  /*!< 1st SPI1 slave select pin. \hideinitializer */
#define SYS_GPA_MFPL_PA6MFP_SD1_nCD           (0x05UL<<SYS_GPA_MFPL_PA6MFP_Pos)  /*!< SD/SDIO 1 card detect  \hideinitializer */
#define SYS_GPA_MFPL_PA6MFP_SC2_CLK           (0x06UL<<SYS_GPA_MFPL_PA6MFP_Pos)  /*!< SmartCard2 clock pin. \hideinitializer */
#define SYS_GPA_MFPL_PA6MFP_UART0_RXD         (0x07UL<<SYS_GPA_MFPL_PA6MFP_Pos)  /*!< Data receiver input pin for UART0. \hideinitializer */
#define SYS_GPA_MFPL_PA6MFP_I2C1_SDA          (0x08UL<<SYS_GPA_MFPL_PA6MFP_Pos)  /*!< I2C1 data input/output pin. \hideinitializer */
#define SYS_GPA_MFPL_PA6MFP_QSPI1_MOSI1       (0x09UL<<SYS_GPA_MFPL_PA6MFP_Pos)  /*!< 2nd QSPI1 MOSI (Master Out, Slave In) pin. \hideinitializer */
#define SYS_GPA_MFPL_PA6MFP_EPWM1_CH5         (0x0BUL<<SYS_GPA_MFPL_PA6MFP_Pos)  /*!< EPWM1 channel5 output/capture input. \hideinitializer */
#define SYS_GPA_MFPL_PA6MFP_BPWM1_CH3         (0x0CUL<<SYS_GPA_MFPL_PA6MFP_Pos)  /*!< BPWM1 channel3 output/capture input. \hideinitializer */
#define SYS_GPA_MFPL_PA6MFP_ACMP1_WLAT        (0x0DUL<<SYS_GPA_MFPL_PA6MFP_Pos)  /*!< Analog comparator1 window latch input pin. \hideinitializer */
#define SYS_GPA_MFPL_PA6MFP_TM3               (0x0EUL<<SYS_GPA_MFPL_PA6MFP_Pos)  /*!< Timer3 event counter input / toggle output  \hideinitializer */
#define SYS_GPA_MFPL_PA6MFP_INT0              (0x0FUL<<SYS_GPA_MFPL_PA6MFP_Pos)  /*!< External interrupt0 input pin. \hideinitializer */
#define SYS_GPA_MFPL_PA7MFP_GPIO              (0x00UL<<SYS_GPA_MFPL_PA7MFP_Pos)  /*!< General purpose digital I/O pin. \hideinitializer */
#define SYS_GPA_MFPL_PA7MFP_EBI_AD7           (0x02UL<<SYS_GPA_MFPL_PA7MFP_Pos)  /*!< EBI address/data bus bit7. \hideinitializer */
#define SYS_GPA_MFPL_PA7MFP_EMAC_RMII_CRSDV   (0x03UL<<SYS_GPA_MFPL_PA7MFP_Pos)  /*!< MII Receive Data Valid / RMII CRS_DV input. \hideinitializer */
#define SYS_GPA_MFPL_PA7MFP_SPI1_CLK          (0x04UL<<SYS_GPA_MFPL_PA7MFP_Pos)  /*!< SPI1 serial clock pin. \hideinitializer */
#define SYS_GPA_MFPL_PA7MFP_SC2_DAT           (0x06UL<<SYS_GPA_MFPL_PA7MFP_Pos)  /*!< SmartCard2 data pin. \hideinitializer */
#define SYS_GPA_MFPL_PA7MFP_UART0_TXD         (0x07UL<<SYS_GPA_MFPL_PA7MFP_Pos)  /*!< Data transmitter output pin for UART0. \hideinitializer */
#define SYS_GPA_MFPL_PA7MFP_I2C1_SCL          (0x08UL<<SYS_GPA_MFPL_PA7MFP_Pos)  /*!< I2C1 clock pin. \hideinitializer */
#define SYS_GPA_MFPL_PA7MFP_QSPI1_MISO1       (0x09UL<<SYS_GPA_MFPL_PA7MFP_Pos)  /*!< 2nd QSPI1 MISO (Master In, Slave Out) pin. \hideinitializer */
#define SYS_GPA_MFPL_PA7MFP_EPWM1_CH4         (0x0BUL<<SYS_GPA_MFPL_PA7MFP_Pos)  /*!< EPWM1 channel4 output/capture input. \hideinitializer */
#define SYS_GPA_MFPL_PA7MFP_BPWM1_CH2         (0x0CUL<<SYS_GPA_MFPL_PA7MFP_Pos)  /*!< BPWM1 channel2 output/capture input. \hideinitializer */
#define SYS_GPA_MFPL_PA7MFP_ACMP0_WLAT        (0x0DUL<<SYS_GPA_MFPL_PA7MFP_Pos)  /*!< Analog comparator0 window latch input pin. \hideinitializer */
#define SYS_GPA_MFPL_PA7MFP_TM2               (0x0EUL<<SYS_GPA_MFPL_PA7MFP_Pos)  /*!< Timer2 event counter input / toggle output  \hideinitializer */
#define SYS_GPA_MFPL_PA7MFP_INT1              (0x0FUL<<SYS_GPA_MFPL_PA7MFP_Pos)  /*!< External interrupt1 input pin. \hideinitializer */
/********************* Bit definition of GPA_MFPH register **********************/
#define SYS_GPA_MFPH_PA8MFP_GPIO              (0x00UL<<SYS_GPA_MFPH_PA8MFP_Pos)  /*!< General purpose digital I/O pin. \hideinitializer */
#define SYS_GPA_MFPH_PA8MFP_OPA1_P            (0x01UL<<SYS_GPA_MFPH_PA8MFP_Pos)  /*!< Operational amplifier positive input pin. \hideinitializer */
#define SYS_GPA_MFPH_PA8MFP_EADC1_CH4         (0x01UL<<SYS_GPA_MFPH_PA8MFP_Pos)  /*!< EADC1 channel4 analog input. \hideinitializer */
#define SYS_GPA_MFPH_PA8MFP_EBI_ALE           (0x02UL<<SYS_GPA_MFPH_PA8MFP_Pos)  /*!< EBI address latch enable output pin. \hideinitializer */
#define SYS_GPA_MFPH_PA8MFP_SC2_CLK           (0x03UL<<SYS_GPA_MFPH_PA8MFP_Pos)  /*!< SmartCard2 clock pin. \hideinitializer */
#define SYS_GPA_MFPH_PA8MFP_SPI2_MOSI         (0x04UL<<SYS_GPA_MFPH_PA8MFP_Pos)  /*!< 1st SPI2 MOSI (Master Out, Slave In) pin. \hideinitializer */
#define SYS_GPA_MFPH_PA8MFP_SD1_DAT0          (0x05UL<<SYS_GPA_MFPH_PA8MFP_Pos)  /*!< SD/SDIO 1 data line bit 0. \hideinitializer */
#define SYS_GPA_MFPH_PA8MFP_USCI0_CTL1        (0x06UL<<SYS_GPA_MFPH_PA8MFP_Pos)  /*!< USCI0 control1 pin. \hideinitializer */
#define SYS_GPA_MFPH_PA8MFP_UART1_RXD         (0x07UL<<SYS_GPA_MFPH_PA8MFP_Pos)  /*!< Data receiver input pin for UART1. \hideinitializer */
#define SYS_GPA_MFPH_PA8MFP_UART7_RXD         (0x08UL<<SYS_GPA_MFPH_PA8MFP_Pos)  /*!< Data receiver input pin for UART7. \hideinitializer */
#define SYS_GPA_MFPH_PA8MFP_BPWM0_CH3         (0x09UL<<SYS_GPA_MFPH_PA8MFP_Pos)  /*!< BPWM0 channel3 output/capture input. \hideinitializer */
#define SYS_GPA_MFPH_PA8MFP_QEI1_B            (0x0AUL<<SYS_GPA_MFPH_PA8MFP_Pos)  /*!< Quadrature encoder phase B input of QEI Unit 1. \hideinitializer */
#define SYS_GPA_MFPH_PA8MFP_ECAP0_IC2         (0x0BUL<<SYS_GPA_MFPH_PA8MFP_Pos)  /*!< Input 0 of enhanced capture unit 2. \hideinitializer */
#define SYS_GPA_MFPH_PA8MFP_TM3_EXT           (0x0DUL<<SYS_GPA_MFPH_PA8MFP_Pos)  /*!< Timer3 event counter input / toggle output  \hideinitializer */
#define SYS_GPA_MFPH_PA8MFP_INT4              (0x0FUL<<SYS_GPA_MFPH_PA8MFP_Pos)  /*!< External interrupt4 input pin. \hideinitializer */
#define SYS_GPA_MFPH_PA9MFP_GPIO              (0x00UL<<SYS_GPA_MFPH_PA9MFP_Pos)  /*!< General purpose digital I/O pin. \hideinitializer */
#define SYS_GPA_MFPH_PA9MFP_OPA1_N            (0x01UL<<SYS_GPA_MFPH_PA9MFP_Pos)  /*!< Operational amplifier negative input pin. \hideinitializer */
#define SYS_GPA_MFPH_PA9MFP_EADC1_CH5         (0x01UL<<SYS_GPA_MFPH_PA9MFP_Pos)  /*!< EADC1 channel5 analog input. \hideinitializer */
#define SYS_GPA_MFPH_PA9MFP_EBI_MCLK          (0x02UL<<SYS_GPA_MFPH_PA9MFP_Pos)  /*!< EBI external clock output pin. \hideinitializer */
#define SYS_GPA_MFPH_PA9MFP_SC2_DAT           (0x03UL<<SYS_GPA_MFPH_PA9MFP_Pos)  /*!< SmartCard2 data pin. \hideinitializer */
#define SYS_GPA_MFPH_PA9MFP_SPI2_MISO         (0x04UL<<SYS_GPA_MFPH_PA9MFP_Pos)  /*!< 1st SPI2 MISO (Master In, Slave Out) pin. \hideinitializer */
#define SYS_GPA_MFPH_PA9MFP_SD1_DAT1          (0x05UL<<SYS_GPA_MFPH_PA9MFP_Pos)  /*!< SD/SDIO 1 data line bit 1. \hideinitializer */
#define SYS_GPA_MFPH_PA9MFP_USCI0_DAT1        (0x06UL<<SYS_GPA_MFPH_PA9MFP_Pos)  /*!< USCI0 data1 pin. \hideinitializer */
#define SYS_GPA_MFPH_PA9MFP_UART1_TXD         (0x07UL<<SYS_GPA_MFPH_PA9MFP_Pos)  /*!< Data transmitter output pin for UART1. \hideinitializer */
#define SYS_GPA_MFPH_PA9MFP_UART7_TXD         (0x08UL<<SYS_GPA_MFPH_PA9MFP_Pos)  /*!< Data transmitter output pin for UART7. \hideinitializer */
#define SYS_GPA_MFPH_PA9MFP_BPWM0_CH2         (0x09UL<<SYS_GPA_MFPH_PA9MFP_Pos)  /*!< BPWM0 channel2 output/capture input. \hideinitializer */
#define SYS_GPA_MFPH_PA9MFP_QEI1_A            (0x0AUL<<SYS_GPA_MFPH_PA9MFP_Pos)  /*!< Quadrature encoder phase A input of QEI Unit 1. \hideinitializer */
#define SYS_GPA_MFPH_PA9MFP_ECAP0_IC1         (0x0BUL<<SYS_GPA_MFPH_PA9MFP_Pos)  /*!< Input 1 of enhanced capture unit 0. \hideinitializer */
#define SYS_GPA_MFPH_PA9MFP_TM2_EXT           (0x0DUL<<SYS_GPA_MFPH_PA9MFP_Pos)  /*!< Timer2 event counter input / toggle output  \hideinitializer */
#define SYS_GPA_MFPH_PA9MFP_SWDH_DAT          (0x0FUL<<SYS_GPA_MFPH_PA9MFP_Pos)  /*!< SWD Host interface input/output bus bit. \hideinitializer */
#define SYS_GPA_MFPH_PA10MFP_GPIO             (0x00UL<<SYS_GPA_MFPH_PA10MFP_Pos) /*!< General purpose digital I/O pin. \hideinitializer */
#define SYS_GPA_MFPH_PA10MFP_ACMP1_P0         (0x01UL<<SYS_GPA_MFPH_PA10MFP_Pos) /*!< Analog comparator1 positive input pin. \hideinitializer */
#define SYS_GPA_MFPH_PA10MFP_OPA1_O           (0x01UL<<SYS_GPA_MFPH_PA10MFP_Pos) /*!< Operational amplifier output pin. \hideinitializer */
#define SYS_GPA_MFPH_PA10MFP_EADC1_CH6        (0x01UL<<SYS_GPA_MFPH_PA10MFP_Pos) /*!< EADC1 channel6 analog input. \hideinitializer */
#define SYS_GPA_MFPH_PA10MFP_EBI_nWR          (0x02UL<<SYS_GPA_MFPH_PA10MFP_Pos) /*!< EBI write enable output pin. \hideinitializer */
#define SYS_GPA_MFPH_PA10MFP_SC2_RST          (0x03UL<<SYS_GPA_MFPH_PA10MFP_Pos) /*!< SmartCard2 reset pin. \hideinitializer */
#define SYS_GPA_MFPH_PA10MFP_SPI2_CLK         (0x04UL<<SYS_GPA_MFPH_PA10MFP_Pos) /*!< SPI2 serial clock pin. \hideinitializer */
#define SYS_GPA_MFPH_PA10MFP_SD1_DAT2         (0x05UL<<SYS_GPA_MFPH_PA10MFP_Pos) /*!< SD/SDIO 1 data line bit 2. \hideinitializer */
#define SYS_GPA_MFPH_PA10MFP_USCI0_DAT0       (0x06UL<<SYS_GPA_MFPH_PA10MFP_Pos) /*!< USCI0 data0 pin. \hideinitializer */
#define SYS_GPA_MFPH_PA10MFP_I2C2_SDA         (0x07UL<<SYS_GPA_MFPH_PA10MFP_Pos) /*!< I2C2 data input/output pin. \hideinitializer */
#define SYS_GPA_MFPH_PA10MFP_UART6_RXD        (0x08UL<<SYS_GPA_MFPH_PA10MFP_Pos) /*!< Data receiver input pin for UART6. \hideinitializer */
#define SYS_GPA_MFPH_PA10MFP_BPWM0_CH1        (0x09UL<<SYS_GPA_MFPH_PA10MFP_Pos) /*!< BPWM0 channel1 output/capture input. \hideinitializer */
#define SYS_GPA_MFPH_PA10MFP_QEI1_INDEX       (0x0AUL<<SYS_GPA_MFPH_PA10MFP_Pos) /*!< Quadrature encoder index input of QEI Unit 1. \hideinitializer */
#define SYS_GPA_MFPH_PA10MFP_ECAP0_IC0        (0x0BUL<<SYS_GPA_MFPH_PA10MFP_Pos) /*!< Input 0 of enhanced capture unit 0. \hideinitializer */
#define SYS_GPA_MFPH_PA10MFP_TM1_EXT          (0x0DUL<<SYS_GPA_MFPH_PA10MFP_Pos) /*!< Timer1 event counter input / toggle output  \hideinitializer */
#define SYS_GPA_MFPH_PA10MFP_DAC0_ST          (0x0EUL<<SYS_GPA_MFPH_PA10MFP_Pos) /*!< DAC0 external trigger input. \hideinitializer */
#define SYS_GPA_MFPH_PA10MFP_SWDH_CLK         (0x0FUL<<SYS_GPA_MFPH_PA10MFP_Pos) /*!< SWD Host interface clock output pin. \hideinitializer */
#define SYS_GPA_MFPH_PA11MFP_GPIO             (0x00UL<<SYS_GPA_MFPH_PA11MFP_Pos) /*!< General purpose digital I/O pin. \hideinitializer */
#define SYS_GPA_MFPH_PA11MFP_ACMP0_P0         (0x01UL<<SYS_GPA_MFPH_PA11MFP_Pos) /*!< Analog comparator0 positive input pin. \hideinitializer */
#define SYS_GPA_MFPH_PA11MFP_EADC1_CH7        (0x01UL<<SYS_GPA_MFPH_PA11MFP_Pos) /*!< EADC1 channel7 analog input. \hideinitializer */
#define SYS_GPA_MFPH_PA11MFP_EBI_nRD          (0x02UL<<SYS_GPA_MFPH_PA11MFP_Pos) /*!< EBI read enable output pin. \hideinitializer */
#define SYS_GPA_MFPH_PA11MFP_SC2_PWR          (0x03UL<<SYS_GPA_MFPH_PA11MFP_Pos) /*!< SmartCard2 power pin. \hideinitializer */
#define SYS_GPA_MFPH_PA11MFP_SPI2_SS          (0x04UL<<SYS_GPA_MFPH_PA11MFP_Pos) /*!< 1st SPI2 slave select pin. \hideinitializer */
#define SYS_GPA_MFPH_PA11MFP_SD1_DAT3         (0x05UL<<SYS_GPA_MFPH_PA11MFP_Pos) /*!< SD/SDIO 1 data line bit 3. \hideinitializer */
#define SYS_GPA_MFPH_PA11MFP_USCI0_CLK        (0x06UL<<SYS_GPA_MFPH_PA11MFP_Pos) /*!< USCI0 clock pin. \hideinitializer */
#define SYS_GPA_MFPH_PA11MFP_I2C2_SCL         (0x07UL<<SYS_GPA_MFPH_PA11MFP_Pos) /*!< I2C2 clock pin. \hideinitializer */
#define SYS_GPA_MFPH_PA11MFP_UART6_TXD        (0x08UL<<SYS_GPA_MFPH_PA11MFP_Pos) /*!< Data transmitter output pin for UART6. \hideinitializer */
#define SYS_GPA_MFPH_PA11MFP_BPWM0_CH0        (0x09UL<<SYS_GPA_MFPH_PA11MFP_Pos) /*!< BPWM0 channel0 output/capture input. \hideinitializer */
#define SYS_GPA_MFPH_PA11MFP_EPWM0_SYNC_OUT   (0x0AUL<<SYS_GPA_MFPH_PA11MFP_Pos) /*!< EPWM0 counter synchronous trigger output pin. \hideinitializer */
#define SYS_GPA_MFPH_PA11MFP_TM0_EXT          (0x0DUL<<SYS_GPA_MFPH_PA11MFP_Pos) /*!< Timer0 event counter input / toggle output \hideinitializer */
#define SYS_GPA_MFPH_PA11MFP_DAC1_ST          (0x0EUL<<SYS_GPA_MFPH_PA11MFP_Pos) /*!< DAC1 external trigger input. \hideinitializer */
#define SYS_GPA_MFPH_PA12MFP_GPIO             (0x00UL<<SYS_GPA_MFPH_PA12MFP_Pos) /*!< General purpose digital I/O pin. \hideinitializer */
#define SYS_GPA_MFPH_PA12MFP_I2S0_BCLK        (0x02UL<<SYS_GPA_MFPH_PA12MFP_Pos) /*!< I2S0 bit clock pin. \hideinitializer */
#define SYS_GPA_MFPH_PA12MFP_UART4_TXD        (0x03UL<<SYS_GPA_MFPH_PA12MFP_Pos) /*!< Data transmitter output pin for UART4. \hideinitializer */
#define SYS_GPA_MFPH_PA12MFP_I2C1_SCL         (0x04UL<<SYS_GPA_MFPH_PA12MFP_Pos) /*!< I2C1 clock pin. \hideinitializer */
#define SYS_GPA_MFPH_PA12MFP_SPI2_SS          (0x05UL<<SYS_GPA_MFPH_PA12MFP_Pos) /*!< 1st SPI2 slave select pin. \hideinitializer */
#define SYS_GPA_MFPH_PA12MFP_CAN0_TXD         (0x06UL<<SYS_GPA_MFPH_PA12MFP_Pos) /*!< CAN0 bus transmitter output. \hideinitializer */
#define SYS_GPA_MFPH_PA12MFP_SC2_PWR          (0x07UL<<SYS_GPA_MFPH_PA12MFP_Pos) /*!< SmartCard2 power pin. \hideinitializer */
#define SYS_GPA_MFPH_PA12MFP_BPWM1_CH2        (0x0BUL<<SYS_GPA_MFPH_PA12MFP_Pos) /*!< BPWM1 channel2 output/capture input. \hideinitializer */
#define SYS_GPA_MFPH_PA12MFP_QEI1_INDEX       (0x0CUL<<SYS_GPA_MFPH_PA12MFP_Pos) /*!< Quadrature encoder index input of QEI Unit 1. \hideinitializer */
#define SYS_GPA_MFPH_PA12MFP_USB_VBUS         (0x0EUL<<SYS_GPA_MFPH_PA12MFP_Pos) /*!< Power supply from USB Full speed host or HUB. \hideinitializer */
#define SYS_GPA_MFPH_PA13MFP_GPIO             (0x00UL<<SYS_GPA_MFPH_PA13MFP_Pos) /*!< General purpose digital I/O pin. \hideinitializer */
#define SYS_GPA_MFPH_PA13MFP_I2S0_MCLK        (0x02UL<<SYS_GPA_MFPH_PA13MFP_Pos) /*!< I2S0 master clock output pin. \hideinitializer */
#define SYS_GPA_MFPH_PA13MFP_UART4_RXD        (0x03UL<<SYS_GPA_MFPH_PA13MFP_Pos) /*!< Data receiver input pin for UART4. \hideinitializer */
#define SYS_GPA_MFPH_PA13MFP_I2C1_SDA         (0x04UL<<SYS_GPA_MFPH_PA13MFP_Pos) /*!< I2C1 data input/output pin. \hideinitializer */
#define SYS_GPA_MFPH_PA13MFP_SPI2_CLK         (0x05UL<<SYS_GPA_MFPH_PA13MFP_Pos) /*!< SPI2 serial clock pin. \hideinitializer */
#define SYS_GPA_MFPH_PA13MFP_CAN0_RXD         (0x06UL<<SYS_GPA_MFPH_PA13MFP_Pos) /*!< CAN0 bus receiver input. \hideinitializer */
#define SYS_GPA_MFPH_PA13MFP_SC2_RST          (0x07UL<<SYS_GPA_MFPH_PA13MFP_Pos) /*!< SmartCard2 reset pin. \hideinitializer */
#define SYS_GPA_MFPH_PA13MFP_BPWM1_CH3        (0x0BUL<<SYS_GPA_MFPH_PA13MFP_Pos) /*!< BPWM1 channel3 output/capture input. \hideinitializer */
#define SYS_GPA_MFPH_PA13MFP_QEI1_A           (0x0CUL<<SYS_GPA_MFPH_PA13MFP_Pos) /*!< Quadrature encoder phase A input of QEI Unit 1. \hideinitializer */
#define SYS_GPA_MFPH_PA13MFP_USB_D_N          (0x0EUL<<SYS_GPA_MFPH_PA13MFP_Pos) /*!< USB Full speed differential signal D-. \hideinitializer */
#define SYS_GPA_MFPH_PA14MFP_GPIO             (0x00UL<<SYS_GPA_MFPH_PA14MFP_Pos) /*!< General purpose digital I/O pin. \hideinitializer */
#define SYS_GPA_MFPH_PA14MFP_I2S0_DI          (0x02UL<<SYS_GPA_MFPH_PA14MFP_Pos) /*!< I2S0 data input. \hideinitializer */
#define SYS_GPA_MFPH_PA14MFP_UART0_TXD        (0x03UL<<SYS_GPA_MFPH_PA14MFP_Pos) /*!< Data transmitter output pin for UART0. \hideinitializer */
#define SYS_GPA_MFPH_PA14MFP_SPI2_MISO        (0x05UL<<SYS_GPA_MFPH_PA14MFP_Pos) /*!< 1st SPI2 MISO (Master In, Slave Out) pin. \hideinitializer */
#define SYS_GPA_MFPH_PA14MFP_I2C2_SCL         (0x06UL<<SYS_GPA_MFPH_PA14MFP_Pos) /*!< I2C2 clock pin. \hideinitializer */
#define SYS_GPA_MFPH_PA14MFP_SC2_DAT          (0x07UL<<SYS_GPA_MFPH_PA14MFP_Pos) /*!< SmartCard2 data pin. \hideinitializer */
#define SYS_GPA_MFPH_PA14MFP_BPWM1_CH4        (0x0BUL<<SYS_GPA_MFPH_PA14MFP_Pos) /*!< BPWM1 channel4 output/capture input. \hideinitializer */
#define SYS_GPA_MFPH_PA14MFP_QEI1_B           (0x0CUL<<SYS_GPA_MFPH_PA14MFP_Pos) /*!< Quadrature encoder phase B input of QEI Unit 1. \hideinitializer */
#define SYS_GPA_MFPH_PA14MFP_USB_D_P          (0x0EUL<<SYS_GPA_MFPH_PA14MFP_Pos) /*!< USB Full speed differential signal D+. \hideinitializer */
#define SYS_GPA_MFPH_PA15MFP_GPIO             (0x00UL<<SYS_GPA_MFPH_PA15MFP_Pos) /*!< General purpose digital I/O pin. \hideinitializer */
#define SYS_GPA_MFPH_PA15MFP_I2S0_DO          (0x02UL<<SYS_GPA_MFPH_PA15MFP_Pos) /*!< I2S0 data output. \hideinitializer */
#define SYS_GPA_MFPH_PA15MFP_UART0_RXD        (0x03UL<<SYS_GPA_MFPH_PA15MFP_Pos) /*!< Data receiver input pin for UART0. \hideinitializer */
#define SYS_GPA_MFPH_PA15MFP_SPI2_MOSI        (0x05UL<<SYS_GPA_MFPH_PA15MFP_Pos) /*!< 1st SPI2 MOSI (Master Out, Slave In) pin. \hideinitializer */
#define SYS_GPA_MFPH_PA15MFP_I2C2_SDA         (0x06UL<<SYS_GPA_MFPH_PA15MFP_Pos) /*!< I2C2 data input/output pin. \hideinitializer */
#define SYS_GPA_MFPH_PA15MFP_SC2_CLK          (0x07UL<<SYS_GPA_MFPH_PA15MFP_Pos) /*!< SmartCard2 clock pin. \hideinitializer */
#define SYS_GPA_MFPH_PA15MFP_BPWM1_CH5        (0x0BUL<<SYS_GPA_MFPH_PA15MFP_Pos) /*!< BPWM1 channel5 output/capture input. \hideinitializer */
#define SYS_GPA_MFPH_PA15MFP_EPWM0_SYNC_IN    (0x0CUL<<SYS_GPA_MFPH_PA15MFP_Pos) /*!< EPWM0 counter synchronous trigger input pin. \hideinitializer */
#define SYS_GPA_MFPH_PA15MFP_USB_OTG_ID       (0x0EUL<<SYS_GPA_MFPH_PA15MFP_Pos) /*!< USB Full speed identification. \hideinitializer */
/********************* Bit definition of GPB_MFPL register **********************/
#define SYS_GPB_MFPL_PB0MFP_GPIO              (0x00UL<<SYS_GPB_MFPL_PB0MFP_Pos)  /*!< General purpose digital I/O pin. \hideinitializer */
#define SYS_GPB_MFPL_PB0MFP_EADC0_CH0         (0x01UL<<SYS_GPB_MFPL_PB0MFP_Pos)  /*!< EADC0 channel0 analog input. \hideinitializer */
#define SYS_GPB_MFPL_PB0MFP_EADC1_CH8         (0x01UL<<SYS_GPB_MFPL_PB0MFP_Pos)  /*!< EADC1 channel8 analog input. \hideinitializer */
#define SYS_GPB_MFPL_PB0MFP_OPA0_P            (0x01UL<<SYS_GPB_MFPL_PB0MFP_Pos)  /*!< Operational amplifier positive input pin. \hideinitializer */
#define SYS_GPB_MFPL_PB0MFP_EBI_ADR9          (0x02UL<<SYS_GPB_MFPL_PB0MFP_Pos)  /*!< EBI address/data bus bit*. \hideinitializer */
#define SYS_GPB_MFPL_PB0MFP_SD0_CMD           (0x03UL<<SYS_GPB_MFPL_PB0MFP_Pos)  /*!< SD/SDIO 0 command/response. \hideinitializer */
#define SYS_GPB_MFPL_PB0MFP_SPI2_I2SMCLK      (0x04UL<<SYS_GPB_MFPL_PB0MFP_Pos)  /*!< SPI2 I2S master clock output pin. \hideinitializer */
#define SYS_GPB_MFPL_PB0MFP_UART2_RXD         (0x07UL<<SYS_GPB_MFPL_PB0MFP_Pos)  /*!< Data receiver input pin for UART2. \hideinitializer */
#define SYS_GPB_MFPL_PB0MFP_SPI0_I2SMCLK      (0x08UL<<SYS_GPB_MFPL_PB0MFP_Pos)  /*!< SPI0 I2S master clock output pin. \hideinitializer */
#define SYS_GPB_MFPL_PB0MFP_I2C1_SDA          (0x09UL<<SYS_GPB_MFPL_PB0MFP_Pos)  /*!< I2C1 data input/output pin. \hideinitializer */
#define SYS_GPB_MFPL_PB0MFP_EPWM0_CH5         (0x0BUL<<SYS_GPB_MFPL_PB0MFP_Pos)  /*!< EPWM0 channel5 output/capture input. \hideinitializer */
#define SYS_GPB_MFPL_PB0MFP_EPWM1_CH5         (0x0CUL<<SYS_GPB_MFPL_PB0MFP_Pos)  /*!< EPWM1 channel5 output/capture input. \hideinitializer */
#define SYS_GPB_MFPL_PB0MFP_EPWM0_BRAKE1      (0x0DUL<<SYS_GPB_MFPL_PB0MFP_Pos)  /*!< Brake input pin 1 of EPWM0. \hideinitializer */
#define SYS_GPB_MFPL_PB1MFP_GPIO              (0x00UL<<SYS_GPB_MFPL_PB1MFP_Pos)  /*!< General purpose digital I/O pin. \hideinitializer */
#define SYS_GPB_MFPL_PB1MFP_EADC0_CH1         (0x01UL<<SYS_GPB_MFPL_PB1MFP_Pos)  /*!< EADC0 channel1 analog input. \hideinitializer */
#define SYS_GPB_MFPL_PB1MFP_OPA0_N            (0x01UL<<SYS_GPB_MFPL_PB1MFP_Pos)  /*!< Operational amplifier negative input pin. \hideinitializer */
#define SYS_GPB_MFPL_PB1MFP_EADC1_CH9         (0x01UL<<SYS_GPB_MFPL_PB1MFP_Pos)  /*!< EADC1 channel9 analog input. \hideinitializer */
#define SYS_GPB_MFPL_PB1MFP_EBI_ADR8          (0x02UL<<SYS_GPB_MFPL_PB1MFP_Pos)  /*!< EBI address/data bus bit*. \hideinitializer */
#define SYS_GPB_MFPL_PB1MFP_SD0_CLK           (0x03UL<<SYS_GPB_MFPL_PB1MFP_Pos)  /*!< SD/SDIO 0 clock. \hideinitializer */
#define SYS_GPB_MFPL_PB1MFP_EMAC_RMII_RXERR   (0x04UL<<SYS_GPB_MFPL_PB1MFP_Pos)  /*!< RMII Receive Data error. \hideinitializer */
#define SYS_GPB_MFPL_PB1MFP_SPI1_I2SMCLK      (0x05UL<<SYS_GPB_MFPL_PB1MFP_Pos)  /*!< SPI1 I2S master clock output pin. \hideinitializer */
#define SYS_GPB_MFPL_PB1MFP_SPI3_I2SMCLK      (0x06UL<<SYS_GPB_MFPL_PB1MFP_Pos)  /*!< SPI3 I2S master clock output pin. \hideinitializer */
#define SYS_GPB_MFPL_PB1MFP_UART2_TXD         (0x07UL<<SYS_GPB_MFPL_PB1MFP_Pos)  /*!< Data transmitter output pin for UART2. \hideinitializer */
#define SYS_GPB_MFPL_PB1MFP_USCI1_CLK         (0x08UL<<SYS_GPB_MFPL_PB1MFP_Pos)  /*!< USCI1 clock pin. \hideinitializer */
#define SYS_GPB_MFPL_PB1MFP_I2C1_SCL          (0x09UL<<SYS_GPB_MFPL_PB1MFP_Pos)  /*!< I2C1 clock pin. \hideinitializer */
#define SYS_GPB_MFPL_PB1MFP_I2S0_LRCK         (0x0AUL<<SYS_GPB_MFPL_PB1MFP_Pos)  /*!< I2S0 left right channel clock. \hideinitializer */
#define SYS_GPB_MFPL_PB1MFP_EPWM0_CH4         (0x0BUL<<SYS_GPB_MFPL_PB1MFP_Pos)  /*!< EPWM0 channel4 output/capture input. \hideinitializer */
#define SYS_GPB_MFPL_PB1MFP_EPWM1_CH4         (0x0CUL<<SYS_GPB_MFPL_PB1MFP_Pos)  /*!< EPWM1 channel4 output/capture input. \hideinitializer */
#define SYS_GPB_MFPL_PB1MFP_EPWM0_BRAKE0      (0x0DUL<<SYS_GPB_MFPL_PB1MFP_Pos)  /*!< Brake input pin 0 of EPWM0. \hideinitializer */
#define SYS_GPB_MFPL_PB2MFP_GPIO              (0x00UL<<SYS_GPB_MFPL_PB2MFP_Pos)  /*!< General purpose digital I/O pin. \hideinitializer */
#define SYS_GPB_MFPL_PB2MFP_ACMP0_P1          (0x01UL<<SYS_GPB_MFPL_PB2MFP_Pos)  /*!< Analog comparator0 positive input pin. \hideinitializer */
#define SYS_GPB_MFPL_PB2MFP_EADC0_CH2         (0x01UL<<SYS_GPB_MFPL_PB2MFP_Pos)  /*!< EADC0 channel2 analog input. \hideinitializer */
#define SYS_GPB_MFPL_PB2MFP_OPA0_O            (0x01UL<<SYS_GPB_MFPL_PB2MFP_Pos)  /*!< Operational amplifier output pin. \hideinitializer */
#define SYS_GPB_MFPL_PB2MFP_EADC1_CH10        (0x01UL<<SYS_GPB_MFPL_PB2MFP_Pos)  /*!< EADC1 channel1 analog input. \hideinitializer */
#define SYS_GPB_MFPL_PB2MFP_EBI_ADR3          (0x02UL<<SYS_GPB_MFPL_PB2MFP_Pos)  /*!< EBI address/data bus bit*. \hideinitializer */
#define SYS_GPB_MFPL_PB2MFP_SD0_DAT0          (0x03UL<<SYS_GPB_MFPL_PB2MFP_Pos)  /*!< SD/SDIO 0 data line bit 0. \hideinitializer */
#define SYS_GPB_MFPL_PB2MFP_EMAC_RMII_CRSDV   (0x04UL<<SYS_GPB_MFPL_PB2MFP_Pos)  /*!< MII Receive Data Valid / RMII CRS_DV input. \hideinitializer */
#define SYS_GPB_MFPL_PB2MFP_SPI1_SS           (0x05UL<<SYS_GPB_MFPL_PB2MFP_Pos)  /*!< 1st SPI1 slave select pin. \hideinitializer */
#define SYS_GPB_MFPL_PB2MFP_UART1_RXD         (0x06UL<<SYS_GPB_MFPL_PB2MFP_Pos)  /*!< Data receiver input pin for UART1. \hideinitializer */
#define SYS_GPB_MFPL_PB2MFP_UART5_nCTS        (0x07UL<<SYS_GPB_MFPL_PB2MFP_Pos)  /*!< Clear to Send input pin for UART5. \hideinitializer */
#define SYS_GPB_MFPL_PB2MFP_USCI1_DAT0        (0x08UL<<SYS_GPB_MFPL_PB2MFP_Pos)  /*!< USCI1 data0 pin. \hideinitializer */
#define SYS_GPB_MFPL_PB2MFP_SC0_PWR           (0x09UL<<SYS_GPB_MFPL_PB2MFP_Pos)  /*!< SmartCard0 power pin. \hideinitializer */
#define SYS_GPB_MFPL_PB2MFP_I2S0_DO           (0x0AUL<<SYS_GPB_MFPL_PB2MFP_Pos)  /*!< I2S0 data output. \hideinitializer */
#define SYS_GPB_MFPL_PB2MFP_EPWM0_CH3         (0x0BUL<<SYS_GPB_MFPL_PB2MFP_Pos)  /*!< EPWM0 channel3 output/capture input. \hideinitializer */
#define SYS_GPB_MFPL_PB2MFP_I2C1_SDA          (0x0CUL<<SYS_GPB_MFPL_PB2MFP_Pos)  /*!< I2C1 data input/output pin. */
#define SYS_GPB_MFPL_PB2MFP_TM3               (0x0EUL<<SYS_GPB_MFPL_PB2MFP_Pos)  /*!< Timer3 event counter input / toggle output  \hideinitializer */
#define SYS_GPB_MFPL_PB2MFP_INT3              (0x0FUL<<SYS_GPB_MFPL_PB2MFP_Pos)  /*!< External interrupt3 input pin. \hideinitializer */
#define SYS_GPB_MFPL_PB3MFP_GPIO              (0x00UL<<SYS_GPB_MFPL_PB3MFP_Pos)  /*!< General purpose digital I/O pin. \hideinitializer */
#define SYS_GPB_MFPL_PB3MFP_ACMP0_N           (0x01UL<<SYS_GPB_MFPL_PB3MFP_Pos)  /*!< Analog comparator0 negative input pin. \hideinitializer */
#define SYS_GPB_MFPL_PB3MFP_EADC0_CH3         (0x01UL<<SYS_GPB_MFPL_PB3MFP_Pos)  /*!< EADC0 channel3 analog input. \hideinitializer */
#define SYS_GPB_MFPL_PB3MFP_EADC1_CH11        (0x01UL<<SYS_GPB_MFPL_PB3MFP_Pos)  /*!< EADC1 channel1 analog input. \hideinitializer */
#define SYS_GPB_MFPL_PB3MFP_EBI_ADR2          (0x02UL<<SYS_GPB_MFPL_PB3MFP_Pos)  /*!< EBI address/data bus bit*. \hideinitializer */
#define SYS_GPB_MFPL_PB3MFP_SD0_DAT1          (0x03UL<<SYS_GPB_MFPL_PB3MFP_Pos)  /*!< SD/SDIO 0 data line bit 1. \hideinitializer */
#define SYS_GPB_MFPL_PB3MFP_EMAC_RMII_RXD1    (0x04UL<<SYS_GPB_MFPL_PB3MFP_Pos)  /*!< RMII Receive Data bus bit 1. \hideinitializer */
#define SYS_GPB_MFPL_PB3MFP_SPI1_CLK          (0x05UL<<SYS_GPB_MFPL_PB3MFP_Pos)  /*!< SPI1 serial clock pin. \hideinitializer */
#define SYS_GPB_MFPL_PB3MFP_UART1_TXD         (0x06UL<<SYS_GPB_MFPL_PB3MFP_Pos)  /*!< Data transmitter output pin for UART1. \hideinitializer */
#define SYS_GPB_MFPL_PB3MFP_UART5_nRTS        (0x07UL<<SYS_GPB_MFPL_PB3MFP_Pos)  /*!< Request to Send output pin for UART5. \hideinitializer */
#define SYS_GPB_MFPL_PB3MFP_USCI1_DAT1        (0x08UL<<SYS_GPB_MFPL_PB3MFP_Pos)  /*!< USCI1 data1 pin. \hideinitializer */
#define SYS_GPB_MFPL_PB3MFP_SC0_RST           (0x09UL<<SYS_GPB_MFPL_PB3MFP_Pos)  /*!< SmartCard0 reset pin. \hideinitializer */
#define SYS_GPB_MFPL_PB3MFP_I2S0_DI           (0x0AUL<<SYS_GPB_MFPL_PB3MFP_Pos)  /*!< I2S0 data input. \hideinitializer */
#define SYS_GPB_MFPL_PB3MFP_EPWM0_CH2         (0x0BUL<<SYS_GPB_MFPL_PB3MFP_Pos)  /*!< EPWM0 channel2 output/capture input. \hideinitializer */
#define SYS_GPB_MFPL_PB3MFP_I2C1_SCL          (0x0CUL<<SYS_GPB_MFPL_PB3MFP_Pos)  /*!< I2C1 clock pin. */
#define SYS_GPB_MFPL_PB3MFP_TM2               (0x0EUL<<SYS_GPB_MFPL_PB3MFP_Pos)  /*!< Timer2 event counter input / toggle output  \hideinitializer */
#define SYS_GPB_MFPL_PB3MFP_INT2              (0x0FUL<<SYS_GPB_MFPL_PB3MFP_Pos)  /*!< External interrupt2 input pin. \hideinitializer */
#define SYS_GPB_MFPL_PB4MFP_GPIO              (0x00UL<<SYS_GPB_MFPL_PB4MFP_Pos)  /*!< General purpose digital I/O pin. \hideinitializer */
#define SYS_GPB_MFPL_PB4MFP_ACMP1_P1          (0x01UL<<SYS_GPB_MFPL_PB4MFP_Pos)  /*!< Analog comparator1 positive input pin. \hideinitializer */
#define SYS_GPB_MFPL_PB4MFP_EADC0_CH4         (0x01UL<<SYS_GPB_MFPL_PB4MFP_Pos)  /*!< EADC0 channel4 analog input. \hideinitializer */
#define SYS_GPB_MFPL_PB4MFP_EBI_ADR1          (0x02UL<<SYS_GPB_MFPL_PB4MFP_Pos)  /*!< EBI address/data bus bit*. \hideinitializer */
#define SYS_GPB_MFPL_PB4MFP_SD0_DAT2          (0x03UL<<SYS_GPB_MFPL_PB4MFP_Pos)  /*!< SD/SDIO 0 data line bit 2. \hideinitializer */
#define SYS_GPB_MFPL_PB4MFP_EMAC_RMII_RXD0    (0x04UL<<SYS_GPB_MFPL_PB4MFP_Pos)  /*!< RMII Receive Data bus bit 0. \hideinitializer */
#define SYS_GPB_MFPL_PB4MFP_SPI1_MOSI         (0x05UL<<SYS_GPB_MFPL_PB4MFP_Pos)  /*!< 1st SPI1 MOSI (Master Out, Slave In) pin. \hideinitializer */
#define SYS_GPB_MFPL_PB4MFP_I2C0_SDA          (0x06UL<<SYS_GPB_MFPL_PB4MFP_Pos)  /*!< I2C0 data input/output pin. \hideinitializer */
#define SYS_GPB_MFPL_PB4MFP_UART5_RXD         (0x07UL<<SYS_GPB_MFPL_PB4MFP_Pos)  /*!< Data receiver input pin for UART5. \hideinitializer */
#define SYS_GPB_MFPL_PB4MFP_USCI1_CTL1        (0x08UL<<SYS_GPB_MFPL_PB4MFP_Pos)  /*!< USCI1 control1 pin. \hideinitializer */
#define SYS_GPB_MFPL_PB4MFP_SC0_DAT           (0x09UL<<SYS_GPB_MFPL_PB4MFP_Pos)  /*!< SmartCard0 data pin. \hideinitializer */
#define SYS_GPB_MFPL_PB4MFP_I2S0_MCLK         (0x0AUL<<SYS_GPB_MFPL_PB4MFP_Pos)  /*!< I2S0 master clock output pin. \hideinitializer */
#define SYS_GPB_MFPL_PB4MFP_EPWM0_CH1         (0x0BUL<<SYS_GPB_MFPL_PB4MFP_Pos)  /*!< EPWM0 channel1 output/capture input. \hideinitializer */
#define SYS_GPB_MFPL_PB4MFP_UART2_RXD         (0x0CUL<<SYS_GPB_MFPL_PB4MFP_Pos)  /*!< Data receiver input pin for UART2. \hideinitializer */
#define SYS_GPB_MFPL_PB4MFP_TM1               (0x0EUL<<SYS_GPB_MFPL_PB4MFP_Pos)  /*!< Timer1 event counter input / toggle output  \hideinitializer */
#define SYS_GPB_MFPL_PB4MFP_INT1              (0x0FUL<<SYS_GPB_MFPL_PB4MFP_Pos)  /*!< External interrupt1 input pin. \hideinitializer */
#define SYS_GPB_MFPL_PB5MFP_GPIO              (0x00UL<<SYS_GPB_MFPL_PB5MFP_Pos)  /*!< General purpose digital I/O pin. \hideinitializer */
#define SYS_GPB_MFPL_PB5MFP_ACMP1_N           (0x01UL<<SYS_GPB_MFPL_PB5MFP_Pos)  /*!< Analog comparator1 negative input pin. \hideinitializer */
#define SYS_GPB_MFPL_PB5MFP_EADC0_CH5         (0x01UL<<SYS_GPB_MFPL_PB5MFP_Pos)  /*!< EADC0 channel5 analog input. \hideinitializer */
#define SYS_GPB_MFPL_PB5MFP_EBI_ADR0          (0x02UL<<SYS_GPB_MFPL_PB5MFP_Pos)  /*!< EBI address/data bus bit*. \hideinitializer */
#define SYS_GPB_MFPL_PB5MFP_SD0_DAT3          (0x03UL<<SYS_GPB_MFPL_PB5MFP_Pos)  /*!< SD/SDIO 0 data line bit 3. \hideinitializer */
#define SYS_GPB_MFPL_PB5MFP_EMAC_RMII_REFCLK  (0x04UL<<SYS_GPB_MFPL_PB5MFP_Pos)  /*!< EMAC mode clock input. \hideinitializer */
#define SYS_GPB_MFPL_PB5MFP_SPI1_MISO         (0x05UL<<SYS_GPB_MFPL_PB5MFP_Pos)  /*!< 1st SPI1 MISO (Master In, Slave Out) pin. \hideinitializer */
#define SYS_GPB_MFPL_PB5MFP_I2C0_SCL          (0x06UL<<SYS_GPB_MFPL_PB5MFP_Pos)  /*!< I2C0 clock pin. \hideinitializer */
#define SYS_GPB_MFPL_PB5MFP_UART5_TXD         (0x07UL<<SYS_GPB_MFPL_PB5MFP_Pos)  /*!< Data transmitter output pin for UART5. \hideinitializer */
#define SYS_GPB_MFPL_PB5MFP_USCI1_CTL0        (0x08UL<<SYS_GPB_MFPL_PB5MFP_Pos)  /*!< USCI1 control0 pin. \hideinitializer */
#define SYS_GPB_MFPL_PB5MFP_SC0_CLK           (0x09UL<<SYS_GPB_MFPL_PB5MFP_Pos)  /*!< SmartCard0 clock pin. \hideinitializer */
#define SYS_GPB_MFPL_PB5MFP_I2S0_BCLK         (0x0AUL<<SYS_GPB_MFPL_PB5MFP_Pos)  /*!< I2S0 bit clock pin. \hideinitializer */
#define SYS_GPB_MFPL_PB5MFP_EPWM0_CH0         (0x0BUL<<SYS_GPB_MFPL_PB5MFP_Pos)  /*!< EPWM0 channel0 output/capture input. \hideinitializer */
#define SYS_GPB_MFPL_PB5MFP_UART2_TXD         (0x0CUL<<SYS_GPB_MFPL_PB5MFP_Pos)  /*!< Data transmitter output pin for UART2. \hideinitializer */
#define SYS_GPB_MFPL_PB5MFP_TM0               (0x0EUL<<SYS_GPB_MFPL_PB5MFP_Pos)  /*!< Timer0 event counter input / toggle output  \hideinitializer */
#define SYS_GPB_MFPL_PB5MFP_INT0              (0x0FUL<<SYS_GPB_MFPL_PB5MFP_Pos)  /*!< External interrupt0 input pin. \hideinitializer */
#define SYS_GPB_MFPL_PB6MFP_GPIO              (0x00UL<<SYS_GPB_MFPL_PB6MFP_Pos)  /*!< General purpose digital I/O pin. \hideinitializer */
#define SYS_GPB_MFPL_PB6MFP_EADC0_CH6         (0x01UL<<SYS_GPB_MFPL_PB6MFP_Pos)  /*!< EADC0 channel6 analog input. \hideinitializer */
#define SYS_GPB_MFPL_PB6MFP_EBI_nWRH          (0x02UL<<SYS_GPB_MFPL_PB6MFP_Pos)  /*!< EBI write enable output pin. \hideinitializer */
#define SYS_GPB_MFPL_PB6MFP_EMAC_PPS          (0x03UL<<SYS_GPB_MFPL_PB6MFP_Pos)  /*!< EMAC Pulse Per Second output  \hideinitializer */
#define SYS_GPB_MFPL_PB6MFP_USCI1_DAT1        (0x04UL<<SYS_GPB_MFPL_PB6MFP_Pos)  /*!< USCI1 data1 pin. \hideinitializer */
#define SYS_GPB_MFPL_PB6MFP_CAN1_RXD          (0x05UL<<SYS_GPB_MFPL_PB6MFP_Pos)  /*!< CAN1 bus receiver input. \hideinitializer */
#define SYS_GPB_MFPL_PB6MFP_UART1_RXD         (0x06UL<<SYS_GPB_MFPL_PB6MFP_Pos)  /*!< Data receiver input pin for UART1. \hideinitializer */
#define SYS_GPB_MFPL_PB6MFP_SD1_CLK           (0x07UL<<SYS_GPB_MFPL_PB6MFP_Pos)  /*!< SD/SDIO 1 clock. \hideinitializer */
#define SYS_GPB_MFPL_PB6MFP_EBI_nCS1          (0x08UL<<SYS_GPB_MFPL_PB6MFP_Pos)  /*!< EBI chip select enable output pin. \hideinitializer */
#define SYS_GPB_MFPL_PB6MFP_BPWM1_CH5         (0x0AUL<<SYS_GPB_MFPL_PB6MFP_Pos)  /*!< BPWM1 channel5 output/capture input. \hideinitializer */
#define SYS_GPB_MFPL_PB6MFP_EPWM1_BRAKE1      (0x0BUL<<SYS_GPB_MFPL_PB6MFP_Pos)  /*!< Brake input pin 1 of EPWM1. \hideinitializer */
#define SYS_GPB_MFPL_PB6MFP_EPWM1_CH5         (0x0CUL<<SYS_GPB_MFPL_PB6MFP_Pos)  /*!< EPWM1 channel5 output/capture input. \hideinitializer */
#define SYS_GPB_MFPL_PB6MFP_INT4              (0x0DUL<<SYS_GPB_MFPL_PB6MFP_Pos)  /*!< External interrupt4 input pin. \hideinitializer */
#define SYS_GPB_MFPL_PB6MFP_USB_VBUS_EN       (0x0EUL<<SYS_GPB_MFPL_PB6MFP_Pos)  /*!< Power supply from USB Full speed host or HUB. \hideinitializer */
#define SYS_GPB_MFPL_PB6MFP_ACMP1_O           (0x0FUL<<SYS_GPB_MFPL_PB6MFP_Pos)  /*!< Analog comparator1 output. \hideinitializer */
#define SYS_GPB_MFPL_PB7MFP_GPIO              (0x00UL<<SYS_GPB_MFPL_PB7MFP_Pos)  /*!< General purpose digital I/O pin. \hideinitializer */
#define SYS_GPB_MFPL_PB7MFP_EADC0_CH7         (0x01UL<<SYS_GPB_MFPL_PB7MFP_Pos)  /*!< EADC0 channel7 analog input. \hideinitializer */
#define SYS_GPB_MFPL_PB7MFP_EBI_nWRL          (0x02UL<<SYS_GPB_MFPL_PB7MFP_Pos)  /*!< EBI write enable output pin. \hideinitializer */
#define SYS_GPB_MFPL_PB7MFP_EMAC_RMII_TXEN    (0x03UL<<SYS_GPB_MFPL_PB7MFP_Pos)  /*!< RMII Transmit Enable. \hideinitializer */
#define SYS_GPB_MFPL_PB7MFP_USCI1_DAT0        (0x04UL<<SYS_GPB_MFPL_PB7MFP_Pos)  /*!< USCI1 data0 pin. \hideinitializer */
#define SYS_GPB_MFPL_PB7MFP_CAN1_TXD          (0x05UL<<SYS_GPB_MFPL_PB7MFP_Pos)  /*!< CAN1 bus transmitter output. \hideinitializer */
#define SYS_GPB_MFPL_PB7MFP_UART1_TXD         (0x06UL<<SYS_GPB_MFPL_PB7MFP_Pos)  /*!< Data transmitter output pin for UART1. \hideinitializer */
#define SYS_GPB_MFPL_PB7MFP_SD1_CMD           (0x07UL<<SYS_GPB_MFPL_PB7MFP_Pos)  /*!< SD/SDIO 1 command/response. \hideinitializer */
#define SYS_GPB_MFPL_PB7MFP_EBI_nCS0          (0x08UL<<SYS_GPB_MFPL_PB7MFP_Pos)  /*!< EBI chip select enable output pin. \hideinitializer */
#define SYS_GPB_MFPL_PB7MFP_BPWM1_CH4         (0x0AUL<<SYS_GPB_MFPL_PB7MFP_Pos)  /*!< BPWM1 channel4 output/capture input. \hideinitializer */
#define SYS_GPB_MFPL_PB7MFP_EPWM1_BRAKE0      (0x0BUL<<SYS_GPB_MFPL_PB7MFP_Pos)  /*!< Brake input pin 0 of EPWM1. \hideinitializer */
#define SYS_GPB_MFPL_PB7MFP_EPWM1_CH4         (0x0CUL<<SYS_GPB_MFPL_PB7MFP_Pos)  /*!< EPWM1 channel4 output/capture input. \hideinitializer */
#define SYS_GPB_MFPL_PB7MFP_INT5              (0x0DUL<<SYS_GPB_MFPL_PB7MFP_Pos)  /*!< External interrupt5 input pin. \hideinitializer */
#define SYS_GPB_MFPL_PB7MFP_USB_VBUS_ST       (0x0EUL<<SYS_GPB_MFPL_PB7MFP_Pos)  /*!< Power supply from USB Full speed host or HUB. \hideinitializer */
#define SYS_GPB_MFPL_PB7MFP_ACMP0_O           (0x0FUL<<SYS_GPB_MFPL_PB7MFP_Pos)  /*!< Analog comparator0 output. \hideinitializer */
/********************* Bit definition of GPB_MFPH register **********************/
#define SYS_GPB_MFPH_PB8MFP_GPIO              (0x00UL<<SYS_GPB_MFPH_PB8MFP_Pos)  /*!< General purpose digital I/O pin. \hideinitializer */
#define SYS_GPB_MFPH_PB8MFP_EADC0_CH8         (0x01UL<<SYS_GPB_MFPH_PB8MFP_Pos)  /*!< EADC0 channel8 analog input. \hideinitializer */
#define SYS_GPB_MFPH_PB8MFP_EBI_ADR19         (0x02UL<<SYS_GPB_MFPH_PB8MFP_Pos)  /*!< EBI address/data bus bit*. \hideinitializer */
#define SYS_GPB_MFPH_PB8MFP_EMAC_RMII_TXD1    (0x03UL<<SYS_GPB_MFPH_PB8MFP_Pos)  /*!< RMII Transmit Data bus bit 1. \hideinitializer */
#define SYS_GPB_MFPH_PB8MFP_USCI1_CLK         (0x04UL<<SYS_GPB_MFPH_PB8MFP_Pos)  /*!< USCI1 clock pin. \hideinitializer */
#define SYS_GPB_MFPH_PB8MFP_UART0_RXD         (0x05UL<<SYS_GPB_MFPH_PB8MFP_Pos)  /*!< Data receiver input pin for UART0. \hideinitializer */
#define SYS_GPB_MFPH_PB8MFP_UART1_nRTS        (0x06UL<<SYS_GPB_MFPH_PB8MFP_Pos)  /*!< Request to Send output pin for UART1. \hideinitializer */
#define SYS_GPB_MFPH_PB8MFP_I2C1_SMBSUS       (0x07UL<<SYS_GPB_MFPH_PB8MFP_Pos)  /*!< I2C1 SMBus SMBSUS# pin (PMBus CONTROL pin) \hideinitializer */
#define SYS_GPB_MFPH_PB8MFP_UART7_RXD         (0x08UL<<SYS_GPB_MFPH_PB8MFP_Pos)  /*!< Data receiver input pin for UART7.  \hideinitializer */
#define SYS_GPB_MFPH_PB8MFP_I2C0_SDA          (0x09UL<<SYS_GPB_MFPH_PB8MFP_Pos)  /*!< I2C0 data input/output pin.  \hideinitializer */
#define SYS_GPB_MFPH_PB8MFP_BPWM1_CH3         (0x0AUL<<SYS_GPB_MFPH_PB8MFP_Pos)  /*!< BPWM1 channel3 output/capture input. \hideinitializer */
#define SYS_GPB_MFPH_PB8MFP_SPI3_MOSI         (0x0BUL<<SYS_GPB_MFPH_PB8MFP_Pos)  /*!< 1st SPI3 MOSI (Master Out, Slave In) pin. \hideinitializer */
#define SYS_GPB_MFPH_PB8MFP_CAN2_RXD          (0x0CUL<<SYS_GPB_MFPH_PB8MFP_Pos)  /*!< CAN2 bus receiver input. \hideinitializer */
#define SYS_GPB_MFPH_PB8MFP_INT6              (0x0DUL<<SYS_GPB_MFPH_PB8MFP_Pos)  /*!< External interrupt6 input pin. \hideinitializer */
#define SYS_GPB_MFPH_PB9MFP_GPIO              (0x00UL<<SYS_GPB_MFPH_PB9MFP_Pos)  /*!< General purpose digital I/O pin. \hideinitializer */
#define SYS_GPB_MFPH_PB9MFP_EADC0_CH9         (0x01UL<<SYS_GPB_MFPH_PB9MFP_Pos)  /*!< EADC0 channel9 analog input. \hideinitializer */
#define SYS_GPB_MFPH_PB9MFP_EBI_ADR18         (0x02UL<<SYS_GPB_MFPH_PB9MFP_Pos)  /*!< EBI address/data bus bit*. \hideinitializer */
#define SYS_GPB_MFPH_PB9MFP_EMAC_RMII_TXD0    (0x03UL<<SYS_GPB_MFPH_PB9MFP_Pos)  /*!< RMII Transmit Data bus bit 0. \hideinitializer */
#define SYS_GPB_MFPH_PB9MFP_USCI1_CTL1        (0x04UL<<SYS_GPB_MFPH_PB9MFP_Pos)  /*!< USCI1 control1 pin. \hideinitializer */
#define SYS_GPB_MFPH_PB9MFP_UART0_TXD         (0x05UL<<SYS_GPB_MFPH_PB9MFP_Pos)  /*!< Data transmitter output pin for UART0. \hideinitializer */
#define SYS_GPB_MFPH_PB9MFP_UART1_nCTS        (0x06UL<<SYS_GPB_MFPH_PB9MFP_Pos)  /*!< Clear to Send input pin for UART1. \hideinitializer */
#define SYS_GPB_MFPH_PB9MFP_I2C1_SMBAL        (0x07UL<<SYS_GPB_MFPH_PB9MFP_Pos)  /*!< I2C1 SMBus SMBALTER# pin  \hideinitializer */
#define SYS_GPB_MFPH_PB9MFP_UART7_TXD         (0x08UL<<SYS_GPB_MFPH_PB9MFP_Pos)  /*!< Data transmitter output pin for UART7. \hideinitializer */
#define SYS_GPB_MFPH_PB9MFP_I2C0_SCL          (0x09UL<<SYS_GPB_MFPH_PB9MFP_Pos)  /*!< I2C0 clock pin. \hideinitializer */
#define SYS_GPB_MFPH_PB9MFP_BPWM1_CH2         (0x0AUL<<SYS_GPB_MFPH_PB9MFP_Pos)  /*!< BPWM1 channel2 output/capture input. \hideinitializer */
#define SYS_GPB_MFPH_PB9MFP_SPI3_MISO         (0x0BUL<<SYS_GPB_MFPH_PB9MFP_Pos)  /*!< 1st SPI3 MISO (Master In, Slave Out) pin. \hideinitializer */
#define SYS_GPB_MFPH_PB9MFP_CAN2_TXD          (0x0CUL<<SYS_GPB_MFPH_PB9MFP_Pos)  /*!< CAN2 bus transmitter output. \hideinitializer */
#define SYS_GPB_MFPH_PB9MFP_INT7              (0x0DUL<<SYS_GPB_MFPH_PB9MFP_Pos)  /*!< External interrupt7 input pin. \hideinitializer */
#define SYS_GPB_MFPH_PB9MFP_CCAP_HSYNC        (0x0EUL<<SYS_GPB_MFPH_PB9MFP_Pos)  /*!< Sensor horizontal synchronization input pin. \hideinitializer */
#define SYS_GPB_MFPH_PB10MFP_GPIO             (0x00UL<<SYS_GPB_MFPH_PB10MFP_Pos) /*!< General purpose digital I/O pin. \hideinitializer */
#define SYS_GPB_MFPH_PB10MFP_EADC0_CH10       (0x01UL<<SYS_GPB_MFPH_PB10MFP_Pos) /*!< EADC0 channel1 analog input. \hideinitializer */
#define SYS_GPB_MFPH_PB10MFP_EBI_ADR17        (0x02UL<<SYS_GPB_MFPH_PB10MFP_Pos) /*!< EBI address/data bus bit*. \hideinitializer */
#define SYS_GPB_MFPH_PB10MFP_EMAC_RMII_MDIO   (0x03UL<<SYS_GPB_MFPH_PB10MFP_Pos) /*!< RMII Management Data I/O. \hideinitializer */
#define SYS_GPB_MFPH_PB10MFP_USCI1_CTL0       (0x04UL<<SYS_GPB_MFPH_PB10MFP_Pos) /*!< USCI1 control0 pin. \hideinitializer */
#define SYS_GPB_MFPH_PB10MFP_UART0_nRTS       (0x05UL<<SYS_GPB_MFPH_PB10MFP_Pos) /*!< Request to Send output pin for UART0. \hideinitializer */
#define SYS_GPB_MFPH_PB10MFP_UART4_RXD        (0x06UL<<SYS_GPB_MFPH_PB10MFP_Pos) /*!< Data receiver input pin for UART4. \hideinitializer */
#define SYS_GPB_MFPH_PB10MFP_I2C1_SDA         (0x07UL<<SYS_GPB_MFPH_PB10MFP_Pos) /*!< I2C1 data input/output pin. \hideinitializer */
#define SYS_GPB_MFPH_PB10MFP_CAN0_RXD         (0x08UL<<SYS_GPB_MFPH_PB10MFP_Pos) /*!< CAN0 bus receiver input. \hideinitializer */
#define SYS_GPB_MFPH_PB10MFP_BPWM1_CH1        (0x0AUL<<SYS_GPB_MFPH_PB10MFP_Pos) /*!< BPWM1 channel1 output/capture input. \hideinitializer */
#define SYS_GPB_MFPH_PB10MFP_SPI3_SS          (0x0BUL<<SYS_GPB_MFPH_PB10MFP_Pos) /*!< 1st SPI3 slave select pin. \hideinitializer */
#define SYS_GPB_MFPH_PB10MFP_CCAP_VSYNC       (0x0CUL<<SYS_GPB_MFPH_PB10MFP_Pos) /*!< Sensor vertical synchronization input pin. \hideinitializer */
#define SYS_GPB_MFPH_PB10MFP_HSUSB_VBUS_EN    (0x0EUL<<SYS_GPB_MFPH_PB10MFP_Pos) /*!< Power supply from USB High speed host or HUB. \hideinitializer */
#define SYS_GPB_MFPH_PB11MFP_GPIO             (0x00UL<<SYS_GPB_MFPH_PB11MFP_Pos) /*!< General purpose digital I/O pin. \hideinitializer */
#define SYS_GPB_MFPH_PB11MFP_EADC0_CH11       (0x01UL<<SYS_GPB_MFPH_PB11MFP_Pos) /*!< EADC0 channel1 analog input. \hideinitializer */
#define SYS_GPB_MFPH_PB11MFP_EBI_ADR16        (0x02UL<<SYS_GPB_MFPH_PB11MFP_Pos) /*!< EBI address/data bus bit*. \hideinitializer */
#define SYS_GPB_MFPH_PB11MFP_EMAC_RMII_MDC    (0x03UL<<SYS_GPB_MFPH_PB11MFP_Pos) /*!< RMII Management Data Clock. \hideinitializer */
#define SYS_GPB_MFPH_PB11MFP_UART0_nCTS       (0x05UL<<SYS_GPB_MFPH_PB11MFP_Pos) /*!< Clear to Send input pin for UART0. \hideinitializer */
#define SYS_GPB_MFPH_PB11MFP_UART4_TXD        (0x06UL<<SYS_GPB_MFPH_PB11MFP_Pos) /*!< Data transmitter output pin for UART4. \hideinitializer */
#define SYS_GPB_MFPH_PB11MFP_I2C1_SCL         (0x07UL<<SYS_GPB_MFPH_PB11MFP_Pos) /*!< I2C1 clock pin. \hideinitializer */
#define SYS_GPB_MFPH_PB11MFP_CAN0_TXD         (0x08UL<<SYS_GPB_MFPH_PB11MFP_Pos) /*!< CAN0 bus transmitter output. \hideinitializer */
#define SYS_GPB_MFPH_PB11MFP_SPI0_I2SMCLK     (0x09UL<<SYS_GPB_MFPH_PB11MFP_Pos) /*!< SPI0 I2S master clock output pin. \hideinitializer */
#define SYS_GPB_MFPH_PB11MFP_BPWM1_CH0        (0x0AUL<<SYS_GPB_MFPH_PB11MFP_Pos) /*!< BPWM1 channel0 output/capture input. \hideinitializer */
#define SYS_GPB_MFPH_PB11MFP_SPI3_CLK         (0x0BUL<<SYS_GPB_MFPH_PB11MFP_Pos) /*!< SPI3 serial clock pin. \hideinitializer */
#define SYS_GPB_MFPH_PB11MFP_CCAP_SFIELD      (0x0CUL<<SYS_GPB_MFPH_PB11MFP_Pos) /*!< Even/Odd Field Flag input pin. \hideinitializer */
#define SYS_GPB_MFPH_PB11MFP_HSUSB_VBUS_ST    (0x0EUL<<SYS_GPB_MFPH_PB11MFP_Pos) /*!< Power supply from USB High speed host or HUB. \hideinitializer */
#define SYS_GPB_MFPH_PB12MFP_GPIO             (0x00UL<<SYS_GPB_MFPH_PB12MFP_Pos) /*!< General purpose digital I/O pin. \hideinitializer */
#define SYS_GPB_MFPH_PB12MFP_ACMP0_P2         (0x01UL<<SYS_GPB_MFPH_PB12MFP_Pos) /*!< Analog comparator0 positive input pin. \hideinitializer */
#define SYS_GPB_MFPH_PB12MFP_ACMP1_P2         (0x01UL<<SYS_GPB_MFPH_PB12MFP_Pos) /*!< Analog comparator1 positive input pin. \hideinitializer */
#define SYS_GPB_MFPH_PB12MFP_DAC0_OUT         (0x01UL<<SYS_GPB_MFPH_PB12MFP_Pos) /*!< DAC0 channel analog output. \hideinitializer */
#define SYS_GPB_MFPH_PB12MFP_EADC0_CH12       (0x01UL<<SYS_GPB_MFPH_PB12MFP_Pos) /*!< EADC0 channel1 analog input. \hideinitializer */
#define SYS_GPB_MFPH_PB12MFP_EADC1_CH12       (0x01UL<<SYS_GPB_MFPH_PB12MFP_Pos) /*!< EADC1 channel1 analog input. \hideinitializer */
#define SYS_GPB_MFPH_PB12MFP_EBI_AD15         (0x02UL<<SYS_GPB_MFPH_PB12MFP_Pos) /*!< EBI address/data bus bit1. \hideinitializer */
#define SYS_GPB_MFPH_PB12MFP_SC1_CLK          (0x03UL<<SYS_GPB_MFPH_PB12MFP_Pos) /*!< SmartCard1 clock pin. \hideinitializer */
#define SYS_GPB_MFPH_PB12MFP_SPI0_MOSI        (0x04UL<<SYS_GPB_MFPH_PB12MFP_Pos) /*!< 1st SPI0 MOSI (Master Out, Slave In) pin. \hideinitializer */
#define SYS_GPB_MFPH_PB12MFP_USCI0_CLK        (0x05UL<<SYS_GPB_MFPH_PB12MFP_Pos) /*!< USCI0 clock pin. \hideinitializer */
#define SYS_GPB_MFPH_PB12MFP_UART0_RXD        (0x06UL<<SYS_GPB_MFPH_PB12MFP_Pos) /*!< Data receiver input pin for UART0. \hideinitializer */
#define SYS_GPB_MFPH_PB12MFP_UART3_nCTS       (0x07UL<<SYS_GPB_MFPH_PB12MFP_Pos) /*!< Clear to Send input pin for UART3. \hideinitializer */
#define SYS_GPB_MFPH_PB12MFP_I2C2_SDA         (0x08UL<<SYS_GPB_MFPH_PB12MFP_Pos) /*!< I2C2 data input/output pin. \hideinitializer */
#define SYS_GPB_MFPH_PB12MFP_SD0_nCD          (0x09UL<<SYS_GPB_MFPH_PB12MFP_Pos) /*!< SD/SDIO 0 card detect. \hideinitializer */
#define SYS_GPB_MFPH_PB12MFP_CCAP_SCLK        (0x0AUL<<SYS_GPB_MFPH_PB12MFP_Pos) /*!< Sensor pixel clock(to sensor) output pin. \hideinitializer */
#define SYS_GPB_MFPH_PB12MFP_EPWM1_CH3        (0x0BUL<<SYS_GPB_MFPH_PB12MFP_Pos) /*!< EPWM1 channel3 output/capture input. \hideinitializer */
#define SYS_GPB_MFPH_PB12MFP_ETM_TRACE_DATA3  (0x0CUL<<SYS_GPB_MFPH_PB12MFP_Pos) /*!< ETM Rx input bus bit3. \hideinitializer */
#define SYS_GPB_MFPH_PB12MFP_TM3_EXT          (0x0DUL<<SYS_GPB_MFPH_PB12MFP_Pos) /*!< Timer3 event counter input / toggle output  \hideinitializer */
#define SYS_GPB_MFPH_PB13MFP_GPIO             (0x00UL<<SYS_GPB_MFPH_PB13MFP_Pos) /*!< General purpose digital I/O pin. \hideinitializer */
#define SYS_GPB_MFPH_PB13MFP_ACMP0_P3         (0x01UL<<SYS_GPB_MFPH_PB13MFP_Pos) /*!< Analog comparator0 positive input pin. \hideinitializer */
#define SYS_GPB_MFPH_PB13MFP_ACMP1_P3         (0x01UL<<SYS_GPB_MFPH_PB13MFP_Pos) /*!< Analog comparator1 positive input pin. \hideinitializer */
#define SYS_GPB_MFPH_PB13MFP_DAC1_OUT         (0x01UL<<SYS_GPB_MFPH_PB13MFP_Pos) /*!< DAC1 channel analog output. \hideinitializer */
#define SYS_GPB_MFPH_PB13MFP_EADC0_CH13       (0x01UL<<SYS_GPB_MFPH_PB13MFP_Pos) /*!< EADC0 channel1 analog input. \hideinitializer */
#define SYS_GPB_MFPH_PB13MFP_EADC1_CH13       (0x01UL<<SYS_GPB_MFPH_PB13MFP_Pos) /*!< EADC1 channel1 analog input. \hideinitializer */
#define SYS_GPB_MFPH_PB13MFP_EBI_AD14         (0x02UL<<SYS_GPB_MFPH_PB13MFP_Pos) /*!< EBI address/data bus bit1. \hideinitializer */
#define SYS_GPB_MFPH_PB13MFP_SC1_DAT          (0x03UL<<SYS_GPB_MFPH_PB13MFP_Pos) /*!< SmartCard1 data pin. \hideinitializer */
#define SYS_GPB_MFPH_PB13MFP_SPI0_MISO        (0x04UL<<SYS_GPB_MFPH_PB13MFP_Pos) /*!< 1st SPI0 MISO (Master In, Slave Out) pin. \hideinitializer */
#define SYS_GPB_MFPH_PB13MFP_USCI0_DAT0       (0x05UL<<SYS_GPB_MFPH_PB13MFP_Pos) /*!< USCI0 data0 pin. \hideinitializer */
#define SYS_GPB_MFPH_PB13MFP_UART0_TXD        (0x06UL<<SYS_GPB_MFPH_PB13MFP_Pos) /*!< Data transmitter output pin for UART0. \hideinitializer */
#define SYS_GPB_MFPH_PB13MFP_UART3_nRTS       (0x07UL<<SYS_GPB_MFPH_PB13MFP_Pos) /*!< Request to Send output pin for UART3. \hideinitializer */
#define SYS_GPB_MFPH_PB13MFP_I2C2_SCL         (0x08UL<<SYS_GPB_MFPH_PB13MFP_Pos) /*!< I2C2 clock pin. \hideinitializer */
#define SYS_GPB_MFPH_PB13MFP_CCAP_PIXCLK      (0x0AUL<<SYS_GPB_MFPH_PB13MFP_Pos) /*!< Sensor pixel clock(from sensor) input pin. \hideinitializer */
#define SYS_GPB_MFPH_PB13MFP_EPWM1_CH2        (0x0BUL<<SYS_GPB_MFPH_PB13MFP_Pos) /*!< EPWM1 channel2 output/capture input. \hideinitializer */
#define SYS_GPB_MFPH_PB13MFP_ETM_TRACE_DATA2  (0x0CUL<<SYS_GPB_MFPH_PB13MFP_Pos) /*!< ETM Rx input bus bit2. \hideinitializer */
#define SYS_GPB_MFPH_PB13MFP_TM2_EXT          (0x0DUL<<SYS_GPB_MFPH_PB13MFP_Pos) /*!< Timer2 event counter input / toggle output  \hideinitializer */
#define SYS_GPB_MFPH_PB14MFP_GPIO             (0x00UL<<SYS_GPB_MFPH_PB14MFP_Pos) /*!< General purpose digital I/O pin. \hideinitializer */
#define SYS_GPB_MFPH_PB14MFP_EADC0_CH14       (0x01UL<<SYS_GPB_MFPH_PB14MFP_Pos) /*!< EADC0 channel1 analog input. \hideinitializer */
#define SYS_GPB_MFPH_PB14MFP_EADC1_CH14       (0x01UL<<SYS_GPB_MFPH_PB14MFP_Pos) /*!< EADC1 channel1 analog input. \hideinitializer */
#define SYS_GPB_MFPH_PB14MFP_EBI_AD13         (0x02UL<<SYS_GPB_MFPH_PB14MFP_Pos) /*!< EBI address/data bus bit1. \hideinitializer */
#define SYS_GPB_MFPH_PB14MFP_SC1_RST          (0x03UL<<SYS_GPB_MFPH_PB14MFP_Pos) /*!< SmartCard1 reset pin. \hideinitializer */
#define SYS_GPB_MFPH_PB14MFP_SPI0_CLK         (0x04UL<<SYS_GPB_MFPH_PB14MFP_Pos) /*!< SPI0 serial clock pin. \hideinitializer */
#define SYS_GPB_MFPH_PB14MFP_USCI0_DAT1       (0x05UL<<SYS_GPB_MFPH_PB14MFP_Pos) /*!< USCI0 data1 pin. \hideinitializer */
#define SYS_GPB_MFPH_PB14MFP_UART0_nRTS       (0x06UL<<SYS_GPB_MFPH_PB14MFP_Pos) /*!< Request to Send output pin for UART0. \hideinitializer */
#define SYS_GPB_MFPH_PB14MFP_UART3_RXD        (0x07UL<<SYS_GPB_MFPH_PB14MFP_Pos) /*!< Data receiver input pin for UART3. \hideinitializer */
#define SYS_GPB_MFPH_PB14MFP_I2C2_SMBSUS      (0x08UL<<SYS_GPB_MFPH_PB14MFP_Pos) /*!< I2C2 SMBus SMBSUS# pin (PMBus CONTROL pin)  \hideinitializer */
#define SYS_GPB_MFPH_PB14MFP_EPWM1_CH1        (0x0BUL<<SYS_GPB_MFPH_PB14MFP_Pos) /*!< EPWM1 channel1 output/capture input. \hideinitializer */
#define SYS_GPB_MFPH_PB14MFP_ETM_TRACE_DATA1  (0x0CUL<<SYS_GPB_MFPH_PB14MFP_Pos) /*!< ETM Rx input bus bit1. \hideinitializer */
#define SYS_GPB_MFPH_PB14MFP_TM1_EXT          (0x0DUL<<SYS_GPB_MFPH_PB14MFP_Pos) /*!< Timer1 event counter input / toggle output  \hideinitializer */
#define SYS_GPB_MFPH_PB14MFP_CLKO             (0x0EUL<<SYS_GPB_MFPH_PB14MFP_Pos) /*!< Clock Output pin. \hideinitializer */
#define SYS_GPB_MFPH_PB14MFP_USB_VBUS_ST      (0x0FUL<<SYS_GPB_MFPH_PB14MFP_Pos) /*!< Power supply from USB Full speed host or HUB. */
#define SYS_GPB_MFPH_PB15MFP_GPIO             (0x00UL<<SYS_GPB_MFPH_PB15MFP_Pos) /*!< General purpose digital I/O pin. \hideinitializer */
#define SYS_GPB_MFPH_PB15MFP_EADC0_CH15       (0x01UL<<SYS_GPB_MFPH_PB15MFP_Pos) /*!< EADC0 channel1 analog input. \hideinitializer */
#define SYS_GPB_MFPH_PB15MFP_EADC1_CH15       (0x01UL<<SYS_GPB_MFPH_PB15MFP_Pos) /*!< EADC1 channel1 analog input. \hideinitializer */
#define SYS_GPB_MFPH_PB15MFP_EBI_AD12         (0x02UL<<SYS_GPB_MFPH_PB15MFP_Pos) /*!< EBI address/data bus bit1. \hideinitializer */
#define SYS_GPB_MFPH_PB15MFP_SC1_PWR          (0x03UL<<SYS_GPB_MFPH_PB15MFP_Pos) /*!< SmartCard1 power pin. \hideinitializer */
#define SYS_GPB_MFPH_PB15MFP_SPI0_SS          (0x04UL<<SYS_GPB_MFPH_PB15MFP_Pos) /*!< 1st SPI0 slave select pin. \hideinitializer */
#define SYS_GPB_MFPH_PB15MFP_USCI0_CTL1       (0x05UL<<SYS_GPB_MFPH_PB15MFP_Pos) /*!< USCI0 control1 pin. \hideinitializer */
#define SYS_GPB_MFPH_PB15MFP_UART0_nCTS       (0x06UL<<SYS_GPB_MFPH_PB15MFP_Pos) /*!< Clear to Send input pin for UART0. \hideinitializer */
#define SYS_GPB_MFPH_PB15MFP_UART3_TXD        (0x07UL<<SYS_GPB_MFPH_PB15MFP_Pos) /*!< Data transmitter output pin for UART3. \hideinitializer */
#define SYS_GPB_MFPH_PB15MFP_I2C2_SMBAL       (0x08UL<<SYS_GPB_MFPH_PB15MFP_Pos) /*!< I2C2 SMBus SMBALTER# pin.  \hideinitializer */
#define SYS_GPB_MFPH_PB15MFP_EPWM0_BRAKE1     (0x0AUL<<SYS_GPB_MFPH_PB15MFP_Pos) /*!< Brake input pin 1 of EPWM0. \hideinitializer */
#define SYS_GPB_MFPH_PB15MFP_EPWM1_CH0        (0x0BUL<<SYS_GPB_MFPH_PB15MFP_Pos) /*!< EPWM1 channel0 output/capture input. \hideinitializer */
#define SYS_GPB_MFPH_PB15MFP_ETM_TRACE_DATA0  (0x0CUL<<SYS_GPB_MFPH_PB15MFP_Pos) /*!< ETM Rx input bus bit0. \hideinitializer */
#define SYS_GPB_MFPH_PB15MFP_TM0_EXT          (0x0DUL<<SYS_GPB_MFPH_PB15MFP_Pos) /*!< Timer0 event counter input / toggle output  \hideinitializer */
#define SYS_GPB_MFPH_PB15MFP_USB_VBUS_EN      (0x0EUL<<SYS_GPB_MFPH_PB15MFP_Pos) /*!< Power supply from USB Full speed host or HUB. \hideinitializer */
#define SYS_GPB_MFPH_PB15MFP_HSUSB_VBUS_EN    (0x0FUL<<SYS_GPB_MFPH_PB15MFP_Pos) /*!< Power supply from USB High speed host or HUB. \hideinitializer */
/********************* Bit definition of GPC_MFPL register **********************/
#define SYS_GPC_MFPL_PC0MFP_GPIO              (0x00UL<<SYS_GPC_MFPL_PC0MFP_Pos)  /*!< General purpose digital I/O pin. \hideinitializer */
#define SYS_GPC_MFPL_PC0MFP_EBI_AD0           (0x02UL<<SYS_GPC_MFPL_PC0MFP_Pos)  /*!< EBI address/data bus bit0. \hideinitializer */
#define SYS_GPC_MFPL_PC0MFP_SPIM_MOSI         (0x03UL<<SYS_GPC_MFPL_PC0MFP_Pos)  /*!< 1st SPIM MOSI (Master Out, Slave In) pin. \hideinitializer */
#define SYS_GPC_MFPL_PC0MFP_QSPI0_MOSI0       (0x04UL<<SYS_GPC_MFPL_PC0MFP_Pos)  /*!< 1st QSPI0 MOSI (Master Out, Slave In) pin. \hideinitializer */
#define SYS_GPC_MFPL_PC0MFP_SC1_CLK           (0x05UL<<SYS_GPC_MFPL_PC0MFP_Pos)  /*!< SmartCard1 clock pin. \hideinitializer */
#define SYS_GPC_MFPL_PC0MFP_I2S0_LRCK         (0x06UL<<SYS_GPC_MFPL_PC0MFP_Pos)  /*!< I2S0 left right channel clock. \hideinitializer */
#define SYS_GPC_MFPL_PC0MFP_SPI1_SS           (0x07UL<<SYS_GPC_MFPL_PC0MFP_Pos)  /*!< 1st SPI1 slave select pin. \hideinitializer */
#define SYS_GPC_MFPL_PC0MFP_UART2_RXD         (0x08UL<<SYS_GPC_MFPL_PC0MFP_Pos)  /*!< Data receiver input pin for UART2. \hideinitializer */
#define SYS_GPC_MFPL_PC0MFP_I2C0_SDA          (0x09UL<<SYS_GPC_MFPL_PC0MFP_Pos)  /*!< I2C0 data input/output pin. \hideinitializer */
#define SYS_GPC_MFPL_PC0MFP_CAN2_RXD          (0x0AUL<<SYS_GPC_MFPL_PC0MFP_Pos)  /*!< CAN2 bus receiver input. \hideinitializer */
#define SYS_GPC_MFPL_PC0MFP_EPWM1_CH5         (0x0CUL<<SYS_GPC_MFPL_PC0MFP_Pos)  /*!< EPWM1 channel5 output/capture input. \hideinitializer */
#define SYS_GPC_MFPL_PC0MFP_CCAP_DATA0        (0x0DUL<<SYS_GPC_MFPL_PC0MFP_Pos)  /*!< Sensor pixel data0 input pin. \hideinitializer */
#define SYS_GPC_MFPL_PC0MFP_ACMP1_O           (0x0EUL<<SYS_GPC_MFPL_PC0MFP_Pos)  /*!< Analog comparator1 output. \hideinitializer */
#define SYS_GPC_MFPL_PC0MFP_EADC1_ST          (0x0FUL<<SYS_GPC_MFPL_PC0MFP_Pos)  /*!< EADC external trigger input. \hideinitializer */
#define SYS_GPC_MFPL_PC1MFP_GPIO              (0x00UL<<SYS_GPC_MFPL_PC1MFP_Pos)  /*!< General purpose digital I/O pin. \hideinitializer */
#define SYS_GPC_MFPL_PC1MFP_EBI_AD1           (0x02UL<<SYS_GPC_MFPL_PC1MFP_Pos)  /*!< EBI address/data bus bit1. \hideinitializer */
#define SYS_GPC_MFPL_PC1MFP_SPIM_MISO         (0x03UL<<SYS_GPC_MFPL_PC1MFP_Pos)  /*!< 1st SPIM MISO (Master In, Slave Out) pin. \hideinitializer */
#define SYS_GPC_MFPL_PC1MFP_QSPI0_MISO0       (0x04UL<<SYS_GPC_MFPL_PC1MFP_Pos)  /*!< 1st QSPI0 MISO (Master In, Slave Out) pin. \hideinitializer */
#define SYS_GPC_MFPL_PC1MFP_SC1_DAT           (0x05UL<<SYS_GPC_MFPL_PC1MFP_Pos)  /*!< SmartCard1 data pin. \hideinitializer */
#define SYS_GPC_MFPL_PC1MFP_I2S0_DO           (0x06UL<<SYS_GPC_MFPL_PC1MFP_Pos)  /*!< I2S0 data output. \hideinitializer */
#define SYS_GPC_MFPL_PC1MFP_SPI1_CLK          (0x07UL<<SYS_GPC_MFPL_PC1MFP_Pos)  /*!< SPI1 serial clock pin. \hideinitializer */
#define SYS_GPC_MFPL_PC1MFP_UART2_TXD         (0x08UL<<SYS_GPC_MFPL_PC1MFP_Pos)  /*!< Data transmitter output pin for UART2. \hideinitializer */
#define SYS_GPC_MFPL_PC1MFP_I2C0_SCL          (0x09UL<<SYS_GPC_MFPL_PC1MFP_Pos)  /*!< I2C0 clock pin. \hideinitializer */
#define SYS_GPC_MFPL_PC1MFP_CAN2_TXD          (0x0AUL<<SYS_GPC_MFPL_PC1MFP_Pos)  /*!< CAN2 bus transmitter output. \hideinitializer */
#define SYS_GPC_MFPL_PC1MFP_EPWM1_CH4         (0x0CUL<<SYS_GPC_MFPL_PC1MFP_Pos)  /*!< EPWM1 channel4 output/capture input. \hideinitializer */
#define SYS_GPC_MFPL_PC1MFP_CCAP_DATA1        (0x0DUL<<SYS_GPC_MFPL_PC1MFP_Pos)  /*!< Sensor pixel data1 input pin. \hideinitializer */
#define SYS_GPC_MFPL_PC1MFP_ACMP0_O           (0x0EUL<<SYS_GPC_MFPL_PC1MFP_Pos)  /*!< Analog comparator0 output. \hideinitializer */
#define SYS_GPC_MFPL_PC1MFP_EADC0_ST          (0x0FUL<<SYS_GPC_MFPL_PC1MFP_Pos)  /*!< EADC external trigger input. \hideinitializer */
#define SYS_GPC_MFPL_PC2MFP_GPIO              (0x00UL<<SYS_GPC_MFPL_PC2MFP_Pos)  /*!< General purpose digital I/O pin. \hideinitializer */
#define SYS_GPC_MFPL_PC2MFP_EBI_AD2           (0x02UL<<SYS_GPC_MFPL_PC2MFP_Pos)  /*!< EBI address/data bus bit2. \hideinitializer */
#define SYS_GPC_MFPL_PC2MFP_SPIM_CLK          (0x03UL<<SYS_GPC_MFPL_PC2MFP_Pos)  /*!< SPIM serial clock pin. \hideinitializer */
#define SYS_GPC_MFPL_PC2MFP_QSPI0_CLK         (0x04UL<<SYS_GPC_MFPL_PC2MFP_Pos)  /*!< QSPI0 serial clock pin. \hideinitializer */
#define SYS_GPC_MFPL_PC2MFP_SC1_RST           (0x05UL<<SYS_GPC_MFPL_PC2MFP_Pos)  /*!< SmartCard1 reset pin. \hideinitializer */
#define SYS_GPC_MFPL_PC2MFP_I2S0_DI           (0x06UL<<SYS_GPC_MFPL_PC2MFP_Pos)  /*!< I2S0 data input. \hideinitializer */
#define SYS_GPC_MFPL_PC2MFP_SPI1_MOSI         (0x07UL<<SYS_GPC_MFPL_PC2MFP_Pos)  /*!< 1st SPI1 MOSI (Master Out, Slave In) pin. \hideinitializer */
#define SYS_GPC_MFPL_PC2MFP_UART2_nCTS        (0x08UL<<SYS_GPC_MFPL_PC2MFP_Pos)  /*!< Clear to Send input pin for UART2. \hideinitializer */
#define SYS_GPC_MFPL_PC2MFP_I2C0_SMBSUS       (0x09UL<<SYS_GPC_MFPL_PC2MFP_Pos)  /*!< I2C0 SMBus SMBSUS# pin (PMBus CONTROL pin)  \hideinitializer */
#define SYS_GPC_MFPL_PC2MFP_CAN1_RXD          (0x0AUL<<SYS_GPC_MFPL_PC2MFP_Pos)  /*!< CAN1 bus receiver input. \hideinitializer */
#define SYS_GPC_MFPL_PC2MFP_UART3_RXD         (0x0BUL<<SYS_GPC_MFPL_PC2MFP_Pos)  /*!< Data receiver input pin for UART3. \hideinitializer */
#define SYS_GPC_MFPL_PC2MFP_EPWM1_CH3         (0x0CUL<<SYS_GPC_MFPL_PC2MFP_Pos)  /*!< EPWM1 channel3 output/capture input. \hideinitializer */
#define SYS_GPC_MFPL_PC2MFP_CCAP_DATA2        (0x0DUL<<SYS_GPC_MFPL_PC2MFP_Pos)  /*!< Sensor pixel data2 input pin. \hideinitializer */
#define SYS_GPC_MFPL_PC2MFP_QSPI1_MOSI0       (0x0EUL<<SYS_GPC_MFPL_PC2MFP_Pos)  /*!< 1st QSPI1 MOSI (Master Out, Slave In) pin. \hideinitializer */
#define SYS_GPC_MFPL_PC3MFP_GPIO              (0x00UL<<SYS_GPC_MFPL_PC3MFP_Pos)  /*!< General purpose digital I/O pin. \hideinitializer */
#define SYS_GPC_MFPL_PC3MFP_EBI_AD3           (0x02UL<<SYS_GPC_MFPL_PC3MFP_Pos)  /*!< EBI address/data bus bit3. \hideinitializer */
#define SYS_GPC_MFPL_PC3MFP_SPIM_SS           (0x03UL<<SYS_GPC_MFPL_PC3MFP_Pos)  /*!< 1st SPIM slave select pin. \hideinitializer */
#define SYS_GPC_MFPL_PC3MFP_QSPI0_SS          (0x04UL<<SYS_GPC_MFPL_PC3MFP_Pos)  /*!< 1st QSPI0 slave select pin. \hideinitializer */
#define SYS_GPC_MFPL_PC3MFP_SC1_PWR           (0x05UL<<SYS_GPC_MFPL_PC3MFP_Pos)  /*!< SmartCard1 power pin. \hideinitializer */
#define SYS_GPC_MFPL_PC3MFP_I2S0_MCLK         (0x06UL<<SYS_GPC_MFPL_PC3MFP_Pos)  /*!< I2S0 master clock output pin. \hideinitializer */
#define SYS_GPC_MFPL_PC3MFP_SPI1_MISO         (0x07UL<<SYS_GPC_MFPL_PC3MFP_Pos)  /*!< 1st SPI1 MISO (Master In, Slave Out) pin. \hideinitializer */
#define SYS_GPC_MFPL_PC3MFP_UART2_nRTS        (0x08UL<<SYS_GPC_MFPL_PC3MFP_Pos)  /*!< Request to Send output pin for UART2. \hideinitializer */
#define SYS_GPC_MFPL_PC3MFP_I2C0_SMBAL        (0x09UL<<SYS_GPC_MFPL_PC3MFP_Pos)  /*!< I2C0 SMBus SMBALTER# pin  \hideinitializer  */
#define SYS_GPC_MFPL_PC3MFP_CAN1_TXD          (0x0AUL<<SYS_GPC_MFPL_PC3MFP_Pos)  /*!< CAN1 bus transmitter output. \hideinitializer */
#define SYS_GPC_MFPL_PC3MFP_UART3_TXD         (0x0BUL<<SYS_GPC_MFPL_PC3MFP_Pos)  /*!< Data transmitter output pin for UART3. \hideinitializer */
#define SYS_GPC_MFPL_PC3MFP_EPWM1_CH2         (0x0CUL<<SYS_GPC_MFPL_PC3MFP_Pos)  /*!< EPWM1 channel2 output/capture input. \hideinitializer */
#define SYS_GPC_MFPL_PC3MFP_CCAP_DATA3        (0x0DUL<<SYS_GPC_MFPL_PC3MFP_Pos)  /*!< Sensor pixel data3 input pin. \hideinitializer */
#define SYS_GPC_MFPL_PC3MFP_QSPI1_MISO0       (0x0EUL<<SYS_GPC_MFPL_PC3MFP_Pos)  /*!< 1st QSPI1 MISO (Master In, Slave Out) pin. \hideinitializer */
#define SYS_GPC_MFPL_PC4MFP_GPIO              (0x00UL<<SYS_GPC_MFPL_PC4MFP_Pos)  /*!< General purpose digital I/O pin. \hideinitializer */
#define SYS_GPC_MFPL_PC4MFP_EBI_AD4           (0x02UL<<SYS_GPC_MFPL_PC4MFP_Pos)  /*!< EBI address/data bus bit4. \hideinitializer */
#define SYS_GPC_MFPL_PC4MFP_SPIM_D3           (0x03UL<<SYS_GPC_MFPL_PC4MFP_Pos)  /*!< SPIM data 3 pin for Quad Mode I/O. \hideinitializer */
#define SYS_GPC_MFPL_PC4MFP_QSPI0_MOSI1       (0x04UL<<SYS_GPC_MFPL_PC4MFP_Pos)  /*!< 2nd QSPI0 MOSI (Master Out, Slave In) pin. \hideinitializer */
#define SYS_GPC_MFPL_PC4MFP_SC1_nCD           (0x05UL<<SYS_GPC_MFPL_PC4MFP_Pos)  /*!< SmartCard1 card detect pin. \hideinitializer */
#define SYS_GPC_MFPL_PC4MFP_I2S0_BCLK         (0x06UL<<SYS_GPC_MFPL_PC4MFP_Pos)  /*!< I2S0 bit clock pin. \hideinitializer */
#define SYS_GPC_MFPL_PC4MFP_SPI1_I2SMCLK      (0x07UL<<SYS_GPC_MFPL_PC4MFP_Pos)  /*!< SPI1 I2S master clock output pin. \hideinitializer */
#define SYS_GPC_MFPL_PC4MFP_UART2_RXD         (0x08UL<<SYS_GPC_MFPL_PC4MFP_Pos)  /*!< Data receiver input pin for UART2. \hideinitializer */
#define SYS_GPC_MFPL_PC4MFP_I2C1_SDA          (0x09UL<<SYS_GPC_MFPL_PC4MFP_Pos)  /*!< I2C1 data input/output pin. \hideinitializer */
#define SYS_GPC_MFPL_PC4MFP_CAN0_RXD          (0x0AUL<<SYS_GPC_MFPL_PC4MFP_Pos)  /*!< CAN0 bus receiver input. \hideinitializer */
#define SYS_GPC_MFPL_PC4MFP_UART4_RXD         (0x0BUL<<SYS_GPC_MFPL_PC4MFP_Pos)  /*!< Data receiver input pin for UART4. \hideinitializer */
#define SYS_GPC_MFPL_PC4MFP_EPWM1_CH1         (0x0CUL<<SYS_GPC_MFPL_PC4MFP_Pos)  /*!< EPWM1 channel1 output/capture input. \hideinitializer */
#define SYS_GPC_MFPL_PC4MFP_CCAP_DATA4        (0x0DUL<<SYS_GPC_MFPL_PC4MFP_Pos)  /*!< Sensor pixel data4 input pin. \hideinitializer */
#define SYS_GPC_MFPL_PC4MFP_QSPI1_CLK         (0x0EUL<<SYS_GPC_MFPL_PC4MFP_Pos)  /*!< QSPI1 serial clock pin. \hideinitializer */
#define SYS_GPC_MFPL_PC5MFP_GPIO              (0x00UL<<SYS_GPC_MFPL_PC5MFP_Pos)  /*!< General purpose digital I/O pin. \hideinitializer */
#define SYS_GPC_MFPL_PC5MFP_EBI_AD5           (0x02UL<<SYS_GPC_MFPL_PC5MFP_Pos)  /*!< EBI address/data bus bit5. \hideinitializer */
#define SYS_GPC_MFPL_PC5MFP_SPIM_D2           (0x03UL<<SYS_GPC_MFPL_PC5MFP_Pos)  /*!< SPIM data 2 pin for Quad Mode I/O. \hideinitializer */
#define SYS_GPC_MFPL_PC5MFP_QSPI0_MISO1       (0x04UL<<SYS_GPC_MFPL_PC5MFP_Pos)  /*!< 2nd QSPI0 MISO (Master In, Slave Out) pin. \hideinitializer */
#define SYS_GPC_MFPL_PC5MFP_UART2_TXD         (0x08UL<<SYS_GPC_MFPL_PC5MFP_Pos)  /*!< Data transmitter output pin for UART2. \hideinitializer */
#define SYS_GPC_MFPL_PC5MFP_I2C1_SCL          (0x09UL<<SYS_GPC_MFPL_PC5MFP_Pos)  /*!< I2C1 clock pin. \hideinitializer */
#define SYS_GPC_MFPL_PC5MFP_CAN0_TXD          (0x0AUL<<SYS_GPC_MFPL_PC5MFP_Pos)  /*!< CAN0 bus transmitter output. \hideinitializer */
#define SYS_GPC_MFPL_PC5MFP_UART4_TXD         (0x0BUL<<SYS_GPC_MFPL_PC5MFP_Pos)  /*!< Data transmitter output pin for UART4. \hideinitializer */
#define SYS_GPC_MFPL_PC5MFP_EPWM1_CH0         (0x0CUL<<SYS_GPC_MFPL_PC5MFP_Pos)  /*!< EPWM1 channel0 output/capture input. \hideinitializer */
#define SYS_GPC_MFPL_PC5MFP_CCAP_DATA5        (0x0DUL<<SYS_GPC_MFPL_PC5MFP_Pos)  /*!< Sensor pixel data5 input pin. \hideinitializer */
#define SYS_GPC_MFPL_PC5MFP_QSPI1_SS          (0x0EUL<<SYS_GPC_MFPL_PC5MFP_Pos)  /*!< 1st QSPI1 slave select pin. \hideinitializer */
#define SYS_GPC_MFPL_PC6MFP_GPIO              (0x00UL<<SYS_GPC_MFPL_PC6MFP_Pos)  /*!< General purpose digital I/O pin. \hideinitializer */
#define SYS_GPC_MFPL_PC6MFP_EBI_AD8           (0x02UL<<SYS_GPC_MFPL_PC6MFP_Pos)  /*!< EBI address/data bus bit8. \hideinitializer */
#define SYS_GPC_MFPL_PC6MFP_EMAC_RMII_RXD1    (0x03UL<<SYS_GPC_MFPL_PC6MFP_Pos)  /*!< RMII Receive Data bus bit 1. \hideinitializer */
#define SYS_GPC_MFPL_PC6MFP_SPI1_MOSI         (0x04UL<<SYS_GPC_MFPL_PC6MFP_Pos)  /*!< 1st SPI1 MOSI (Master Out, Slave In) pin. \hideinitializer */
#define SYS_GPC_MFPL_PC6MFP_UART4_RXD         (0x05UL<<SYS_GPC_MFPL_PC6MFP_Pos)  /*!< Data receiver input pin for UART4. \hideinitializer */
#define SYS_GPC_MFPL_PC6MFP_SC2_RST           (0x06UL<<SYS_GPC_MFPL_PC6MFP_Pos)  /*!< SmartCard2 reset pin. \hideinitializer */
#define SYS_GPC_MFPL_PC6MFP_UART0_nRTS        (0x07UL<<SYS_GPC_MFPL_PC6MFP_Pos)  /*!< Request to Send output pin for UART0. \hideinitializer */
#define SYS_GPC_MFPL_PC6MFP_I2C1_SMBSUS       (0x08UL<<SYS_GPC_MFPL_PC6MFP_Pos)  /*!< I2C1 SMBus SMBSUS# pin (PMBus CONTROL pin)  \hideinitializer */
#define SYS_GPC_MFPL_PC6MFP_UART6_RXD         (0x09UL<<SYS_GPC_MFPL_PC6MFP_Pos)  /*!< Data receiver input pin for UART6.  \hideinitializer */
#define SYS_GPC_MFPL_PC6MFP_EPWM1_CH3         (0x0BUL<<SYS_GPC_MFPL_PC6MFP_Pos)  /*!< EPWM1 channel3 output/capture input. \hideinitializer */
#define SYS_GPC_MFPL_PC6MFP_BPWM1_CH1         (0x0CUL<<SYS_GPC_MFPL_PC6MFP_Pos)  /*!< BPWM1 channel1 output/capture input. \hideinitializer */
#define SYS_GPC_MFPL_PC6MFP_TM1               (0x0EUL<<SYS_GPC_MFPL_PC6MFP_Pos)  /*!< Timer1 event counter input / toggle output  \hideinitializer */
#define SYS_GPC_MFPL_PC6MFP_INT2              (0x0FUL<<SYS_GPC_MFPL_PC6MFP_Pos)  /*!< External interrupt2 input pin. \hideinitializer */
#define SYS_GPC_MFPL_PC7MFP_GPIO              (0x00UL<<SYS_GPC_MFPL_PC7MFP_Pos)  /*!< General purpose digital I/O pin. \hideinitializer */
#define SYS_GPC_MFPL_PC7MFP_EBI_AD9           (0x02UL<<SYS_GPC_MFPL_PC7MFP_Pos)  /*!< EBI address/data bus bit9. \hideinitializer */
#define SYS_GPC_MFPL_PC7MFP_EMAC_RMII_RXD0    (0x03UL<<SYS_GPC_MFPL_PC7MFP_Pos)  /*!< RMII Receive Data bus bit 0. \hideinitializer */
#define SYS_GPC_MFPL_PC7MFP_SPI1_MISO         (0x04UL<<SYS_GPC_MFPL_PC7MFP_Pos)  /*!< 1st SPI1 MISO (Master In, Slave Out) pin. \hideinitializer */
#define SYS_GPC_MFPL_PC7MFP_UART4_TXD         (0x05UL<<SYS_GPC_MFPL_PC7MFP_Pos)  /*!< Data transmitter output pin for UART4. \hideinitializer */
#define SYS_GPC_MFPL_PC7MFP_SC2_PWR           (0x06UL<<SYS_GPC_MFPL_PC7MFP_Pos)  /*!< SmartCard2 power pin. \hideinitializer */
#define SYS_GPC_MFPL_PC7MFP_UART0_nCTS        (0x07UL<<SYS_GPC_MFPL_PC7MFP_Pos)  /*!< Clear to Send input pin for UART0. \hideinitializer */
#define SYS_GPC_MFPL_PC7MFP_I2C1_SMBAL        (0x08UL<<SYS_GPC_MFPL_PC7MFP_Pos)  /*!< I2C1 SMBus SMBALTER# pin  \hideinitializer */
#define SYS_GPC_MFPL_PC7MFP_UART6_TXD         (0x09UL<<SYS_GPC_MFPL_PC7MFP_Pos)  /*!< Data transmitter output pin for UART6. \hideinitializer */
#define SYS_GPC_MFPL_PC7MFP_EPWM1_CH2         (0x0BUL<<SYS_GPC_MFPL_PC7MFP_Pos)  /*!< EPWM1 channel2 output/capture input. \hideinitializer */
#define SYS_GPC_MFPL_PC7MFP_BPWM1_CH0         (0x0CUL<<SYS_GPC_MFPL_PC7MFP_Pos)  /*!< BPWM1 channel0 output/capture input. \hideinitializer */
#define SYS_GPC_MFPL_PC7MFP_TM0               (0x0EUL<<SYS_GPC_MFPL_PC7MFP_Pos)  /*!< Timer0 event counter input / toggle output  \hideinitializer */
#define SYS_GPC_MFPL_PC7MFP_INT3              (0x0FUL<<SYS_GPC_MFPL_PC7MFP_Pos)  /*!< External interrupt3 input pin. \hideinitializer */
/********************* Bit definition of GPC_MFPH register **********************/
#define SYS_GPC_MFPH_PC8MFP_GPIO              (0x00UL<<SYS_GPC_MFPH_PC8MFP_Pos)  /*!< General purpose digital I/O pin. \hideinitializer */
#define SYS_GPC_MFPH_PC8MFP_EBI_ADR16         (0x02UL<<SYS_GPC_MFPH_PC8MFP_Pos)  /*!< EBI address/data bus bit*. \hideinitializer */
#define SYS_GPC_MFPH_PC8MFP_EMAC_RMII_REFCLK  (0x03UL<<SYS_GPC_MFPH_PC8MFP_Pos)  /*!< EMAC mode clock input. \hideinitializer */
#define SYS_GPC_MFPH_PC8MFP_I2C0_SDA          (0x04UL<<SYS_GPC_MFPH_PC8MFP_Pos)  /*!< I2C0 data input/output pin. \hideinitializer */
#define SYS_GPC_MFPH_PC8MFP_UART4_nCTS        (0x05UL<<SYS_GPC_MFPH_PC8MFP_Pos)  /*!< Clear to Send input pin for UART4. \hideinitializer */
#define SYS_GPC_MFPH_PC8MFP_UART1_RXD         (0x08UL<<SYS_GPC_MFPH_PC8MFP_Pos)  /*!< Data receiver input pin for UART1. \hideinitializer */
#define SYS_GPC_MFPH_PC8MFP_EPWM1_CH1         (0x0BUL<<SYS_GPC_MFPH_PC8MFP_Pos)  /*!< EPWM1 channel1 output/capture input. \hideinitializer */
#define SYS_GPC_MFPH_PC8MFP_BPWM1_CH4         (0x0CUL<<SYS_GPC_MFPH_PC8MFP_Pos)  /*!< BPWM1 channel4 output/capture input. \hideinitializer */
#define SYS_GPC_MFPH_PC9MFP_GPIO              (0x00UL<<SYS_GPC_MFPH_PC9MFP_Pos)  /*!< General purpose digital I/O pin. \hideinitializer */
#define SYS_GPC_MFPH_PC9MFP_EBI_ADR7          (0x02UL<<SYS_GPC_MFPH_PC9MFP_Pos)  /*!< EBI address/data bus bit*. \hideinitializer */
#define SYS_GPC_MFPH_PC9MFP_UART6_nCTS        (0x05UL<<SYS_GPC_MFPH_PC9MFP_Pos)  /*!< Clear to Send input pin for UART6. \hideinitializer */
#define SYS_GPC_MFPH_PC9MFP_SPI3_SS           (0x06UL<<SYS_GPC_MFPH_PC9MFP_Pos)  /*!< 1st SPI3 slave select pin. \hideinitializer */
#define SYS_GPC_MFPH_PC9MFP_UART3_RXD         (0x07UL<<SYS_GPC_MFPH_PC9MFP_Pos)  /*!< Data receiver input pin for UART3. \hideinitializer */
#define SYS_GPC_MFPH_PC9MFP_CAN1_RXD          (0x09UL<<SYS_GPC_MFPH_PC9MFP_Pos)  /*!< CAN1 bus receiver input. \hideinitializer */
#define SYS_GPC_MFPH_PC9MFP_EPWM1_CH3         (0x0CUL<<SYS_GPC_MFPH_PC9MFP_Pos)  /*!< EPWM1 channel3 output/capture input. \hideinitializer */
#define SYS_GPC_MFPH_PC9MFP_EADC1_ST          (0x0EUL<<SYS_GPC_MFPH_PC9MFP_Pos)  /*!< EADC external trigger input. \hideinitializer */
#define SYS_GPC_MFPH_PC10MFP_GPIO             (0x00UL<<SYS_GPC_MFPH_PC10MFP_Pos) /*!< General purpose digital I/O pin. \hideinitializer */
#define SYS_GPC_MFPH_PC10MFP_EBI_ADR6         (0x02UL<<SYS_GPC_MFPH_PC10MFP_Pos) /*!< EBI address/data bus bit*. \hideinitializer */
#define SYS_GPC_MFPH_PC10MFP_UART6_nRTS       (0x05UL<<SYS_GPC_MFPH_PC10MFP_Pos) /*!< Request to Send output pin for UART6. \hideinitializer */
#define SYS_GPC_MFPH_PC10MFP_SPI3_CLK         (0x06UL<<SYS_GPC_MFPH_PC10MFP_Pos) /*!< SPI3 serial clock pin. \hideinitializer */
#define SYS_GPC_MFPH_PC10MFP_UART3_TXD        (0x07UL<<SYS_GPC_MFPH_PC10MFP_Pos) /*!< Data transmitter output pin for UART3. \hideinitializer */
#define SYS_GPC_MFPH_PC10MFP_CAN1_TXD         (0x09UL<<SYS_GPC_MFPH_PC10MFP_Pos) /*!< CAN1 bus transmitter output. \hideinitializer */
#define SYS_GPC_MFPH_PC10MFP_ECAP1_IC0        (0x0BUL<<SYS_GPC_MFPH_PC10MFP_Pos) /*!< Input 0 of enhanced capture unit 1. \hideinitializer */
#define SYS_GPC_MFPH_PC10MFP_EPWM1_CH2        (0x0CUL<<SYS_GPC_MFPH_PC10MFP_Pos) /*!< EPWM1 channel2 output/capture input. \hideinitializer */
#define SYS_GPC_MFPH_PC10MFP_EADC1_ST         (0x0EUL<<SYS_GPC_MFPH_PC10MFP_Pos) /*!< EADC external trigger input. \hideinitializer */
#define SYS_GPC_MFPH_PC11MFP_GPIO             (0x00UL<<SYS_GPC_MFPH_PC11MFP_Pos) /*!< General purpose digital I/O pin. \hideinitializer */
#define SYS_GPC_MFPH_PC11MFP_EBI_ADR5         (0x02UL<<SYS_GPC_MFPH_PC11MFP_Pos) /*!< EBI address/data bus bit*. \hideinitializer */
#define SYS_GPC_MFPH_PC11MFP_UART0_RXD        (0x03UL<<SYS_GPC_MFPH_PC11MFP_Pos) /*!< Data receiver input pin for UART0. \hideinitializer */
#define SYS_GPC_MFPH_PC11MFP_I2C0_SDA         (0x04UL<<SYS_GPC_MFPH_PC11MFP_Pos) /*!< I2C0 data input/output pin. \hideinitializer */
#define SYS_GPC_MFPH_PC11MFP_UART6_RXD        (0x05UL<<SYS_GPC_MFPH_PC11MFP_Pos) /*!< Data receiver input pin for UART6. \hideinitializer */
#define SYS_GPC_MFPH_PC11MFP_SPI3_MOSI        (0x06UL<<SYS_GPC_MFPH_PC11MFP_Pos) /*!< 1st SPI3 MOSI (Master Out, Slave In) pin. \hideinitializer */
#define SYS_GPC_MFPH_PC11MFP_ECAP1_IC1        (0x0BUL<<SYS_GPC_MFPH_PC11MFP_Pos) /*!< Input 1 of enhanced capture unit 1. \hideinitializer */
#define SYS_GPC_MFPH_PC11MFP_EPWM1_CH1        (0x0CUL<<SYS_GPC_MFPH_PC11MFP_Pos) /*!< EPWM1 channel1 output/capture input. \hideinitializer */
#define SYS_GPC_MFPH_PC11MFP_ACMP1_O          (0x0EUL<<SYS_GPC_MFPH_PC11MFP_Pos) /*!< Analog comparator1 output. \hideinitializer */
#define SYS_GPC_MFPH_PC12MFP_GPIO             (0x00UL<<SYS_GPC_MFPH_PC12MFP_Pos) /*!< General purpose digital I/O pin. \hideinitializer */
#define SYS_GPC_MFPH_PC12MFP_EBI_ADR4         (0x02UL<<SYS_GPC_MFPH_PC12MFP_Pos) /*!< EBI address/data bus bit*. \hideinitializer */
#define SYS_GPC_MFPH_PC12MFP_UART0_TXD        (0x03UL<<SYS_GPC_MFPH_PC12MFP_Pos) /*!< Data transmitter output pin for UART0. \hideinitializer */
#define SYS_GPC_MFPH_PC12MFP_I2C0_SCL         (0x04UL<<SYS_GPC_MFPH_PC12MFP_Pos) /*!< I2C0 clock pin. \hideinitializer */
#define SYS_GPC_MFPH_PC12MFP_UART6_TXD        (0x05UL<<SYS_GPC_MFPH_PC12MFP_Pos) /*!< Data transmitter output pin for UART6. \hideinitializer */
#define SYS_GPC_MFPH_PC12MFP_SPI3_MISO        (0x06UL<<SYS_GPC_MFPH_PC12MFP_Pos) /*!< 1st SPI3 MISO (Master In, Slave Out) pin. \hideinitializer */
#define SYS_GPC_MFPH_PC12MFP_SC0_nCD          (0x09UL<<SYS_GPC_MFPH_PC12MFP_Pos) /*!< SmartCard0 card detect pin. \hideinitializer */
#define SYS_GPC_MFPH_PC12MFP_ECAP1_IC2        (0x0BUL<<SYS_GPC_MFPH_PC12MFP_Pos) /*!< Input 1 of enhanced capture unit 2. \hideinitializer */
#define SYS_GPC_MFPH_PC12MFP_EPWM1_CH0        (0x0CUL<<SYS_GPC_MFPH_PC12MFP_Pos) /*!< EPWM1 channel0 output/capture input. \hideinitializer */
#define SYS_GPC_MFPH_PC12MFP_ACMP0_O          (0x0EUL<<SYS_GPC_MFPH_PC12MFP_Pos) /*!< Analog comparator0 output. \hideinitializer */
#define SYS_GPC_MFPH_PC13MFP_GPIO             (0x00UL<<SYS_GPC_MFPH_PC13MFP_Pos) /*!< General purpose digital I/O pin. \hideinitializer */
#define SYS_GPC_MFPH_PC13MFP_EADC1_CH3        (0x01UL<<SYS_GPC_MFPH_PC13MFP_Pos) /*!< EADC1 channel3 analog input. \hideinitializer */
#define SYS_GPC_MFPH_PC13MFP_EBI_ADR10        (0x02UL<<SYS_GPC_MFPH_PC13MFP_Pos) /*!< EBI address/data bus bit*. \hideinitializer */
#define SYS_GPC_MFPH_PC13MFP_SC2_nCD          (0x03UL<<SYS_GPC_MFPH_PC13MFP_Pos) /*!< SmartCard2 card detect pin. \hideinitializer */
#define SYS_GPC_MFPH_PC13MFP_SPI2_I2SMCLK     (0x04UL<<SYS_GPC_MFPH_PC13MFP_Pos) /*!< SPI2 I2S master clock output pin. \hideinitializer */
#define SYS_GPC_MFPH_PC13MFP_CAN1_TXD         (0x05UL<<SYS_GPC_MFPH_PC13MFP_Pos) /*!< CAN1 bus transmitter output. \hideinitializer */
#define SYS_GPC_MFPH_PC13MFP_USCI0_CTL0       (0x06UL<<SYS_GPC_MFPH_PC13MFP_Pos) /*!< USCI0 control0 pin. \hideinitializer */
#define SYS_GPC_MFPH_PC13MFP_UART2_TXD        (0x07UL<<SYS_GPC_MFPH_PC13MFP_Pos) /*!< Data transmitter output pin for UART2. \hideinitializer */
#define SYS_GPC_MFPH_PC13MFP_BPWM0_CH4        (0x09UL<<SYS_GPC_MFPH_PC13MFP_Pos) /*!< BPWM0 channel4 output/capture input. \hideinitializer */
#define SYS_GPC_MFPH_PC13MFP_CLKO             (0x0DUL<<SYS_GPC_MFPH_PC13MFP_Pos) /*!< Clock Output pin. \hideinitializer */
#define SYS_GPC_MFPH_PC13MFP_EADC0_ST         (0x0EUL<<SYS_GPC_MFPH_PC13MFP_Pos) /*!< EADC external trigger input. \hideinitializer */
#define SYS_GPC_MFPH_PC14MFP_GPIO             (0x00UL<<SYS_GPC_MFPH_PC14MFP_Pos) /*!< General purpose digital I/O pin. \hideinitializer */
#define SYS_GPC_MFPH_PC14MFP_EBI_AD11         (0x02UL<<SYS_GPC_MFPH_PC14MFP_Pos) /*!< EBI address/data bus bit1. \hideinitializer */
#define SYS_GPC_MFPH_PC14MFP_SC1_nCD          (0x03UL<<SYS_GPC_MFPH_PC14MFP_Pos) /*!< SmartCard1 card detect pin. \hideinitializer */
#define SYS_GPC_MFPH_PC14MFP_SPI0_I2SMCLK     (0x04UL<<SYS_GPC_MFPH_PC14MFP_Pos) /*!< SPI0 I2S master clock output pin. \hideinitializer */
#define SYS_GPC_MFPH_PC14MFP_USCI0_CTL0       (0x05UL<<SYS_GPC_MFPH_PC14MFP_Pos) /*!< USCI0 control0 pin. \hideinitializer */
#define SYS_GPC_MFPH_PC14MFP_QSPI0_CLK        (0x06UL<<SYS_GPC_MFPH_PC14MFP_Pos) /*!< QSPI0 serial clock pin. \hideinitializer */
#define SYS_GPC_MFPH_PC14MFP_EPWM0_SYNC_IN    (0x0BUL<<SYS_GPC_MFPH_PC14MFP_Pos) /*!< EPWM0 counter synchronous trigger input pin. \hideinitializer */
#define SYS_GPC_MFPH_PC14MFP_ETM_TRACE_CLK    (0x0CUL<<SYS_GPC_MFPH_PC14MFP_Pos) /*!< ETM Rx clock input pin. \hideinitializer */
#define SYS_GPC_MFPH_PC14MFP_TM1              (0x0DUL<<SYS_GPC_MFPH_PC14MFP_Pos) /*!< Timer1 event counter input / toggle output  \hideinitializer */
#define SYS_GPC_MFPH_PC14MFP_USB_VBUS_ST      (0x0EUL<<SYS_GPC_MFPH_PC14MFP_Pos) /*!< Power supply from USB Full speed host or HUB. \hideinitializer */
#define SYS_GPC_MFPH_PC14MFP_HSUSB_VBUS_ST    (0x0FUL<<SYS_GPC_MFPH_PC14MFP_Pos) /*!< Power supply from USB High speed host or HUB. \hideinitializer */
/********************* Bit definition of GPD_MFPL register **********************/
#define SYS_GPD_MFPL_PD0MFP_GPIO              (0x00UL<<SYS_GPD_MFPL_PD0MFP_Pos)  /*!< General purpose digital I/O pin. \hideinitializer */
#define SYS_GPD_MFPL_PD0MFP_EBI_AD13          (0x02UL<<SYS_GPD_MFPL_PD0MFP_Pos)  /*!< EBI address/data bus bit1. \hideinitializer */
#define SYS_GPD_MFPL_PD0MFP_USCI0_CLK         (0x03UL<<SYS_GPD_MFPL_PD0MFP_Pos)  /*!< USCI0 clock pin. \hideinitializer */
#define SYS_GPD_MFPL_PD0MFP_SPI0_MOSI         (0x04UL<<SYS_GPD_MFPL_PD0MFP_Pos)  /*!< 1st SPI0 MOSI (Master Out, Slave In) pin. \hideinitializer */
#define SYS_GPD_MFPL_PD0MFP_UART3_RXD         (0x05UL<<SYS_GPD_MFPL_PD0MFP_Pos)  /*!< Data receiver input pin for UART3. \hideinitializer */
#define SYS_GPD_MFPL_PD0MFP_I2C2_SDA          (0x06UL<<SYS_GPD_MFPL_PD0MFP_Pos)  /*!< I2C2 data input/output pin. \hideinitializer */
#define SYS_GPD_MFPL_PD0MFP_SC2_CLK           (0x07UL<<SYS_GPD_MFPL_PD0MFP_Pos)  /*!< SmartCard2 clock pin. \hideinitializer */
#define SYS_GPD_MFPL_PD0MFP_TM2               (0x0EUL<<SYS_GPD_MFPL_PD0MFP_Pos)  /*!< Timer2 event counter input / toggle output  \hideinitializer */
#define SYS_GPD_MFPL_PD1MFP_GPIO              (0x00UL<<SYS_GPD_MFPL_PD1MFP_Pos)  /*!< General purpose digital I/O pin. \hideinitializer */
#define SYS_GPD_MFPL_PD1MFP_EBI_AD12          (0x02UL<<SYS_GPD_MFPL_PD1MFP_Pos)  /*!< EBI address/data bus bit1. \hideinitializer */
#define SYS_GPD_MFPL_PD1MFP_USCI0_DAT0        (0x03UL<<SYS_GPD_MFPL_PD1MFP_Pos)  /*!< USCI0 data0 pin. \hideinitializer */
#define SYS_GPD_MFPL_PD1MFP_SPI0_MISO         (0x04UL<<SYS_GPD_MFPL_PD1MFP_Pos)  /*!< 1st SPI0 MISO (Master In, Slave Out) pin. \hideinitializer */
#define SYS_GPD_MFPL_PD1MFP_UART3_TXD         (0x05UL<<SYS_GPD_MFPL_PD1MFP_Pos)  /*!< Data transmitter output pin for UART3. \hideinitializer */
#define SYS_GPD_MFPL_PD1MFP_I2C2_SCL          (0x06UL<<SYS_GPD_MFPL_PD1MFP_Pos)  /*!< I2C2 clock pin. \hideinitializer */
#define SYS_GPD_MFPL_PD1MFP_SC2_DAT           (0x07UL<<SYS_GPD_MFPL_PD1MFP_Pos)  /*!< SmartCard2 data pin. \hideinitializer */
#define SYS_GPD_MFPL_PD2MFP_GPIO              (0x00UL<<SYS_GPD_MFPL_PD2MFP_Pos)  /*!< General purpose digital I/O pin. \hideinitializer */
#define SYS_GPD_MFPL_PD2MFP_EBI_AD11          (0x02UL<<SYS_GPD_MFPL_PD2MFP_Pos)  /*!< EBI address/data bus bit1. \hideinitializer */
#define SYS_GPD_MFPL_PD2MFP_USCI0_DAT1        (0x03UL<<SYS_GPD_MFPL_PD2MFP_Pos)  /*!< USCI0 data1 pin. \hideinitializer */
#define SYS_GPD_MFPL_PD2MFP_SPI0_CLK          (0x04UL<<SYS_GPD_MFPL_PD2MFP_Pos)  /*!< SPI0 serial clock pin. \hideinitializer */
#define SYS_GPD_MFPL_PD2MFP_UART3_nCTS        (0x05UL<<SYS_GPD_MFPL_PD2MFP_Pos)  /*!< Clear to Send input pin for UART3. \hideinitializer */
#define SYS_GPD_MFPL_PD2MFP_SC2_RST           (0x07UL<<SYS_GPD_MFPL_PD2MFP_Pos)  /*!< SmartCard2 reset pin. \hideinitializer */
#define SYS_GPD_MFPL_PD2MFP_UART0_RXD         (0x09UL<<SYS_GPD_MFPL_PD2MFP_Pos)  /*!< Data receiver input pin for UART0. \hideinitializer */
#define SYS_GPD_MFPL_PD3MFP_GPIO              (0x00UL<<SYS_GPD_MFPL_PD3MFP_Pos)  /*!< General purpose digital I/O pin. \hideinitializer */
#define SYS_GPD_MFPL_PD3MFP_EBI_AD10          (0x02UL<<SYS_GPD_MFPL_PD3MFP_Pos)  /*!< EBI address/data bus bit1. \hideinitializer */
#define SYS_GPD_MFPL_PD3MFP_USCI0_CTL1        (0x03UL<<SYS_GPD_MFPL_PD3MFP_Pos)  /*!< USCI0 control1 pin. \hideinitializer */
#define SYS_GPD_MFPL_PD3MFP_SPI0_SS           (0x04UL<<SYS_GPD_MFPL_PD3MFP_Pos)  /*!< 1st SPI0 slave select pin. \hideinitializer */
#define SYS_GPD_MFPL_PD3MFP_UART3_nRTS        (0x05UL<<SYS_GPD_MFPL_PD3MFP_Pos)  /*!< Request to Send output pin for UART3. \hideinitializer */
#define SYS_GPD_MFPL_PD3MFP_USCI1_CTL0        (0x06UL<<SYS_GPD_MFPL_PD3MFP_Pos)  /*!< USCI1 control0 pin. \hideinitializer */
#define SYS_GPD_MFPL_PD3MFP_SC2_PWR           (0x07UL<<SYS_GPD_MFPL_PD3MFP_Pos)  /*!< SmartCard2 power pin. \hideinitializer */
#define SYS_GPD_MFPL_PD3MFP_SC1_nCD           (0x08UL<<SYS_GPD_MFPL_PD3MFP_Pos)  /*!< SmartCard1 card detect pin. \hideinitializer */
#define SYS_GPD_MFPL_PD3MFP_UART0_TXD         (0x09UL<<SYS_GPD_MFPL_PD3MFP_Pos)  /*!< Data transmitter output pin for UART0. \hideinitializer */
#define SYS_GPD_MFPL_PD4MFP_GPIO              (0x00UL<<SYS_GPD_MFPL_PD4MFP_Pos)  /*!< General purpose digital I/O pin. \hideinitializer */
#define SYS_GPD_MFPL_PD4MFP_USCI0_CTL0        (0x03UL<<SYS_GPD_MFPL_PD4MFP_Pos)  /*!< USCI0 control0 pin. \hideinitializer */
#define SYS_GPD_MFPL_PD4MFP_I2C1_SDA          (0x04UL<<SYS_GPD_MFPL_PD4MFP_Pos)  /*!< I2C1 data input/output pin. \hideinitializer */
#define SYS_GPD_MFPL_PD4MFP_SPI1_SS           (0x05UL<<SYS_GPD_MFPL_PD4MFP_Pos)  /*!< 1st SPI1 slave select pin. \hideinitializer */
#define SYS_GPD_MFPL_PD4MFP_USCI1_CTL1        (0x06UL<<SYS_GPD_MFPL_PD4MFP_Pos)  /*!< USCI1 control1 pin. \hideinitializer */
#define SYS_GPD_MFPL_PD4MFP_SC1_CLK           (0x08UL<<SYS_GPD_MFPL_PD4MFP_Pos)  /*!< SmartCard1 clock pin. \hideinitializer */
#define SYS_GPD_MFPL_PD4MFP_USB_VBUS_ST       (0x0EUL<<SYS_GPD_MFPL_PD4MFP_Pos)  /*!< Power supply from USB Full speed host or HUB. \hideinitializer */
#define SYS_GPD_MFPL_PD5MFP_GPIO              (0x00UL<<SYS_GPD_MFPL_PD5MFP_Pos)  /*!< General purpose digital I/O pin. \hideinitializer */
#define SYS_GPD_MFPL_PD5MFP_I2C1_SCL          (0x04UL<<SYS_GPD_MFPL_PD5MFP_Pos)  /*!< I2C1 clock pin. \hideinitializer */
#define SYS_GPD_MFPL_PD5MFP_SPI1_CLK          (0x05UL<<SYS_GPD_MFPL_PD5MFP_Pos)  /*!< SPI1 serial clock pin. \hideinitializer */
#define SYS_GPD_MFPL_PD5MFP_USCI1_DAT0        (0x06UL<<SYS_GPD_MFPL_PD5MFP_Pos)  /*!< USCI1 data0 pin. \hideinitializer */
#define SYS_GPD_MFPL_PD5MFP_SC1_DAT           (0x08UL<<SYS_GPD_MFPL_PD5MFP_Pos)  /*!< SmartCard1 data pin. \hideinitializer */
#define SYS_GPD_MFPL_PD6MFP_GPIO              (0x00UL<<SYS_GPD_MFPL_PD6MFP_Pos)  /*!< General purpose digital I/O pin. \hideinitializer */
#define SYS_GPD_MFPL_PD6MFP_UART1_RXD         (0x03UL<<SYS_GPD_MFPL_PD6MFP_Pos)  /*!< Data receiver input pin for UART1. \hideinitializer */
#define SYS_GPD_MFPL_PD6MFP_I2C0_SDA          (0x04UL<<SYS_GPD_MFPL_PD6MFP_Pos)  /*!< I2C0 data input/output pin. \hideinitializer */
#define SYS_GPD_MFPL_PD6MFP_SPI1_MOSI         (0x05UL<<SYS_GPD_MFPL_PD6MFP_Pos)  /*!< 1st SPI1 MOSI (Master Out, Slave In) pin. \hideinitializer */
#define SYS_GPD_MFPL_PD6MFP_USCI1_DAT1        (0x06UL<<SYS_GPD_MFPL_PD6MFP_Pos)  /*!< USCI1 data1 pin. \hideinitializer */
#define SYS_GPD_MFPL_PD6MFP_SC1_RST           (0x08UL<<SYS_GPD_MFPL_PD6MFP_Pos)  /*!< SmartCard1 reset pin. \hideinitializer */
#define SYS_GPD_MFPL_PD7MFP_GPIO              (0x00UL<<SYS_GPD_MFPL_PD7MFP_Pos)  /*!< General purpose digital I/O pin. \hideinitializer */
#define SYS_GPD_MFPL_PD7MFP_UART1_TXD         (0x03UL<<SYS_GPD_MFPL_PD7MFP_Pos)  /*!< Data transmitter output pin for UART1. \hideinitializer */
#define SYS_GPD_MFPL_PD7MFP_I2C0_SCL          (0x04UL<<SYS_GPD_MFPL_PD7MFP_Pos)  /*!< I2C0 clock pin. \hideinitializer */
#define SYS_GPD_MFPL_PD7MFP_SPI1_MISO         (0x05UL<<SYS_GPD_MFPL_PD7MFP_Pos)  /*!< 1st SPI1 MISO (Master In, Slave Out) pin. \hideinitializer */
#define SYS_GPD_MFPL_PD7MFP_USCI1_CLK         (0x06UL<<SYS_GPD_MFPL_PD7MFP_Pos)  /*!< USCI1 clock pin. \hideinitializer */
#define SYS_GPD_MFPL_PD7MFP_SC1_PWR           (0x08UL<<SYS_GPD_MFPL_PD7MFP_Pos)  /*!< SmartCard1 power pin. \hideinitializer */
/********************* Bit definition of GPD_MFPH register **********************/
#define SYS_GPD_MFPH_PD8MFP_GPIO              (0x00UL<<SYS_GPD_MFPH_PD8MFP_Pos)  /*!< General purpose digital I/O pin. \hideinitializer */
#define SYS_GPD_MFPH_PD8MFP_EBI_AD6           (0x02UL<<SYS_GPD_MFPH_PD8MFP_Pos)  /*!< EBI address/data bus bit6. \hideinitializer */
#define SYS_GPD_MFPH_PD8MFP_I2C2_SDA          (0x03UL<<SYS_GPD_MFPH_PD8MFP_Pos)  /*!< I2C2 data input/output pin. \hideinitializer */
#define SYS_GPD_MFPH_PD8MFP_UART2_nRTS        (0x04UL<<SYS_GPD_MFPH_PD8MFP_Pos)  /*!< Request to Send output pin for UART2. \hideinitializer */
#define SYS_GPD_MFPH_PD8MFP_UART7_RXD         (0x05UL<<SYS_GPD_MFPH_PD8MFP_Pos)  /*!< Data receiver input pin for UART7. \hideinitializer */
#define SYS_GPD_MFPH_PD8MFP_CAN2_RXD          (0x06UL<<SYS_GPD_MFPH_PD8MFP_Pos)  /*!< CAN2 bus receiver input. \hideinitializer */
#define SYS_GPD_MFPH_PD9MFP_GPIO              (0x00UL<<SYS_GPD_MFPH_PD9MFP_Pos)  /*!< General purpose digital I/O pin. \hideinitializer */
#define SYS_GPD_MFPH_PD9MFP_EBI_AD7           (0x02UL<<SYS_GPD_MFPH_PD9MFP_Pos)  /*!< EBI address/data bus bit7. \hideinitializer */
#define SYS_GPD_MFPH_PD9MFP_I2C2_SCL          (0x03UL<<SYS_GPD_MFPH_PD9MFP_Pos)  /*!< I2C2 clock pin. \hideinitializer */
#define SYS_GPD_MFPH_PD9MFP_UART2_nCTS        (0x04UL<<SYS_GPD_MFPH_PD9MFP_Pos)  /*!< Clear to Send input pin for UART2. \hideinitializer */
#define SYS_GPD_MFPH_PD9MFP_UART7_TXD         (0x05UL<<SYS_GPD_MFPH_PD9MFP_Pos)  /*!< Data transmitter output pin for UART7. \hideinitializer */
#define SYS_GPD_MFPH_PD9MFP_CAN2_TXD          (0x06UL<<SYS_GPD_MFPH_PD9MFP_Pos)  /*!< CAN2 bus transmitter output. \hideinitializer */
#define SYS_GPD_MFPH_PD10MFP_GPIO             (0x00UL<<SYS_GPD_MFPH_PD10MFP_Pos) /*!< General purpose digital I/O pin. \hideinitializer */
#define SYS_GPD_MFPH_PD10MFP_OPA2_P           (0x01UL<<SYS_GPD_MFPH_PD10MFP_Pos) /*!< Operational amplifier positive input pin. \hideinitializer */
#define SYS_GPD_MFPH_PD10MFP_EADC1_CH0        (0x01UL<<SYS_GPD_MFPH_PD10MFP_Pos) /*!< EADC1 channel0 analog input. \hideinitializer */
#define SYS_GPD_MFPH_PD10MFP_EBI_nCS2         (0x02UL<<SYS_GPD_MFPH_PD10MFP_Pos) /*!< EBI chip select enable output pin. \hideinitializer */
#define SYS_GPD_MFPH_PD10MFP_UART1_RXD        (0x03UL<<SYS_GPD_MFPH_PD10MFP_Pos) /*!< Data receiver input pin for UART1. \hideinitializer */
#define SYS_GPD_MFPH_PD10MFP_CAN0_RXD         (0x04UL<<SYS_GPD_MFPH_PD10MFP_Pos) /*!< CAN0 bus receiver input. \hideinitializer */
#define SYS_GPD_MFPH_PD10MFP_QEI0_B           (0x0AUL<<SYS_GPD_MFPH_PD10MFP_Pos) /*!< Quadrature encoder phase B input of QEI Unit 0. \hideinitializer */
#define SYS_GPD_MFPH_PD10MFP_INT7             (0x0FUL<<SYS_GPD_MFPH_PD10MFP_Pos) /*!< External interrupt7 input pin. \hideinitializer */
#define SYS_GPD_MFPH_PD11MFP_GPIO             (0x00UL<<SYS_GPD_MFPH_PD11MFP_Pos) /*!< General purpose digital I/O pin. \hideinitializer */
#define SYS_GPD_MFPH_PD11MFP_EADC1_CH1        (0x01UL<<SYS_GPD_MFPH_PD11MFP_Pos) /*!< EADC1 channel1 analog input. \hideinitializer */
#define SYS_GPD_MFPH_PD11MFP_OPA2_N           (0x01UL<<SYS_GPD_MFPH_PD11MFP_Pos) /*!< Operational amplifier negative input pin. \hideinitializer */
#define SYS_GPD_MFPH_PD11MFP_EBI_nCS1         (0x02UL<<SYS_GPD_MFPH_PD11MFP_Pos) /*!< EBI chip select enable output pin. \hideinitializer */
#define SYS_GPD_MFPH_PD11MFP_UART1_TXD        (0x03UL<<SYS_GPD_MFPH_PD11MFP_Pos) /*!< Data transmitter output pin for UART1. \hideinitializer */
#define SYS_GPD_MFPH_PD11MFP_CAN0_TXD         (0x04UL<<SYS_GPD_MFPH_PD11MFP_Pos) /*!< CAN0 bus transmitter output. \hideinitializer */
#define SYS_GPD_MFPH_PD11MFP_QEI0_A           (0x0AUL<<SYS_GPD_MFPH_PD11MFP_Pos) /*!< Quadrature encoder phase A input of QEI Unit 0. \hideinitializer */
#define SYS_GPD_MFPH_PD11MFP_INT6             (0x0FUL<<SYS_GPD_MFPH_PD11MFP_Pos) /*!< External interrupt6 input pin. \hideinitializer */
#define SYS_GPD_MFPH_PD12MFP_GPIO             (0x00UL<<SYS_GPD_MFPH_PD12MFP_Pos) /*!< General purpose digital I/O pin. \hideinitializer */
#define SYS_GPD_MFPH_PD12MFP_OPA2_O           (0x01UL<<SYS_GPD_MFPH_PD12MFP_Pos) /*!< Operational amplifier output pin. \hideinitializer */
#define SYS_GPD_MFPH_PD12MFP_EADC1_CH2        (0x01UL<<SYS_GPD_MFPH_PD12MFP_Pos) /*!< EADC1 channel2 analog input. \hideinitializer */
#define SYS_GPD_MFPH_PD12MFP_EBI_nCS0         (0x02UL<<SYS_GPD_MFPH_PD12MFP_Pos) /*!< EBI chip select enable output pin. \hideinitializer */
#define SYS_GPD_MFPH_PD12MFP_CAN1_RXD         (0x05UL<<SYS_GPD_MFPH_PD12MFP_Pos) /*!< CAN1 bus receiver input. \hideinitializer */
#define SYS_GPD_MFPH_PD12MFP_UART2_RXD        (0x07UL<<SYS_GPD_MFPH_PD12MFP_Pos) /*!< Data receiver input pin for UART2. \hideinitializer */
#define SYS_GPD_MFPH_PD12MFP_BPWM0_CH5        (0x09UL<<SYS_GPD_MFPH_PD12MFP_Pos) /*!< BPWM0 channel5 output/capture input. \hideinitializer */
#define SYS_GPD_MFPH_PD12MFP_QEI0_INDEX       (0x0AUL<<SYS_GPD_MFPH_PD12MFP_Pos) /*!< Quadrature encoder index input of QEI Unit 0. \hideinitializer */
#define SYS_GPD_MFPH_PD12MFP_CLKO             (0x0DUL<<SYS_GPD_MFPH_PD12MFP_Pos) /*!< Clock Output pin. \hideinitializer */
#define SYS_GPD_MFPH_PD12MFP_EADC0_ST         (0x0EUL<<SYS_GPD_MFPH_PD12MFP_Pos) /*!< EADC external trigger input. \hideinitializer */
#define SYS_GPD_MFPH_PD12MFP_INT5             (0x0FUL<<SYS_GPD_MFPH_PD12MFP_Pos) /*!< External interrupt5 input pin. \hideinitializer */
#define SYS_GPD_MFPH_PD13MFP_GPIO             (0x00UL<<SYS_GPD_MFPH_PD13MFP_Pos) /*!< General purpose digital I/O pin. \hideinitializer */
#define SYS_GPD_MFPH_PD13MFP_EBI_AD10         (0x02UL<<SYS_GPD_MFPH_PD13MFP_Pos) /*!< EBI address/data bus bit1. \hideinitializer */
#define SYS_GPD_MFPH_PD13MFP_SD0_nCD          (0x03UL<<SYS_GPD_MFPH_PD13MFP_Pos) /*!< SD/SDIO 0 card detect  \hideinitializer */
#define SYS_GPD_MFPH_PD13MFP_SPI0_I2SMCLK     (0x04UL<<SYS_GPD_MFPH_PD13MFP_Pos) /*!< SPI0 I2S master clock output pin. \hideinitializer */
#define SYS_GPD_MFPH_PD13MFP_SPI1_I2SMCLK     (0x05UL<<SYS_GPD_MFPH_PD13MFP_Pos) /*!< SPI1 I2S master clock output pin. \hideinitializer */
#define SYS_GPD_MFPH_PD13MFP_SC2_nCD          (0x07UL<<SYS_GPD_MFPH_PD13MFP_Pos) /*!< SmartCard2 card detect pin. \hideinitializer */
#define SYS_GPD_MFPH_PD14MFP_GPIO             (0x00UL<<SYS_GPD_MFPH_PD14MFP_Pos) /*!< General purpose digital I/O pin. \hideinitializer */
#define SYS_GPD_MFPH_PD14MFP_EBI_nCS0         (0x02UL<<SYS_GPD_MFPH_PD14MFP_Pos) /*!< EBI chip select enable output pin. \hideinitializer */
#define SYS_GPD_MFPH_PD14MFP_SPI3_I2SMCLK     (0x03UL<<SYS_GPD_MFPH_PD14MFP_Pos) /*!< SPI3 I2S master clock output pin. \hideinitializer */
#define SYS_GPD_MFPH_PD14MFP_SC1_nCD          (0x04UL<<SYS_GPD_MFPH_PD14MFP_Pos) /*!< SmartCard1 card detect pin. \hideinitializer */
#define SYS_GPD_MFPH_PD14MFP_SPI0_I2SMCLK     (0x05UL<<SYS_GPD_MFPH_PD14MFP_Pos) /*!< SPI0 I2S master clock output pin. \hideinitializer */
#define SYS_GPD_MFPH_PD14MFP_EPWM0_CH4        (0x0BUL<<SYS_GPD_MFPH_PD14MFP_Pos) /*!< EPWM0 channel4 output/capture input. \hideinitializer */
/********************* Bit definition of GPE_MFPL register **********************/
#define SYS_GPE_MFPL_PE0MFP_GPIO              (0x00UL<<SYS_GPE_MFPL_PE0MFP_Pos)  /*!< General purpose digital I/O pin. \hideinitializer */
#define SYS_GPE_MFPL_PE0MFP_EBI_AD11          (0x02UL<<SYS_GPE_MFPL_PE0MFP_Pos)  /*!< EBI address/data bus bit1. \hideinitializer */
#define SYS_GPE_MFPL_PE0MFP_QSPI0_MOSI0       (0x03UL<<SYS_GPE_MFPL_PE0MFP_Pos)  /*!< 1st QSPI0 MOSI (Master Out, Slave In) pin. \hideinitializer */
#define SYS_GPE_MFPL_PE0MFP_SC2_CLK           (0x04UL<<SYS_GPE_MFPL_PE0MFP_Pos)  /*!< SmartCard2 clock pin. \hideinitializer */
#define SYS_GPE_MFPL_PE0MFP_I2S0_MCLK         (0x05UL<<SYS_GPE_MFPL_PE0MFP_Pos)  /*!< I2S0 master clock output pin. \hideinitializer */
#define SYS_GPE_MFPL_PE0MFP_SPI1_MOSI         (0x06UL<<SYS_GPE_MFPL_PE0MFP_Pos)  /*!< 1st SPI1 MOSI (Master Out, Slave In) pin. \hideinitializer */
#define SYS_GPE_MFPL_PE0MFP_UART3_RXD         (0x07UL<<SYS_GPE_MFPL_PE0MFP_Pos)  /*!< Data receiver input pin for UART3. \hideinitializer */
#define SYS_GPE_MFPL_PE0MFP_I2C1_SDA          (0x08UL<<SYS_GPE_MFPL_PE0MFP_Pos)  /*!< I2C1 data input/output pin. \hideinitializer */
#define SYS_GPE_MFPL_PE0MFP_UART4_nRTS        (0x09UL<<SYS_GPE_MFPL_PE0MFP_Pos)  /*!< Request to Send output pin for UART4. \hideinitializer */
#define SYS_GPE_MFPL_PE1MFP_GPIO              (0x00UL<<SYS_GPE_MFPL_PE1MFP_Pos)  /*!< General purpose digital I/O pin. \hideinitializer */
#define SYS_GPE_MFPL_PE1MFP_EBI_AD10          (0x02UL<<SYS_GPE_MFPL_PE1MFP_Pos)  /*!< EBI address/data bus bit1. \hideinitializer */
#define SYS_GPE_MFPL_PE1MFP_QSPI0_MISO0       (0x03UL<<SYS_GPE_MFPL_PE1MFP_Pos)  /*!< 1st QSPI0 MISO (Master In, Slave Out) pin. \hideinitializer */
#define SYS_GPE_MFPL_PE1MFP_SC2_DAT           (0x04UL<<SYS_GPE_MFPL_PE1MFP_Pos)  /*!< SmartCard2 data pin. \hideinitializer */
#define SYS_GPE_MFPL_PE1MFP_I2S0_BCLK         (0x05UL<<SYS_GPE_MFPL_PE1MFP_Pos)  /*!< I2S0 bit clock pin. \hideinitializer */
#define SYS_GPE_MFPL_PE1MFP_SPI1_MISO         (0x06UL<<SYS_GPE_MFPL_PE1MFP_Pos)  /*!< 1st SPI1 MISO (Master In, Slave Out) pin. \hideinitializer */
#define SYS_GPE_MFPL_PE1MFP_UART3_TXD         (0x07UL<<SYS_GPE_MFPL_PE1MFP_Pos)  /*!< Data transmitter output pin for UART3. \hideinitializer */
#define SYS_GPE_MFPL_PE1MFP_I2C1_SCL          (0x08UL<<SYS_GPE_MFPL_PE1MFP_Pos)  /*!< I2C1 clock pin. \hideinitializer */
#define SYS_GPE_MFPL_PE1MFP_UART4_nCTS        (0x09UL<<SYS_GPE_MFPL_PE1MFP_Pos)  /*!< Clear to Send input pin for UART4. \hideinitializer */
#define SYS_GPE_MFPL_PE2MFP_GPIO              (0x00UL<<SYS_GPE_MFPL_PE2MFP_Pos)  /*!< General purpose digital I/O pin. \hideinitializer */
#define SYS_GPE_MFPL_PE2MFP_EBI_ALE           (0x02UL<<SYS_GPE_MFPL_PE2MFP_Pos)  /*!< EBI address latch enable output pin. \hideinitializer */
#define SYS_GPE_MFPL_PE2MFP_SD0_DAT0          (0x03UL<<SYS_GPE_MFPL_PE2MFP_Pos)  /*!< SD/SDIO 0 data line bit 0. \hideinitializer */
#define SYS_GPE_MFPL_PE2MFP_SPIM_MOSI         (0x04UL<<SYS_GPE_MFPL_PE2MFP_Pos)  /*!< 1st SPIM MOSI (Master Out, Slave In) pin. \hideinitializer */
#define SYS_GPE_MFPL_PE2MFP_SPI3_MOSI         (0x05UL<<SYS_GPE_MFPL_PE2MFP_Pos)  /*!< 1st SPI3 MOSI (Master Out, Slave In) pin. \hideinitializer */
#define SYS_GPE_MFPL_PE2MFP_SC0_CLK           (0x06UL<<SYS_GPE_MFPL_PE2MFP_Pos)  /*!< SmartCard0 clock pin. \hideinitializer */
#define SYS_GPE_MFPL_PE2MFP_USCI0_CLK         (0x07UL<<SYS_GPE_MFPL_PE2MFP_Pos)  /*!< USCI0 clock pin. \hideinitializer */
#define SYS_GPE_MFPL_PE2MFP_UART6_nCTS        (0x08UL<<SYS_GPE_MFPL_PE2MFP_Pos)  /*!< Clear to Send input pin for UART6. \hideinitializer */
#define SYS_GPE_MFPL_PE2MFP_UART7_RXD         (0x09UL<<SYS_GPE_MFPL_PE2MFP_Pos)  /*!< Data receiver input pin for UART7. \hideinitializer */
#define SYS_GPE_MFPL_PE2MFP_QEI0_B            (0x0BUL<<SYS_GPE_MFPL_PE2MFP_Pos)  /*!< Quadrature encoder phase B input of QEI Unit 0. \hideinitializer */
#define SYS_GPE_MFPL_PE2MFP_EPWM0_CH5         (0x0CUL<<SYS_GPE_MFPL_PE2MFP_Pos)  /*!< EPWM0 channel5 output/capture input. \hideinitializer */
#define SYS_GPE_MFPL_PE2MFP_BPWM0_CH0         (0x0DUL<<SYS_GPE_MFPL_PE2MFP_Pos)  /*!< BPWM0 channel0 output/capture input. \hideinitializer */
#define SYS_GPE_MFPL_PE3MFP_GPIO              (0x00UL<<SYS_GPE_MFPL_PE3MFP_Pos)  /*!< General purpose digital I/O pin. \hideinitializer */
#define SYS_GPE_MFPL_PE3MFP_EBI_MCLK          (0x02UL<<SYS_GPE_MFPL_PE3MFP_Pos)  /*!< EBI external clock output pin. \hideinitializer */
#define SYS_GPE_MFPL_PE3MFP_SD0_DAT1          (0x03UL<<SYS_GPE_MFPL_PE3MFP_Pos)  /*!< SD/SDIO 0 data line bit 1. \hideinitializer */
#define SYS_GPE_MFPL_PE3MFP_SPIM_MISO         (0x04UL<<SYS_GPE_MFPL_PE3MFP_Pos)  /*!< 1st SPIM MISO (Master In, Slave Out) pin. \hideinitializer */
#define SYS_GPE_MFPL_PE3MFP_SPI3_MISO         (0x05UL<<SYS_GPE_MFPL_PE3MFP_Pos)  /*!< 1st SPI3 MISO (Master In, Slave Out) pin. \hideinitializer */
#define SYS_GPE_MFPL_PE3MFP_SC0_DAT           (0x06UL<<SYS_GPE_MFPL_PE3MFP_Pos)  /*!< SmartCard0 data pin. \hideinitializer */
#define SYS_GPE_MFPL_PE3MFP_USCI0_DAT0        (0x07UL<<SYS_GPE_MFPL_PE3MFP_Pos)  /*!< USCI0 data0 pin. \hideinitializer */
#define SYS_GPE_MFPL_PE3MFP_UART6_nRTS        (0x08UL<<SYS_GPE_MFPL_PE3MFP_Pos)  /*!< Request to Send output pin for UART6. \hideinitializer */
#define SYS_GPE_MFPL_PE3MFP_UART7_TXD         (0x09UL<<SYS_GPE_MFPL_PE3MFP_Pos)  /*!< Data transmitter output pin for UART7. \hideinitializer */
#define SYS_GPE_MFPL_PE3MFP_QEI0_A            (0x0BUL<<SYS_GPE_MFPL_PE3MFP_Pos)  /*!< Quadrature encoder phase A input of QEI Unit 0. \hideinitializer */
#define SYS_GPE_MFPL_PE3MFP_EPWM0_CH4         (0x0CUL<<SYS_GPE_MFPL_PE3MFP_Pos)  /*!< EPWM0 channel4 output/capture input. \hideinitializer */
#define SYS_GPE_MFPL_PE3MFP_BPWM0_CH1         (0x0DUL<<SYS_GPE_MFPL_PE3MFP_Pos)  /*!< BPWM0 channel1 output/capture input. \hideinitializer */
#define SYS_GPE_MFPL_PE4MFP_GPIO              (0x00UL<<SYS_GPE_MFPL_PE4MFP_Pos)  /*!< General purpose digital I/O pin. \hideinitializer */
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
