EIectron/RadioNoob/Software/ELRSParser/main.h

typedef __INT8_TYPE__ s8;
typedef __INT16_TYPE__ s16;
typedef __INT32_TYPE__ s32;
typedef __UINT8_TYPE__ u8;
typedef __UINT16_TYPE__ u16;
typedef __UINT32_TYPE__ u32;
typedef __UINT64_TYPE__ u64;

#define CRSF_MAX_CHUNK_SIZE   58   // 64 - header - type - destination - origin
#define CRSF_MAX_CHUNKS        8   // not in specification. Max observed is 5 for ELRS 2.3 (HappyModel ES2400TX)   
#define CRSF_MAX_PARAMS       23 
#define CRSF_MAX_PACKET_LEN   64

enum data_type {
    UINT8          = 0,
    INT8           = 1,
    UINT16         = 2,
    INT16          = 3,
    FLOAT          = 8,
    TEXT_SELECTION = 9,
    STRING         = 10,
    FOLDER         = 11,
    INFO           = 12,
    COMMAND        = 13,
    OUT_OF_RANGE   = 127,
};

typedef struct {
    // common fields
    u8 device;            // device index of device parameter belongs to
    u8 id;                // Parameter number (starting from 1)
    u8 parent;            // Parent folder parameter number of the parent folder, 0 means root
    u8 chunk;
    enum data_type type;  // (Parameter type definitions and hidden bit)
    u8 hidden;            // set if hidden
    char *name;           // Null-terminated string
    char *options[50];    // size depending on data type
    void *value;
    u8 status;
    u8 count;

    // field presence depends on type
    u8 default_value;     // size depending on data type. Not present for COMMAND.
    u8 current_value;
    s32 min_value;        // not sent for string type
    s32 max_value;        // not sent for string type
    s32 step;             // Step size ( type float only otherwise this entry is not sent )
    u8 timeout;           // COMMAND timeout (100ms/count)
    u8 changed;           // flag if set needed when edit element is de-selected
    char *max_str;        // Longest choice length for text select
    union {
        u8 point;             // Decimal point ( type float only otherwise this entry is not sent )
        u8 text_sel;          // current value index for TEXT_SELECTION type
        u8 string_max_len;    // String max length ( for string type only )
        u8 status;            // Status for COMMANDs
    } u;
    union {
        char *info;
        char *unit;         // Unit ( Null-terminated string / not sent for type string and folder )
    } s;
} crsf_param_t;

enum cmd_status {
    READY               = 0,
    START               = 1,
    PROGRESS            = 2,
    CONFIRMATION_NEEDED = 3,
    CONFIRM             = 4,
    CANCEL              = 5,
    POLL                = 6
};

static struct {
    crsf_param_t *param;
    u32 time;
    u16 timeout;
    u8  dialog;
} command;

// Param: HooJ 
char param0[CRSF_MAX_PACKET_LEN] = {0xEA, 0x19, 0x2B, 0xEA, 0xEE, 0x0, 0x0, 0x0, 0xB, 0x48, 0x6F, 0x6F, 0x4A, 0x1, 0x2, 0x3, 0x4, 0x5, 0x9, 0xF, 0x12, 0x13, 0x14, 0x15, 0xFF, 0x0, 0x35, 0x3, 0x2, 0x15, 0x0, 0x8B, 0x0, 0x0, 0x0, 0x0, 0x0, 0x0, 0x0, 0x0, 0x0, 0x0, 0x0, 0x0, 0x0, 0x0, 0x0, 0x0, 0x0, 0x0, 0x0, 0x0, 0x0, 0x0, 0x0, 0x0, 0x0, 0x0, 0x0, 0x0, 0x0, 0x0, 0x0, 0x0};

// Param: Packet Rate, 50Hz(-115dBm);100Hz Full(-112dBm);150Hz(
char param1_1[CRSF_MAX_PACKET_LEN] = {0xEA, 0x3E, 0x2B, 0xEA, 0xEE, 0x1, 0x3, 0x0, 0x9, 0x50, 0x61, 0x63, 0x6B, 0x65, 0x74, 0x20, 0x52, 0x61, 0x74, 0x65, 0x0, 0x35, 0x30, 0x48, 0x7A, 0x28, 0x2D, 0x31, 0x31, 0x35, 0x64, 0x42, 0x6D, 0x29, 0x3B, 0x31, 0x30, 0x30, 0x48, 0x7A, 0x20, 0x46, 0x75, 0x6C, 0x6C, 0x28, 0x2D, 0x31, 0x31, 0x32, 0x64, 0x42, 0x6D, 0x29, 0x3B, 0x31, 0x35, 0x30, 0x48, 0x7A, 0x28, 0x2D, 0x31, 0x8A};

// Param: dBm);250Hz(-108dBm);333Hz Full(-105dBm);500Hz(-105dB%:, Hz Full(-105dBm);500Hz(-105dB%:
char param1_2[CRSF_MAX_PACKET_LEN] = {0xEA, 0x3E, 0x2B, 0xEA, 0xEE, 0x1, 0x2, 0x31, 0x32, 0x64, 0x42, 0x6D, 0x29, 0x3B, 0x32, 0x35, 0x30, 0x48, 0x7A, 0x28, 0x2D, 0x31, 0x30, 0x38, 0x64, 0x42, 0x6D, 0x29, 0x3B, 0x33, 0x33, 0x33, 0x48, 0x7A, 0x20, 0x46, 0x75, 0x6C, 0x6C, 0x28, 0x2D, 0x31, 0x30, 0x35, 0x64, 0x42, 0x6D, 0x29, 0x3B, 0x35, 0x30, 0x30, 0x48, 0x7A, 0x28, 0x2D, 0x31, 0x30, 0x35, 0x64, 0x42, 0x6D, 0x29, 0xE};


// Param: 250(-104dBm);D500(-104dBm);F500(-104dBm);F1000(-104d%:, Bm);F500(-104dBm);F1000(-104d%:
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



2B EA EE 0E 00 09 0D 53 65 6E 64 20



2B EA EE 0F 00 00 0B 57 69 46 69 20 43 6F 6E 6E 65 63



2B EA EE 10 00 0F 0D 45 6E 61 62 6C 65 20 57



2B EA EE 11 00 0F 0D 45 6E 61 62 6C 65 20 52 78 20 57



2B EA EE 12 00 00 0D 42 4C 45 20 4A 6F 79 73 74



2B EA EE 13 00 00 0D 42



2B EA EE 14 00 00 0C 42 61 64 2F 47 6F 6F 64



2B EA EE 15 00 00 0C 33 2E 33 2E 32 20 49 53 4D 32 47 34 00
